solosky/pixl.js/fw/application/src/i18n/de_DE.c

#include "string_id.h"
const char * const lang_de_DE[_L_COUNT] = {
    [_L_ON] = "AN",
    [_L_OFF] = "AUS",
    [_L_ON_F] = "[AN]",
    [_L_OFF_F] = "[AUS]",
    [_L_BACK] = "Zurück",
    [_L_ERR] = "Fehler",
    [_L_ERR_CODE] = "Fehlercode",
    [_L_FAILED] = "",
    [_L_BYTES] = "",
    [_L_APP_AMIIBO] = "Amiibo Emulator",
    [_L_APP_AMIIBOLINK] = "AmiiboLink",
    [_L_APP_BLE] = "BLE Dateitransfer",
    [_L_APP_BLE_TITLE] = "BLE Dateitransfer",
    [_L_APP_PLAYER] = "Videoplayer",
    [_L_APP_SET] = "Einstellungen",
    [_L_APP_SET_VERSION] = "Version",
    [_L_APP_SET_STORAGE_USED] = "Belegt",
    [_L_APP_SET_STORAGE] = "Externer Speicher",
    [_L_APP_SET_OLED_CONTRAST] = "Kontrast",
    [_L_APP_SET_OLED_CONTRAST_TITLE] = "Kontrast",
    [_L_APP_SET_LCD_BACKLIGHT] = "Beleuchtung",
    [_L_APP_SET_LCD_BACKLIGHT_TITLE] = "Helligkeit",
    [_L_APP_SET_ANIM] = "Menü Animation",
    [_L_APP_SET_LIPO_BAT] = "LiPO Batterie",
    [_L_APP_SET_SHOW_MEM_USAGE] = "Speicheranzeige",
    [_L_APP_SET_HIBERNATE] = "Schnelles Aufwachen",
    [_L_APP_SET_SLEEP_TIMEOUT] = "Standby nach",
    [_L_APP_SET_LANGUAGE] = "Sprache",
    [_L_APP_SET_GO_SLEEP] = "",
    [_L_APP_SET_DFU] = "Firmw. Aktualisierung",
    [_L_APP_SET_REBOOT] = "System Neustart",
    [_L_APP_SET_RESET_DEFAULT] = "Standardeinstellungen",
    [_L_APP_SET_RESET_DEFAULT_SUCCESS] = "Einstellungen zurückgesetzt!",
    [_L_APP_SET_RESET_DEFAULT_CONFIRM] = "Auf Standardeinstellungen zurücksetzen?",
    [_L_APP_SET_ABOUT] = "",
    [_L_APP_SET_ABOUT_OPEN_SOURCE_PROJECT] = "",
    [_L_APP_SET_ABOUT_LGPL_LICENSE] = "",
    [_L_APP_SET_APP_MGMT] = "",
    [_L_15S] = "15 Sekunden",
    [_L_30S] = "30 Sekunden",
    [_L_45S] = "45 Sekunden",
    [_L_1MIN] = "1 Minute",
    [_L_2MIN] = "2 Minuten",
    [_L_3MIN] = "3 Minuten",
    [_L_AMIIBO_KEY_UNLOADED] = "Amiibo Schlüssel fehlt",
    [_L_UPLOAD_KEY_RETAIL_BIN] = "Platzieren Sie die Datei key_retail.bin im Hauptverzeichnis des Speichers.",
    [_L_KNOW] = "Verstanden",
    [_L_RANDOM_GENERATION] = "Zufällige UUID",
    [_L_AUTO_RANDOM_GENERATION] = "Zufällige UUID (Automatisch)",
    [_L_SET_CUSTOM_ID] = "",
    [_L_INPUT_ID] = "",
    [_L_INAVLID_ID] = "",
    [_L_SHOW_QRCODE] = "QR Code",
    [_L_READ_ONLY] = "",
    [_L_DELETE_TAG] = "Tag löschen",
    [_L_DELETE_TAG_CONFIRM] = "Löschen von %s bestätigen?",
    [_L_BACK_TO_DETAILS] = "Zurück zu Tag Details",
    [_L_BACK_TO_FILE_LIST] = "Zurück zur Liste",
    [_L_BACK_TO_MAIN_MENU] = "Hauptmenü",
    [_L_FORMAT] = "Formatieren",
    [_L_FORMAT_STORAGE] = "Speicher formatieren",
    [_L_DELETE_ALL_DATA] = "Alle Daten löschen?",
    [_L_DELETING_MESSAGE] = "Formatiere...",
    [_L_MESSAGE] = "Meldung",
    [_L_CONFIRM] = "Bestätigen",
    [_L_CANCEL] = "Abbrechen",
    [_L_BACK_TO_LIST] = "Zurück zur Liste",
    [_L_NOT_MOUNTED] = "Speicher nicht eingebunden",
    [_L_MOUNTED_LFS] = "===Speicher [LFS]===",
    [_L_MOUNTED_FFS] = "===Speicher [FFS]===",
    [_L_TOTAL_SPACE] = "Gesamt",
    [_L_AVAILABLE_SPACE] = "Frei",
    [_L_NOT_AMIIBO_FILE] = "Keine Amiibo Datei",
    [_L_READ_FILE_FAILED] = "Lesen fehlgeschlagen",
    [_L_INPUT_FOLDER_NAME] = "Ordnername eingeben:",
    [_L_INPUT_AMIIBO_NAME] = "Amiibo Namen eingeben:",
    [_L_DELETE_FILE] = "%s löschen ?",
    [_L_DELETE] = "Löschen...",
    [_L_TIPS] = "Bestätigen",
    [_L_INPUT_NEW_NAME] = "Neuen Namen eingeben:",
    [_L_INVALID_INPUT] = "Ungültige Eingabe",
    [_L_CREATE_NEW_FOLDER] = "Neuer Ordner...",
    [_L_CREATE_NEW_TAG] = "Neuer Tag...",
    [_L_CREATE_NEW_TAG_BATCH] = "Mehrere Tags erstellen...",
    [_L_INPUT_TAG_NUM] = "Tag Anzahl eingeben:",
    [_L_CREATE_TOO_MANY_NUM] = "Sie können nur maximal %d Tags auf einmal erstellen.",
    [_L_CREATING_TAG_BATCH] = "Tag erstellen",
    [_L_CREATING_TAG_FAILED] = "Erstellen von Tag %s fehlgeschlagen!",
    [_L_RENAME] = "Umbenennen...",
    [_L_OPEN_FOLDER_FAILED] = "Ordner konnte nicht geöffnet werden",
    [_L_RENAME_FAILED] = "Umbenennen fehlgeschlagen\nFehlercode",
    [_L_MAIN_RETURN] = "[Zurück]",
    [_L_RANDOM_MODE_MANUAL] = "Zufällige UUID (Manuell)",
    [_L_RANDOM_MODE_AUTO] = "Zufällige UUID (Automatisch)",
    [_L_SEQUENCE_MODE] = "Sequentieller Modus",
    [_L_READ_WRITE_MODE] = "Lese-Schreibmodus",
    [_L_AMIIBOLINK_V1] = "V1",
    [_L_AMIIBOLINK_V2] = "V2",
    [_L_AMILOOP] = "AmiLoop",
    [_L_MODE] = "Modus",
    [_L_AUTO_RANDOM] = "Zufällige UUID (Automatisch)",
    [_L_COMPATIBLE_MODE] = "Kompabilitäts Modus",
    [_L_TAG_DETAILS] = "[Zurück zu Details]",
    [_L_MAIN_MENU] = "[Hauptmenü]",
    [_L_MODE_RANDOM] = "Zufällige UUID (Manuell)",
    [_L_MODE_CYCLE] = "Sequentiell",
    [_L_MODE_NTAG] = "Lesen/Schreiben",
    [_L_MODE_RANDOM_AUTO_GEN] = "Zufällig (Auto.)",
    [_L_BLANK_TAG] = "Leerer NFC Tag",
    [_L_APP_AMIIDB] = "Amiibo Datenbank",
    [_L_APP_AMMIDB_BROWSER] = "Navigieren...",
    [_L_APP_AMIIDB_SEARCH] = "Suche...",
    [_L_APP_AMIIDB_MY_FAVORITES] = "Meine Favoriten...",
    [_L_APP_AMIIDB_MY_TAGS] = "Meine Amiibo...",
    [_L_APP_AMIIDB_SETTINGS] = "Einstellungen...",
    [_L_APP_AMIIDB_EXIT] = "[Beenden]",
    [_L_APP_AMIIDB_BACK] = "[Zurück]",
    [_L_APP_AMIIDB_SETTINGS_AMIIBO_KEY] = "Schlüssel",
    [_L_APP_AMIIDB_SETTINGS_AMIIBO_KEY_LOADED] = "geladen",
    [_L_APP_AMIIDB_SETTINGS_AMIIBO_KEY_NOT_LOADED] = "NICHT geladen",
    [_L_APP_AMIIDB_SETTINGS_SLOT_NUM] = "Steckplatzanzahl",
    [_L_APP_AMIIDB_DETAIL_FAVORITE] = "Favorit...",
    [_L_APP_AMIIDB_DETAIL_SAVE_AS] = "Speichern unter...",
    [_L_APP_AMIIDB_DETAIL_BACK_DETAIL] = "[Zurück zu Details]",
    [_L_APP_AMIIDB_DETAIL_BACK_LIST] = "[Zurück zur Liste]",
    [_L_APP_AMIIDB_SEARCH_HEAD] = "Suche:",
    [_L_APP_AMIIDB_MORE] = "[Mehr...]",
    [_L_APP_AMIIDB_MORE_MESSAGE] = "Zu viele Ergebnisse. Bitte Suche eingrenzen.",
    [_L_APP_AMIIDB_EMPTY_TAG] = "<Leerer Amiibo>",
    [_L_APP_AMIIDB_SLOT_DELETE] = "Zurücksetzen...",
    [_L_APP_AMIIDB_CONFIRM] = "Bestätigen",
    [_L_APP_AMIIDB_CANCEL] = "Abbrechen",
    [_L_APP_AMIIDB_TIPS] = "Bestätigen",
    [_L_APP_AMIIDB_NEW] = "Neu...",
    [_L_APP_AMIIDB_EMPTY] = "Leeren...",
    [_L_APP_AMIIDB_DELETE] = "Löschen...",
    [_L_APP_AMIIDB_FAV_NEW_HEAD] = "Neuer Fav.-Ordner:",
    [_L_APP_AMIIDB_FAV_EMPTY_MSG] = "Fav.-Ordner leeren?",
    [_L_APP_AMIIDB_FAV_DELETE_MSG] = "Löschen Bestätigen?",
    [_L_APP_AMIIDB_FAV_SELECT_FOLDER] = "Fav.-Ordner auswählen...",
    [_L_APP_AMIIDB_FAV_SUCCESS] = "Favorit erstellt ",
    [_L_APP_AMIIDB_FAV_FAILED] = "Favorisieren fehlgeschlagen!",
    [_L_APP_AMIIDB_SLOT_SAVE_SUCCESS] = "Speichern erfolgreich",
    [_L_APP_AMIIDB_SLOT_SAVE_FAILED] = "Speichern fehlgeschlagen!",
    [_L_APP_AMIIDB_SORT_FIELD] = "Sortierfeld",
    [_L_APP_AMIIDB_SORT_DEFAULT] = "Standard",
    [_L_APP_AMIIDB_SORT_NAME] = "Name",
    [_L_APP_AMIIDB_NOT_SUPPORT_V3] = "",
    [_L_APP_CHAMELEON] = "Karten Emulator",
    [_L_APP_CHAMELEON_TAG_MF1_WRITE_NORMAL] = "Normal",
    [_L_APP_CHAMELEON_TAG_MF1_WRITE_DENIED] = "Verweigern",
    [_L_APP_CHAMELEON_TAG_MF1_WRITE_DECEIVE] = "Ignorieren",
    [_L_APP_CHAMELEON_TAG_MF1_WRITE_SHADOW] = "Cache",
    [_L_APP_CHAMELEON_INITIALIZING] = "Daten initialisieren...",
    [_L_APP_CHAMELEON_CARD_SLOT] = "Steckplatz",
    [_L_APP_CHAMELEON_CARD_NICK] = "Spitzname",
    [_L_APP_CHAMELEON_CARD_ID] = "ID",
    [_L_APP_CHAMELEON_CARD_TYPE] = "Typ",
    [_L_APP_CHAMELEON_CARD_DATA] = "Daten...",
    [_L_APP_CHAMELEON_CARD_ADVANCED] = "Erweitert...",
    [_L_APP_CHAMELEON_CARD_SLOT_SETTINGS] = "Steckplatz Einstellungen...",
    [_L_APP_CHAMELEON_CARD_SLOT_NUM] = "Steckplatz Nummer",
    [_L_APP_CHAMELEON_CARD_SET_NICK_SUCCESS] = "Spitzname erfolgreich gesetzt",
    [_L_APP_CHAMELEON_CARD_SET_NICK_FAILED] = "Spitzname setzen fehlgeschlagen!",
    [_L_APP_CHAMELEON_CARD_INPUT_NICK] = "Spitznamen eingeben:",
    [_L_APP_CHAMELEON_CARD_DATA_LOAD] = "Laden...",
    [_L_APP_CHAMELEON_CARD_DATA_SAVE] = "Speichern...",
    [_L_APP_CHAMELEON_CARD_DATA_FACTORY] = "Zurücksetzen...",
    [_L_APP_CHAMELEON_CARD_DATA_FACTORY_SUCCESS] = "Daten zurückgesetzt",
    [_L_APP_CHAMELEON_CARD_DATA_LOAD_NOT_FOUND] = "Datei nicht gefunden",
    [_L_APP_CHAMELEON_CARD_DATA_LOAD_SIZE_NOT_MATCH] = "Dateigröße stimmt nicht überein",
    [_L_APP_CHAMELEON_CARD_DATA_LOAD_FAILED] = "Laden der Datei fehlgeschlagen",
    [_L_APP_CHAMELEON_CARD_DATA_LOAD_SUCCESS] = "Datei erfolgreich geladen",
    [_L_APP_CHAMELEON_CARD_DATA_SAVE_INPUT_FILE_NAME] = "Datei Namen eingeben:",
    [_L_APP_CHAMELEON_CARD_DATA_SAVE_FAILED] = "Datei speichern fehlgeschlagen!",
    [_L_APP_CHAMELEON_CARD_DATA_SAVE_SUCCESS] = "Datei erfolgreich gespeichert",
    [_L_APP_CHAMELEON_CARD_ADV_CUSTOM_MODE] = "Benutzerdefinierter Modus",
    [_L_APP_CHAMELEON_CARD_ADV_LOAD_BLOCK0] = "",
    [_L_APP_CHAMELEON_CARD_ADV_LOAD_BLOCK0_SUCCESS] = "",
    [_L_APP_CHAMELEON_CARD_ID_SIZE] = "",
    [_L_APP_CHAMELEON_CARD_GEN1A_MODE] = "Gen1A aktiv",
    [_L_APP_CHAMELEON_CARD_GENERATE_UID] = "Zufällige UID",
    [_L_APP_CHAMELEON_CARD_GENERATE_UID_SUCCESS] = "UID generiert",
    [_L_APP_CHAMELEON_CARD_GEN2_MODE] = "Gen2 aktiv",
    [_L_APP_CHAMELEON_CARD_WRITE_MODE] = "Schreibmodus",
    [_L_APP_CHAMELEON_CARD_ADV_ID_EDIT_INVALID_INPUT] = "Ungültige Eingabe!",
    [_L_APP_CHAMELEON_CARD_TYPE_FACTORY_DATA_CONFRIM] = "Kartentyp geändert. \nKartendaten zurücksetzen?",
    [_L_APP_CHAMELEON_CARD_DEFAULT_CARD] = "",
    [_L_APP_GAME] = "",
    [_L_APP_GAME_TINY_ARKANOID] = "",
    [_L_APP_GAME_TINY_INVADERS] = "",
    [_L_APP_GAME_TINY_LANDER] = "",
    [_L_APP_GAME_TINY_TRIS] = "",
};
