solosky/pixl.js/fw/application/src/i18n/es_ES.c

#include "string_id.h"
const char * const lang_es_ES[_L_COUNT] = {
    [_L_ON] = "SI",
    [_L_OFF] = "NO",
    [_L_ON_F] = "[SI]",
    [_L_OFF_F] = "[NO]",
    [_L_BACK] = "[Atrás]",
    [_L_ERR] = "Error",
    [_L_ERR_CODE] = "Código error",
    [_L_FAILED] = "Fallido",
    [_L_BYTES] = "",
    [_L_APP_AMIIBO] = "Emulador de amiibo",
    [_L_APP_AMIIBOLINK] = "AmiiboLink",
    [_L_APP_BLE] = "Transferencia BLE",
    [_L_APP_BLE_TITLE] = "Transferencia BLE",
    [_L_APP_PLAYER] = "Reproductor vídeo",
    [_L_APP_SET] = "Configuraciones",
    [_L_APP_SET_VERSION] = "Versión",
    [_L_APP_SET_STORAGE_USED] = "Usado",
    [_L_APP_SET_STORAGE] = "M. Flash",
    [_L_APP_SET_OLED_CONTRAST] = "Contraste",
    [_L_APP_SET_OLED_CONTRAST_TITLE] = "Contraste",
    [_L_APP_SET_LCD_BACKLIGHT] = "Brillo",
    [_L_APP_SET_LCD_BACKLIGHT_TITLE] = "Brillo de fondo",
    [_L_APP_SET_ANIM] = "Animar menú",
    [_L_APP_SET_LIPO_BAT] = "Batería LiPO",
    [_L_APP_SET_SHOW_MEM_USAGE] = "Estad. Mem.",
    [_L_APP_SET_HIBERNATE] = "Hibernar",
    [_L_APP_SET_SLEEP_TIMEOUT] = "Dormir en:",
    [_L_APP_SET_LANGUAGE] = "Idioma",
    [_L_APP_SET_GO_SLEEP] = "Dormir",
    [_L_APP_SET_DFU] = "Actualizar firmware",
    [_L_APP_SET_REBOOT] = "Reiniciar",
    [_L_APP_SET_RESET_DEFAULT] = "Restablecer config.",
    [_L_APP_SET_RESET_DEFAULT_SUCCESS] = "¡Configuración Restablecida!",
    [_L_APP_SET_RESET_DEFAULT_CONFIRM] = "¿Confirma Restablecer\nConfig.?",
    [_L_APP_SET_ABOUT] = "Acerca del dispositivo",
    [_L_APP_SET_ABOUT_OPEN_SOURCE_PROJECT] = "Poyecto de código abierto",
    [_L_APP_SET_ABOUT_LGPL_LICENSE] = "Licencia GPL 2.0",
    [_L_APP_SET_APP_MGMT] = "",
    [_L_15S] = "15 segundos",
    [_L_30S] = "30 segundos",
    [_L_45S] = "45 segundos",
    [_L_1MIN] = "1 minuto",
    [_L_2MIN] = "2 minutos",
    [_L_3MIN] = "3 minutos",
    [_L_AMIIBO_KEY_UNLOADED] = "Sin llave amiibo",
    [_L_UPLOAD_KEY_RETAIL_BIN] = "Suba el archivo\nkey_retail.bin\nal directorio raíz.",
    [_L_KNOW] = "Entendido",
    [_L_RANDOM_GENERATION] = "Nuevo serial aleat.",
    [_L_AUTO_RANDOM_GENERATION] = "Serial alea. aut",
    [_L_SET_CUSTOM_ID] = "Asignar ID personalizado",
    [_L_INPUT_ID] = "Ingrese ID",
    [_L_INAVLID_ID] = "ID inválido",
    [_L_SHOW_QRCODE] = "Mostrar QR",
    [_L_READ_ONLY] = "Solo Lectura",
    [_L_DELETE_TAG] = "Borrar amiibo...",
    [_L_DELETE_TAG_CONFIRM] = "¿Borrar %s?",
    [_L_BACK_TO_DETAILS] = "[Detalles amiibo]",
    [_L_BACK_TO_FILE_LIST] = "[Lista Archivos]",
    [_L_BACK_TO_MAIN_MENU] = "[Menú Principal]",
    [_L_FORMAT] = "Formatear...",
    [_L_FORMAT_STORAGE] = "Formatear mem. Flash",
    [_L_DELETE_ALL_DATA] = "Se borrará todos los\ndatos.",
    [_L_DELETING_MESSAGE] = "Formateando...",
    [_L_MESSAGE] = "Inicializar",
    [_L_CONFIRM] = "Confirmar",
    [_L_CANCEL] = "Cancelar",
    [_L_BACK_TO_LIST] = "[Voler a lista]",
    [_L_NOT_MOUNTED] = "No montado",
    [_L_MOUNTED_LFS] = "===[LFS]Montado===",
    [_L_MOUNTED_FFS] = "===[FFS]Montado===",
    [_L_TOTAL_SPACE] = "Capacidad",
    [_L_AVAILABLE_SPACE] = "Libre",
    [_L_NOT_AMIIBO_FILE] = "Este no es un archivo\namiibo válido",
    [_L_READ_FILE_FAILED] = "Error al leer archivo",
    [_L_INPUT_FOLDER_NAME] = "Nombre carpeta:",
    [_L_INPUT_AMIIBO_NAME] = "Nombre amiibo:",
    [_L_DELETE_FILE] = "¿Borrar %s?",
    [_L_DELETE] = "Borrar...",
    [_L_TIPS] = "Confirmar",
    [_L_INPUT_NEW_NAME] = "Nuevo nombre:",
    [_L_INVALID_INPUT] = "Entrada inválida",
    [_L_CREATE_NEW_FOLDER] = "Crear carpeta...",
    [_L_CREATE_NEW_TAG] = "Crear amiibo...",
    [_L_CREATE_NEW_TAG_BATCH] = "Crear amiibo en lote...",
    [_L_INPUT_TAG_NUM] = "¿Cuántos?",
    [_L_CREATE_TOO_MANY_NUM] = "Sólo se puede crear %d en lote",
    [_L_CREATING_TAG_BATCH] = "Creando...",
    [_L_CREATING_TAG_FAILED] = "¡Error al crear %s!",
    [_L_RENAME] = "Renombrar...",
    [_L_OPEN_FOLDER_FAILED] = "Fallo al abrir carpeta",
    [_L_RENAME_FAILED] = "Fallo al renombrar\nCódigo de error",
    [_L_MAIN_RETURN] = "[Volver]",
    [_L_RANDOM_MODE_MANUAL] = "Aleatorio (Manual)",
    [_L_RANDOM_MODE_AUTO] = "Aleatorio (Auto.)",
    [_L_SEQUENCE_MODE] = "Modo Secuencial",
    [_L_READ_WRITE_MODE] = "Modo Lectura/Escrit.",
    [_L_AMIIBOLINK_V1] = "AmiiboLink V1",
    [_L_AMIIBOLINK_V2] = "AmiiboLink V2",
    [_L_AMILOOP] = "AmiLoop",
    [_L_MODE] = "Modo",
    [_L_AUTO_RANDOM] = "Aleat. autom.",
    [_L_COMPATIBLE_MODE] = "Compatibil.",
    [_L_TAG_DETAILS] = "[Volver a Detalles]",
    [_L_MAIN_MENU] = "[Menú Principal]",
    [_L_MODE_RANDOM] = "Aleat. man.",
    [_L_MODE_CYCLE] = "Secuencial",
    [_L_MODE_NTAG] = "Lect./Escr.",
    [_L_MODE_RANDOM_AUTO_GEN] = "Aleat. auto.",
    [_L_BLANK_TAG] = "Amiibo no asignado",
    [_L_APP_AMIIDB] = "Base datos amiibo",
    [_L_APP_AMMIDB_BROWSER] = "Explorar...",
    [_L_APP_AMIIDB_SEARCH] = "Buscar...",
    [_L_APP_AMIIDB_MY_FAVORITES] = "Mis Favoritos...",
    [_L_APP_AMIIDB_MY_TAGS] = "Mis amiibo...",
    [_L_APP_AMIIDB_SETTINGS] = "Configuraciones...",
    [_L_APP_AMIIDB_EXIT] = "[Menú Principal]",
    [_L_APP_AMIIDB_BACK] = "[Volver]",
    [_L_APP_AMIIDB_SETTINGS_AMIIBO_KEY] = "Llaves",
    [_L_APP_AMIIDB_SETTINGS_AMIIBO_KEY_LOADED] = "Cargadas",
    [_L_APP_AMIIDB_SETTINGS_AMIIBO_KEY_NOT_LOADED] = "NO cargadas",
    [_L_APP_AMIIDB_SETTINGS_SLOT_NUM] = "Cant. ranuras",
    [_L_APP_AMIIDB_DETAIL_FAVORITE] = "Favorito...",
    [_L_APP_AMIIDB_DETAIL_SAVE_AS] = "Asignar en...",
    [_L_APP_AMIIDB_DETAIL_BACK_DETAIL] = "[Volver a Detalles]",
    [_L_APP_AMIIDB_DETAIL_BACK_LIST] = "[Volver a Lista]",
    [_L_APP_AMIIDB_SEARCH_HEAD] = "Buscar:",
    [_L_APP_AMIIDB_MORE] = "[Más...]",
    [_L_APP_AMIIDB_MORE_MESSAGE] = "",
    [_L_APP_AMIIDB_EMPTY_TAG] = "<No Asignado>",
    [_L_APP_AMIIDB_SLOT_DELETE] = "Borrar...",
    [_L_APP_AMIIDB_CONFIRM] = "Confirmar",
    [_L_APP_AMIIDB_CANCEL] = "Cancelar",
    [_L_APP_AMIIDB_TIPS] = "Confirmar",
    [_L_APP_AMIIDB_NEW] = "Nueva...",
    [_L_APP_AMIIDB_EMPTY] = "Vaciar...",
    [_L_APP_AMIIDB_DELETE] = "Borrar...",
    [_L_APP_AMIIDB_FAV_NEW_HEAD] = "Nueva Carp. Favoritos:",
    [_L_APP_AMIIDB_FAV_EMPTY_MSG] = "¿Vaciar Carp. Favoritos?",
    [_L_APP_AMIIDB_FAV_DELETE_MSG] = "¿Confirma borrado?",
    [_L_APP_AMIIDB_FAV_SELECT_FOLDER] = "Selec. carp. favoritos...",
    [_L_APP_AMIIDB_FAV_SUCCESS] = "¡Adicionado a Favoritos!",
    [_L_APP_AMIIDB_FAV_FAILED] = "¡Fallo al adicionar\na Favoritos!",
    [_L_APP_AMIIDB_SLOT_SAVE_SUCCESS] = "Asignación correcta",
    [_L_APP_AMIIDB_SLOT_SAVE_FAILED] = "¡Asignación fallida!",
    [_L_APP_AMIIDB_SORT_FIELD] = "Campo de ordenación",
    [_L_APP_AMIIDB_SORT_DEFAULT] = "Por defecto",
    [_L_APP_AMIIDB_SORT_NAME] = "Nombre",
    [_L_APP_AMIIDB_NOT_SUPPORT_V3] = "",
    [_L_APP_CHAMELEON] = "Emular Etiqueta RFID",
    [_L_APP_CHAMELEON_TAG_MF1_WRITE_NORMAL] = "Normal",
    [_L_APP_CHAMELEON_TAG_MF1_WRITE_DENIED] = "Negar",
    [_L_APP_CHAMELEON_TAG_MF1_WRITE_DECEIVE] = "Ignorar",
    [_L_APP_CHAMELEON_TAG_MF1_WRITE_SHADOW] = "Caché",
    [_L_APP_CHAMELEON_INITIALIZING] = "Inicializando ambiente.\nPor favor espere...",
    [_L_APP_CHAMELEON_CARD_SLOT] = "Ranura",
    [_L_APP_CHAMELEON_CARD_NICK] = "Apodo",
    [_L_APP_CHAMELEON_CARD_ID] = "ID",
    [_L_APP_CHAMELEON_CARD_TYPE] = "Tipo",
    [_L_APP_CHAMELEON_CARD_DATA] = "Datos...",
    [_L_APP_CHAMELEON_CARD_ADVANCED] = "Avanzado...",
    [_L_APP_CHAMELEON_CARD_SLOT_SETTINGS] = "Configuración...",
    [_L_APP_CHAMELEON_CARD_SLOT_NUM] = "Cant. ranuras...",
    [_L_APP_CHAMELEON_CARD_SET_NICK_SUCCESS] = "Apodo cambiado.",
    [_L_APP_CHAMELEON_CARD_SET_NICK_FAILED] = "¡Falló cambio apodo!",
    [_L_APP_CHAMELEON_CARD_INPUT_NICK] = "Apodo:",
    [_L_APP_CHAMELEON_CARD_DATA_LOAD] = "Cargar...",
    [_L_APP_CHAMELEON_CARD_DATA_SAVE] = "Guardar...",
    [_L_APP_CHAMELEON_CARD_DATA_FACTORY] = "Inicializar...",
    [_L_APP_CHAMELEON_CARD_DATA_FACTORY_SUCCESS] = "¡Datos inicializados!",
    [_L_APP_CHAMELEON_CARD_DATA_LOAD_NOT_FOUND] = "Archivo no encontrado",
    [_L_APP_CHAMELEON_CARD_DATA_LOAD_SIZE_NOT_MATCH] = "Tamaño archivo incorrecto",
    [_L_APP_CHAMELEON_CARD_DATA_LOAD_FAILED] = "Falla al cargar archivo",
    [_L_APP_CHAMELEON_CARD_DATA_LOAD_SUCCESS] = "Carga archivo correcta",
    [_L_APP_CHAMELEON_CARD_DATA_SAVE_INPUT_FILE_NAME] = "Nombre archivo:",
    [_L_APP_CHAMELEON_CARD_DATA_SAVE_FAILED] = "¡Error al guardar!",
    [_L_APP_CHAMELEON_CARD_DATA_SAVE_SUCCESS] = "Guardado correcto",
    [_L_APP_CHAMELEON_CARD_ADV_CUSTOM_MODE] = "Modo personali.",
    [_L_APP_CHAMELEON_CARD_ADV_LOAD_BLOCK0] = "",
    [_L_APP_CHAMELEON_CARD_ADV_LOAD_BLOCK0_SUCCESS] = "",
    [_L_APP_CHAMELEON_CARD_ID_SIZE] = "",
    [_L_APP_CHAMELEON_CARD_GEN1A_MODE] = "Gen1A habilitada",
    [_L_APP_CHAMELEON_CARD_GENERATE_UID] = "Generar UID aleat.",
    [_L_APP_CHAMELEON_CARD_GENERATE_UID_SUCCESS] = "UID generado",
    [_L_APP_CHAMELEON_CARD_GEN2_MODE] = "Gen2 habilitada",
    [_L_APP_CHAMELEON_CARD_WRITE_MODE] = "Modo escrit.",
    [_L_APP_CHAMELEON_CARD_ADV_ID_EDIT_INVALID_INPUT] = "¡Entrada inválida!",
    [_L_APP_CHAMELEON_CARD_TYPE_FACTORY_DATA_CONFRIM] = "Tipo tarjeta modificado\n¿Inicializar tarjeta?",
    [_L_APP_CHAMELEON_CARD_DEFAULT_CARD] = "Tarjeta Predeterminada",
    [_L_APP_GAME] = "Juegos",
    [_L_APP_GAME_TINY_ARKANOID] = "Arkanoid",
    [_L_APP_GAME_TINY_INVADERS] = "Invasores",
    [_L_APP_GAME_TINY_LANDER] = "Lander",
    [_L_APP_GAME_TINY_TRIS] = "Tris",
};
