solosky/pixl.js/fw/application/src/i18n/fr_FR.c

#include "string_id.h"
const char * const lang_fr_FR[_L_COUNT] = {
    [_L_ON] = "ACTIVÉ",
    [_L_OFF] = "DÉSACTIVÉ",
    [_L_ON_F] = "[ACTIVÉ]",
    [_L_OFF_F] = "[DÉSACTIVÉ]",
    [_L_BACK] = "Retour",
    [_L_ERR] = "Erreur",
    [_L_ERR_CODE] = "Code d'Erreur",
    [_L_FAILED] = "",
    [_L_BYTES] = "",
    [_L_APP_AMIIBO] = "Emulateur Amiibo",
    [_L_APP_AMIIBOLINK] = "AmiiboLink",
    [_L_APP_BLE] = "Transfert de Fichiers BLE",
    [_L_APP_BLE_TITLE] = "Transfert de Fichiers BLE",
    [_L_APP_PLAYER] = "Lecteur Vidéo",
    [_L_APP_SET] = "Paramètres",
    [_L_APP_SET_VERSION] = "Version",
    [_L_APP_SET_STORAGE_USED] = "Utilisé",
    [_L_APP_SET_STORAGE] = "Stockage Externe",
    [_L_APP_SET_OLED_CONTRAST] = "Contraste",
    [_L_APP_SET_OLED_CONTRAST_TITLE] = "Contraste",
    [_L_APP_SET_LCD_BACKLIGHT] = "Rétroéclairage",
    [_L_APP_SET_LCD_BACKLIGHT_TITLE] = "Luminosité du Rétroéclairage",
    [_L_APP_SET_ANIM] = "Animation du Menu",
    [_L_APP_SET_LIPO_BAT] = "Batterie LiPO",
    [_L_APP_SET_SHOW_MEM_USAGE] = "Mémoire Utilisée",
    [_L_APP_SET_HIBERNATE] = "Réveil Rapide",
    [_L_APP_SET_SLEEP_TIMEOUT] = "Délai de mise en veille",
    [_L_APP_SET_LANGUAGE] = "Langue",
    [_L_APP_SET_GO_SLEEP] = "",
    [_L_APP_SET_DFU] = "Mise à Jour du Micrologiciel",
    [_L_APP_SET_REBOOT] = "Redémarrage du Système",
    [_L_APP_SET_RESET_DEFAULT] = "Rétablir les Paramètres par Défaut",
    [_L_APP_SET_RESET_DEFAULT_SUCCESS] = "Réinitialiser les Paramètres Par Défaut",
    [_L_APP_SET_RESET_DEFAULT_CONFIRM] = "",
    [_L_APP_SET_ABOUT] = "",
    [_L_APP_SET_ABOUT_OPEN_SOURCE_PROJECT] = "",
    [_L_APP_SET_ABOUT_LGPL_LICENSE] = "",
    [_L_APP_SET_APP_MGMT] = "",
    [_L_15S] = "15 sec.",
    [_L_30S] = "30 sec.",
    [_L_45S] = "45 sec.",
    [_L_1MIN] = "1 min.",
    [_L_2MIN] = "2 min.",
    [_L_3MIN] = "3 min.",
    [_L_AMIIBO_KEY_UNLOADED] = "Clé Amiibo Non Chargée",
    [_L_UPLOAD_KEY_RETAIL_BIN] = "Téléchargez le fichier key_retail.bin dans le répertoire racine du stockage.",
    [_L_KNOW] = "Compris",
    [_L_RANDOM_GENERATION] = "Randomiser la Balise",
    [_L_AUTO_RANDOM_GENERATION] = "Randomisation Automatique",
    [_L_SET_CUSTOM_ID] = "",
    [_L_INPUT_ID] = "",
    [_L_INAVLID_ID] = "",
    [_L_SHOW_QRCODE] = "Afficher le Code QR",
    [_L_READ_ONLY] = "",
    [_L_DELETE_TAG] = "Supprimer la Balise",
    [_L_DELETE_TAG_CONFIRM] = "Confirmer la Suppression de %s ?",
    [_L_BACK_TO_DETAILS] = "Retour Aux Détails de L'étiquette",
    [_L_BACK_TO_FILE_LIST] = "Retour à La Liste Des Fichiers",
    [_L_BACK_TO_MAIN_MENU] = "Retour au Menu Principal",
    [_L_FORMAT] = "Format",
    [_L_FORMAT_STORAGE] = "Format de Stockage",
    [_L_DELETE_ALL_DATA] = "Cette opération efface toutes les données. Confirmer le formatage?",
    [_L_DELETING_MESSAGE] = "Formatage ...",
    [_L_MESSAGE] = "Message",
    [_L_CONFIRM] = "Confirmer",
    [_L_CANCEL] = "Annuler",
    [_L_BACK_TO_LIST] = "Retour à La Liste",
    [_L_NOT_MOUNTED] = "Stockage non Monté",
    [_L_MOUNTED_LFS] = "===Monté[LFS]===",
    [_L_MOUNTED_FFS] = "===Monté[FFS]===",
    [_L_TOTAL_SPACE] = "Total",
    [_L_AVAILABLE_SPACE] = "Libre",
    [_L_NOT_AMIIBO_FILE] = "Ce n'est pas un fichier Amiibo",
    [_L_READ_FILE_FAILED] = "Échec de la lecture du fichier",
    [_L_INPUT_FOLDER_NAME] = "Nom du Dossier D'entrée:",
    [_L_INPUT_AMIIBO_NAME] = "Nom de l'Amiibo D'entrée:",
    [_L_DELETE_FILE] = "Supprimer le %s ?",
    [_L_DELETE] = "Supprimer...",
    [_L_TIPS] = "Confirmer",
    [_L_INPUT_NEW_NAME] = "Nouveau nom D'entrée:",
    [_L_INVALID_INPUT] = "Entrée Invalide",
    [_L_CREATE_NEW_FOLDER] = "Créer un Nouveau Dossier...",
    [_L_CREATE_NEW_TAG] = "Créer une Nouvelle Étiquette...",
    [_L_CREATE_NEW_TAG_BATCH] = "Créer de Nouvelles Étiquettes Par Lot...",
    [_L_INPUT_TAG_NUM] = "Saisir le Numéro de l'Étiquette:",
    [_L_CREATE_TOO_MANY_NUM] = "Seulement %d balises maximum créées dans un lot.",
    [_L_CREATING_TAG_BATCH] = "Création d'une balise",
    [_L_CREATING_TAG_FAILED] = "La création de la balise %s a échoué!",
    [_L_RENAME] = "Renommer...",
    [_L_OPEN_FOLDER_FAILED] = "Échec de l'ouverture du dossier",
    [_L_RENAME_FAILED] = "Échec du renommage.\nCode d'Erreur",
    [_L_MAIN_RETURN] = "[RETOUR]",
    [_L_RANDOM_MODE_MANUAL] = "Randomiser (Manuel)",
    [_L_RANDOM_MODE_AUTO] = "Randomiser (Automatique)",
    [_L_SEQUENCE_MODE] = "Mode Séquentiel",
    [_L_READ_WRITE_MODE] = "Mode Lecture-Écriture",
    [_L_AMIIBOLINK_V1] = "V1",
    [_L_AMIIBOLINK_V2] = "V2",
    [_L_AMILOOP] = "AmiLoop",
    [_L_MODE] = "Mode",
    [_L_AUTO_RANDOM] = "Randomisation Automatique",
    [_L_COMPATIBLE_MODE] = "Mode Compatible",
    [_L_TAG_DETAILS] = "[Détails de l'Étiquette]",
    [_L_MAIN_MENU] = "[Menu Principal]",
    [_L_MODE_RANDOM] = "Aléatoire (Manuel)",
    [_L_MODE_CYCLE] = "Séquentiel",
    [_L_MODE_NTAG] = "Lecture/Écriture",
    [_L_MODE_RANDOM_AUTO_GEN] = "Aléatoire (Automatique)",
    [_L_BLANK_TAG] = "Étiquette NFC vierge",
    [_L_APP_AMIIDB] = "Base de Données Amiibo",
    [_L_APP_AMMIDB_BROWSER] = "Naviguer...",
    [_L_APP_AMIIDB_SEARCH] = "Recherche...",
    [_L_APP_AMIIDB_MY_FAVORITES] = "Mes Favoris...",
    [_L_APP_AMIIDB_MY_TAGS] = "Mes Amiibo...",
    [_L_APP_AMIIDB_SETTINGS] = "Paramètres...",
    [_L_APP_AMIIDB_EXIT] = "[Quitter]",
    [_L_APP_AMIIDB_BACK] = "[Retour]",
    [_L_APP_AMIIDB_SETTINGS_AMIIBO_KEY] = "Touches",
    [_L_APP_AMIIDB_SETTINGS_AMIIBO_KEY_LOADED] = "Chargée",
    [_L_APP_AMIIDB_SETTINGS_AMIIBO_KEY_NOT_LOADED] = "NON Chargée",
    [_L_APP_AMIIDB_SETTINGS_SLOT_NUM] = "Numéro d'Emplacement",
    [_L_APP_AMIIDB_DETAIL_FAVORITE] = "Favorite...",
    [_L_APP_AMIIDB_DETAIL_SAVE_AS] = "Enregistrer Sous...",
    [_L_APP_AMIIDB_DETAIL_BACK_DETAIL] = "[Retour au Détail]",
    [_L_APP_AMIIDB_DETAIL_BACK_LIST] = "[Retour à la Liste]",
    [_L_APP_AMIIDB_SEARCH_HEAD] = "Recherche:",
    [_L_APP_AMIIDB_MORE] = "[Plus...]",
    [_L_APP_AMIIDB_MORE_MESSAGE] = "",
    [_L_APP_AMIIDB_EMPTY_TAG] = "<Amiibo Vierge>",
    [_L_APP_AMIIDB_SLOT_DELETE] = "Réinitialiser...",
    [_L_APP_AMIIDB_CONFIRM] = "Confirmer",
    [_L_APP_AMIIDB_CANCEL] = "Annuler",
    [_L_APP_AMIIDB_TIPS] = "Confirmer",
    [_L_APP_AMIIDB_NEW] = "Nouveau...",
    [_L_APP_AMIIDB_EMPTY] = "Vider...",
    [_L_APP_AMIIDB_DELETE] = "Supprimer...",
    [_L_APP_AMIIDB_FAV_NEW_HEAD] = "Nouveau Dossier Favori:",
    [_L_APP_AMIIDB_FAV_EMPTY_MSG] = "Vider le Dossier Favori?",
    [_L_APP_AMIIDB_FAV_DELETE_MSG] = "Confirmer la Suppression?",
    [_L_APP_AMIIDB_FAV_SELECT_FOLDER] = "Sélectionner le Dossier Favori...",
    [_L_APP_AMIIDB_FAV_SUCCESS] = "Succès du Favori",
    [_L_APP_AMIIDB_FAV_FAILED] = "Échec du Favori!",
    [_L_APP_AMIIDB_SLOT_SAVE_SUCCESS] = "Sauvegarder Succès",
    [_L_APP_AMIIDB_SLOT_SAVE_FAILED] = "Sauvegarde Échouée!",
    [_L_APP_AMIIDB_SORT_FIELD] = "Champ de tri",
    [_L_APP_AMIIDB_SORT_DEFAULT] = "Par défaut",
    [_L_APP_AMIIDB_SORT_NAME] = "Nom",
    [_L_APP_AMIIDB_NOT_SUPPORT_V3] = "",
    [_L_APP_CHAMELEON] = "Emulateur de Carte",
    [_L_APP_CHAMELEON_TAG_MF1_WRITE_NORMAL] = "Normal",
    [_L_APP_CHAMELEON_TAG_MF1_WRITE_DENIED] = "Refuser",
    [_L_APP_CHAMELEON_TAG_MF1_WRITE_DECEIVE] = "Ignorer",
    [_L_APP_CHAMELEON_TAG_MF1_WRITE_SHADOW] = "Cache",
    [_L_APP_CHAMELEON_INITIALIZING] = "Initialisation des données ...",
    [_L_APP_CHAMELEON_CARD_SLOT] = "Fente",
    [_L_APP_CHAMELEON_CARD_NICK] = "Pseudo",
    [_L_APP_CHAMELEON_CARD_ID] = "ID",
    [_L_APP_CHAMELEON_CARD_TYPE] = "Type de Données",
    [_L_APP_CHAMELEON_CARD_DATA] = "Données...",
    [_L_APP_CHAMELEON_CARD_ADVANCED] = "Avancé...",
    [_L_APP_CHAMELEON_CARD_SLOT_SETTINGS] = "Paramètres des Emplacements...",
    [_L_APP_CHAMELEON_CARD_SLOT_NUM] = "Numéro d'Emplacement...",
    [_L_APP_CHAMELEON_CARD_SET_NICK_SUCCESS] = "Définir le Pseudo Succès",
    [_L_APP_CHAMELEON_CARD_SET_NICK_FAILED] = "Définir le Pseudo a Échoué!",
    [_L_APP_CHAMELEON_CARD_INPUT_NICK] = "Entrer le Pseudo:",
    [_L_APP_CHAMELEON_CARD_DATA_LOAD] = "Charger...",
    [_L_APP_CHAMELEON_CARD_DATA_SAVE] = "Sauvegarder...",
    [_L_APP_CHAMELEON_CARD_DATA_FACTORY] = "Rétablir Les Valeurs Par Défaut...",
    [_L_APP_CHAMELEON_CARD_DATA_FACTORY_SUCCESS] = "Réinitialisation des Données Succès",
    [_L_APP_CHAMELEON_CARD_DATA_LOAD_NOT_FOUND] = "Fichier Non Trouvé",
    [_L_APP_CHAMELEON_CARD_DATA_LOAD_SIZE_NOT_MATCH] = "La Taille du Fichier ne Correspond Pas",
    [_L_APP_CHAMELEON_CARD_DATA_LOAD_FAILED] = "Échec du Chargement du Fichier",
    [_L_APP_CHAMELEON_CARD_DATA_LOAD_SUCCESS] = "Chargement du Fichier Réussi",
    [_L_APP_CHAMELEON_CARD_DATA_SAVE_INPUT_FILE_NAME] = "Saisir le Nom du Fichier:",
    [_L_APP_CHAMELEON_CARD_DATA_SAVE_FAILED] = "Échec de l'Enregistrement du Fichier!",
    [_L_APP_CHAMELEON_CARD_DATA_SAVE_SUCCESS] = "Sauvegarde du Fichier Réussie",
    [_L_APP_CHAMELEON_CARD_ADV_CUSTOM_MODE] = "Mode Personnalisé",
    [_L_APP_CHAMELEON_CARD_ADV_LOAD_BLOCK0] = "",
    [_L_APP_CHAMELEON_CARD_ADV_LOAD_BLOCK0_SUCCESS] = "",
    [_L_APP_CHAMELEON_CARD_ID_SIZE] = "",
    [_L_APP_CHAMELEON_CARD_GEN1A_MODE] = "Gen1A Activé",
    [_L_APP_CHAMELEON_CARD_GENERATE_UID] = "Randomiser l'UID",
    [_L_APP_CHAMELEON_CARD_GENERATE_UID_SUCCESS] = "UID Généré",
    [_L_APP_CHAMELEON_CARD_GEN2_MODE] = "Gen2 Activé",
    [_L_APP_CHAMELEON_CARD_WRITE_MODE] = "Mode d'Écriture",
    [_L_APP_CHAMELEON_CARD_ADV_ID_EDIT_INVALID_INPUT] = "Entrée Invalide!",
    [_L_APP_CHAMELEON_CARD_TYPE_FACTORY_DATA_CONFRIM] = "Le Type de Carte a Été Modifié. \nRéinitialiser les Données de la Carte?",
    [_L_APP_CHAMELEON_CARD_DEFAULT_CARD] = "",
    [_L_APP_GAME] = "",
    [_L_APP_GAME_TINY_ARKANOID] = "",
    [_L_APP_GAME_TINY_INVADERS] = "",
    [_L_APP_GAME_TINY_LANDER] = "",
    [_L_APP_GAME_TINY_TRIS] = "",
};
