solosky/pixl.js/fw/application/src/i18n/hu_HU.c

#include "string_id.h"
const char * const lang_hu_HU[_L_COUNT] = {
    [_L_ON] = "BE",
    [_L_OFF] = "KI",
    [_L_ON_F] = "[BE]",
    [_L_OFF_F] = "[KI]",
    [_L_BACK] = "Vissza",
    [_L_ERR] = "Hiba",
    [_L_ERR_CODE] = "Hibakód",
    [_L_FAILED] = "",
    [_L_BYTES] = "",
    [_L_APP_AMIIBO] = "Amiibo Emulátor",
    [_L_APP_AMIIBOLINK] = "AmiiboLink",
    [_L_APP_BLE] = "BLE Fájltovábbítás",
    [_L_APP_BLE_TITLE] = "BLE Fájltovábbítás",
    [_L_APP_PLAYER] = "Video Lejátszó",
    [_L_APP_SET] = "Beállítások",
    [_L_APP_SET_VERSION] = "Verzió",
    [_L_APP_SET_STORAGE_USED] = "Használt",
    [_L_APP_SET_STORAGE] = "Külső Tároló",
    [_L_APP_SET_OLED_CONTRAST] = "Kontraszt",
    [_L_APP_SET_OLED_CONTRAST_TITLE] = "Kontraszt",
    [_L_APP_SET_LCD_BACKLIGHT] = "Háttérvilágítás",
    [_L_APP_SET_LCD_BACKLIGHT_TITLE] = "Háttérvilágítás Fényerő",
    [_L_APP_SET_ANIM] = "Menü Animáció",
    [_L_APP_SET_LIPO_BAT] = "LiPO Akkumulátor",
    [_L_APP_SET_SHOW_MEM_USAGE] = "Használt Memória",
    [_L_APP_SET_HIBERNATE] = "Gyors Ébresztés",
    [_L_APP_SET_SLEEP_TIMEOUT] = "Alvási Időkorlát",
    [_L_APP_SET_LANGUAGE] = "Nyelv",
    [_L_APP_SET_GO_SLEEP] = "",
    [_L_APP_SET_DFU] = "Firmware Frissítés",
    [_L_APP_SET_REBOOT] = "Rendszer Újraindítása",
    [_L_APP_SET_RESET_DEFAULT] = "Alapért. Beállítás Visszaállítása",
    [_L_APP_SET_RESET_DEFAULT_SUCCESS] = "Alapért. Beállítások Visszaállítása",
    [_L_APP_SET_RESET_DEFAULT_CONFIRM] = "",
    [_L_APP_SET_ABOUT] = "",
    [_L_APP_SET_ABOUT_OPEN_SOURCE_PROJECT] = "",
    [_L_APP_SET_ABOUT_LGPL_LICENSE] = "",
    [_L_APP_SET_APP_MGMT] = "",
    [_L_15S] = "15 sec.",
    [_L_30S] = "30 sec.",
    [_L_45S] = "45 sec.",
    [_L_1MIN] = "1 min.",
    [_L_2MIN] = "2 min.",
    [_L_3MIN] = "3 min.",
    [_L_AMIIBO_KEY_UNLOADED] = "Amiibo kulcs nincs betöltve",
    [_L_UPLOAD_KEY_RETAIL_BIN] = "Töltse fel a key_retail.bin fájlt a gyökérkönyvtárába.",
    [_L_KNOW] = "Megvan",
    [_L_RANDOM_GENERATION] = "Véletlengenerátor",
    [_L_AUTO_RANDOM_GENERATION] = "Automat. Véletlengenerátor",
    [_L_SET_CUSTOM_ID] = "",
    [_L_INPUT_ID] = "",
    [_L_INAVLID_ID] = "",
    [_L_SHOW_QRCODE] = "QR-kód Megjelenítése",
    [_L_READ_ONLY] = "",
    [_L_DELETE_TAG] = "Címke Törlése",
    [_L_DELETE_TAG_CONFIRM] = "Törlés Megerősítése?",
    [_L_BACK_TO_DETAILS] = "Vissza a Címke Részletkhez",
    [_L_BACK_TO_FILE_LIST] = "Vissza a Fájl Listához",
    [_L_BACK_TO_MAIN_MENU] = "Vissza a Főmenübe",
    [_L_FORMAT] = "Formátum ",
    [_L_FORMAT_STORAGE] = "Formátum Tárolás",
    [_L_DELETE_ALL_DATA] = "Minden adatot töröl. Formázás megerősítése?",
    [_L_DELETING_MESSAGE] = "Formázás ...",
    [_L_MESSAGE] = "Üzenet",
    [_L_CONFIRM] = "Megerősítés",
    [_L_CANCEL] = "Megszüntet",
    [_L_BACK_TO_LIST] = "Vissza a Listához",
    [_L_NOT_MOUNTED] = "Nincs Felszerelve",
    [_L_MOUNTED_LFS] = "===Szerelt[LFS]===",
    [_L_MOUNTED_FFS] = "===Szerelt[FFS]===",
    [_L_TOTAL_SPACE] = "Össz.",
    [_L_AVAILABLE_SPACE] = "Ingyenes",
    [_L_NOT_AMIIBO_FILE] = "Ez nem Amiibo Fájl",
    [_L_READ_FILE_FAILED] = "Fájl beolvasása sikerten",
    [_L_INPUT_FOLDER_NAME] = "Bemeneti Mappa Neve:",
    [_L_INPUT_AMIIBO_NAME] = "Amiibo Neve:",
    [_L_DELETE_FILE] = "Törli a %s fájlt?",
    [_L_DELETE] = "Töröl...",
    [_L_TIPS] = "Megerősítés",
    [_L_INPUT_NEW_NAME] = "Új Név Bevitele:",
    [_L_INVALID_INPUT] = "Érvénytelen Bemenet",
    [_L_CREATE_NEW_FOLDER] = "Új Mappa Létrehozása...",
    [_L_CREATE_NEW_TAG] = "Új Címke Létrehozása...",
    [_L_CREATE_NEW_TAG_BATCH] = "Kötegelt Új Címke Létrehozása...",
    [_L_INPUT_TAG_NUM] = "Beviteli Címke Száma:",
    [_L_CREATE_TOO_MANY_NUM] = "Max. létrehozható címke egy kötegben %d",
    [_L_CREATING_TAG_BATCH] = "Címke létrehozása",
    [_L_CREATING_TAG_FAILED] = "Címke létrehozása %s sikertelen!",
    [_L_RENAME] = "Átnevezés...",
    [_L_OPEN_FOLDER_FAILED] = "Mappa megnyitása sikertelen ",
    [_L_RENAME_FAILED] = "Átnevezés Sikertelen\nHibakód",
    [_L_MAIN_RETURN] = "[VISSZA]",
    [_L_RANDOM_MODE_MANUAL] = "Randomizálás (Kézi)",
    [_L_RANDOM_MODE_AUTO] = "Randomizálás (Automat.)",
    [_L_SEQUENCE_MODE] = "Szekvenciális Mód",
    [_L_READ_WRITE_MODE] = "Olvasás-írás Mód",
    [_L_AMIIBOLINK_V1] = "V1",
    [_L_AMIIBOLINK_V2] = "V2",
    [_L_AMILOOP] = "AmiLoop",
    [_L_MODE] = "Mód",
    [_L_AUTO_RANDOM] = "Automat. Randomizálás",
    [_L_COMPATIBLE_MODE] = "Kompatibilis Mód",
    [_L_TAG_DETAILS] = "[Tag Részletek]",
    [_L_MAIN_MENU] = "[Főmenü]",
    [_L_MODE_RANDOM] = "Random (Kézi)",
    [_L_MODE_CYCLE] = "Szekvenciális",
    [_L_MODE_NTAG] = "Olvasás/Írás",
    [_L_MODE_RANDOM_AUTO_GEN] = "Random (Automat.)",
    [_L_BLANK_TAG] = "Üres NFC Címke",
    [_L_APP_AMIIDB] = "Amiibo Adatbázis",
    [_L_APP_AMMIDB_BROWSER] = "Böngésző...",
    [_L_APP_AMIIDB_SEARCH] = "Keresés...",
    [_L_APP_AMIIDB_MY_FAVORITES] = "Kedvencek...",
    [_L_APP_AMIIDB_MY_TAGS] = "Amiiboim...",
    [_L_APP_AMIIDB_SETTINGS] = "Beállítások...",
    [_L_APP_AMIIDB_EXIT] = "[Kilépés]",
    [_L_APP_AMIIDB_BACK] = "[Vissza]",
    [_L_APP_AMIIDB_SETTINGS_AMIIBO_KEY] = "Kulcsok",
    [_L_APP_AMIIDB_SETTINGS_AMIIBO_KEY_LOADED] = "Betöltve",
    [_L_APP_AMIIDB_SETTINGS_AMIIBO_KEY_NOT_LOADED] = "NINCS betöltve",
    [_L_APP_AMIIDB_SETTINGS_SLOT_NUM] = "Slot Száma",
    [_L_APP_AMIIDB_DETAIL_FAVORITE] = "Kedvenc...",
    [_L_APP_AMIIDB_DETAIL_SAVE_AS] = "Mentés Másként...",
    [_L_APP_AMIIDB_DETAIL_BACK_DETAIL] = "[Vissza a Részletekhez]",
    [_L_APP_AMIIDB_DETAIL_BACK_LIST] = "[Vissza a Listához]",
    [_L_APP_AMIIDB_SEARCH_HEAD] = "Keresés:",
    [_L_APP_AMIIDB_MORE] = "[Bővebben...]",
    [_L_APP_AMIIDB_MORE_MESSAGE] = "",
    [_L_APP_AMIIDB_EMPTY_TAG] = "<Üres Amiibo>",
    [_L_APP_AMIIDB_SLOT_DELETE] = "Újraindítás...",
    [_L_APP_AMIIDB_CONFIRM] = "Megerősítés",
    [_L_APP_AMIIDB_CANCEL] = "Törlés",
    [_L_APP_AMIIDB_TIPS] = "Megerősítés",
    [_L_APP_AMIIDB_NEW] = "Új...",
    [_L_APP_AMIIDB_EMPTY] = "Üres...",
    [_L_APP_AMIIDB_DELETE] = "Törlés...",
    [_L_APP_AMIIDB_FAV_NEW_HEAD] = "Új Kedvenc Mappa:",
    [_L_APP_AMIIDB_FAV_EMPTY_MSG] = "Üres Kedvenc Mappa?",
    [_L_APP_AMIIDB_FAV_DELETE_MSG] = "Törlés Megerősítése?",
    [_L_APP_AMIIDB_FAV_SELECT_FOLDER] = "Kedvenc Mappa Kiválasztása...",
    [_L_APP_AMIIDB_FAV_SUCCESS] = "Kedvenc Sikeres",
    [_L_APP_AMIIDB_FAV_FAILED] = "Kedvenc Sikertelen!",
    [_L_APP_AMIIDB_SLOT_SAVE_SUCCESS] = "Sikeresen Mentve",
    [_L_APP_AMIIDB_SLOT_SAVE_FAILED] = "Mentés Sikertelen!",
    [_L_APP_AMIIDB_SORT_FIELD] = "Rendezési mező",
    [_L_APP_AMIIDB_SORT_DEFAULT] = "Alapértelmezett",
    [_L_APP_AMIIDB_SORT_NAME] = "Név",
    [_L_APP_AMIIDB_NOT_SUPPORT_V3] = "",
    [_L_APP_CHAMELEON] = "Kártya Emulátor",
    [_L_APP_CHAMELEON_TAG_MF1_WRITE_NORMAL] = "Normál",
    [_L_APP_CHAMELEON_TAG_MF1_WRITE_DENIED] = "Tagadni",
    [_L_APP_CHAMELEON_TAG_MF1_WRITE_DECEIVE] = "Figyelmen Kívül Hagyni",
    [_L_APP_CHAMELEON_TAG_MF1_WRITE_SHADOW] = "Elrejt",
    [_L_APP_CHAMELEON_INITIALIZING] = "Az adatok inicializálása ...",
    [_L_APP_CHAMELEON_CARD_SLOT] = "Cella",
    [_L_APP_CHAMELEON_CARD_NICK] = "Becenév",
    [_L_APP_CHAMELEON_CARD_ID] = "ID",
    [_L_APP_CHAMELEON_CARD_TYPE] = "Típus",
    [_L_APP_CHAMELEON_CARD_DATA] = "Adatok...",
    [_L_APP_CHAMELEON_CARD_ADVANCED] = "Fejlett...",
    [_L_APP_CHAMELEON_CARD_SLOT_SETTINGS] = "Cella Beállításai...",
    [_L_APP_CHAMELEON_CARD_SLOT_NUM] = "Cella Száma...",
    [_L_APP_CHAMELEON_CARD_SET_NICK_SUCCESS] = "Becenév Beállítása Sikeres",
    [_L_APP_CHAMELEON_CARD_SET_NICK_FAILED] = "Becenév Beállítása Sikertelen!",
    [_L_APP_CHAMELEON_CARD_INPUT_NICK] = "Becenév Bevitele:",
    [_L_APP_CHAMELEON_CARD_DATA_LOAD] = "Betöltés...",
    [_L_APP_CHAMELEON_CARD_DATA_SAVE] = "Mentés...",
    [_L_APP_CHAMELEON_CARD_DATA_FACTORY] = "Visszaállítás...",
    [_L_APP_CHAMELEON_CARD_DATA_FACTORY_SUCCESS] = "Adatok Visszaállítása Sikeres",
    [_L_APP_CHAMELEON_CARD_DATA_LOAD_NOT_FOUND] = "Fájl Nem Található",
    [_L_APP_CHAMELEON_CARD_DATA_LOAD_SIZE_NOT_MATCH] = "Fájl Mérete Nem Egyezik",
    [_L_APP_CHAMELEON_CARD_DATA_LOAD_FAILED] = "Fájl betöltése Sikertelen",
    [_L_APP_CHAMELEON_CARD_DATA_LOAD_SUCCESS] = "Fájl Betöltése Sikeres",
    [_L_APP_CHAMELEON_CARD_DATA_SAVE_INPUT_FILE_NAME] = "Bemeneti Fájl Neve:",
    [_L_APP_CHAMELEON_CARD_DATA_SAVE_FAILED] = "Fájl Mentése Sikertelen!",
    [_L_APP_CHAMELEON_CARD_DATA_SAVE_SUCCESS] = "Fájl Mentése Sikeres",
    [_L_APP_CHAMELEON_CARD_ADV_CUSTOM_MODE] = "Egyéni Mód",
    [_L_APP_CHAMELEON_CARD_ADV_LOAD_BLOCK0] = "",
    [_L_APP_CHAMELEON_CARD_ADV_LOAD_BLOCK0_SUCCESS] = "",
    [_L_APP_CHAMELEON_CARD_ID_SIZE] = "",
    [_L_APP_CHAMELEON_CARD_GEN1A_MODE] = "Gen1A Engedélyezve",
    [_L_APP_CHAMELEON_CARD_GENERATE_UID] = "Véletlen UID",
    [_L_APP_CHAMELEON_CARD_GENERATE_UID_SUCCESS] = "Generált UID",
    [_L_APP_CHAMELEON_CARD_GEN2_MODE] = "Gen2 Engedélyezve",
    [_L_APP_CHAMELEON_CARD_WRITE_MODE] = "Írási Mód",
    [_L_APP_CHAMELEON_CARD_ADV_ID_EDIT_INVALID_INPUT] = "Érvénytelen bemenet!",
    [_L_APP_CHAMELEON_CARD_TYPE_FACTORY_DATA_CONFRIM] = "A kártya típusa megváltozott.\nGyári kártyaadatok?",
    [_L_APP_CHAMELEON_CARD_DEFAULT_CARD] = "",
    [_L_APP_GAME] = "",
    [_L_APP_GAME_TINY_ARKANOID] = "",
    [_L_APP_GAME_TINY_INVADERS] = "",
    [_L_APP_GAME_TINY_LANDER] = "",
    [_L_APP_GAME_TINY_TRIS] = "",
};
