solosky/pixl.js/fw/application/src/i18n/it_IT.c

#include "string_id.h"
const char * const lang_it_IT[_L_COUNT] = {
    [_L_ON] = "SI",
    [_L_OFF] = "NO",
    [_L_ON_F] = "[SI]",
    [_L_OFF_F] = "[NO]",
    [_L_BACK] = "Indietro",
    [_L_ERR] = "Errore",
    [_L_ERR_CODE] = "Codice errore",
    [_L_FAILED] = "",
    [_L_BYTES] = "",
    [_L_APP_AMIIBO] = "Emulatore Amiibo",
    [_L_APP_AMIIBOLINK] = "AmiiboLink",
    [_L_APP_BLE] = "Trasferimento file BLE",
    [_L_APP_BLE_TITLE] = "Trasferimento file BLE",
    [_L_APP_PLAYER] = "Lettore video",
    [_L_APP_SET] = "Impostazioni",
    [_L_APP_SET_VERSION] = "Versione",
    [_L_APP_SET_STORAGE_USED] = "Usato",
    [_L_APP_SET_STORAGE] = "Memoria esterna",
    [_L_APP_SET_OLED_CONTRAST] = "Contrasto",
    [_L_APP_SET_OLED_CONTRAST_TITLE] = "Contrasto",
    [_L_APP_SET_LCD_BACKLIGHT] = "Luminosità",
    [_L_APP_SET_LCD_BACKLIGHT_TITLE] = "Luminosità schermo",
    [_L_APP_SET_ANIM] = "Animazione menu",
    [_L_APP_SET_LIPO_BAT] = "Batteria LiPO",
    [_L_APP_SET_SHOW_MEM_USAGE] = "Memoria usata",
    [_L_APP_SET_HIBERNATE] = "Risveglio rapido",
    [_L_APP_SET_SLEEP_TIMEOUT] = "Timeout di sospensione",
    [_L_APP_SET_LANGUAGE] = "Lingua",
    [_L_APP_SET_GO_SLEEP] = "",
    [_L_APP_SET_DFU] = "Aggiornamento firmware",
    [_L_APP_SET_REBOOT] = "Riavvio del sistema",
    [_L_APP_SET_RESET_DEFAULT] = "Ripristina impostazioni predefinite",
    [_L_APP_SET_RESET_DEFAULT_SUCCESS] = "Ripristino riuscito!",
    [_L_APP_SET_RESET_DEFAULT_CONFIRM] = "Conferma il ripristino delle impostazioni?",
    [_L_APP_SET_ABOUT] = "",
    [_L_APP_SET_ABOUT_OPEN_SOURCE_PROJECT] = "",
    [_L_APP_SET_ABOUT_LGPL_LICENSE] = "",
    [_L_APP_SET_APP_MGMT] = "",
    [_L_15S] = "15 secondi",
    [_L_30S] = "30 secondi",
    [_L_45S] = "45 secondi",
    [_L_1MIN] = "1 minuto",
    [_L_2MIN] = "2 minuti",
    [_L_3MIN] = "3 minuti",
    [_L_AMIIBO_KEY_UNLOADED] = "Chiave Amiibo non caricata",
    [_L_UPLOAD_KEY_RETAIL_BIN] = "Carica il file key_retail.bin nella directory root della memoria.",
    [_L_KNOW] = "Ho Capito",
    [_L_RANDOM_GENERATION] = "Tag casuale",
    [_L_AUTO_RANDOM_GENERATION] = "Casuale automatico",
    [_L_SET_CUSTOM_ID] = "",
    [_L_INPUT_ID] = "",
    [_L_INAVLID_ID] = "",
    [_L_SHOW_QRCODE] = "Mostra codice QR",
    [_L_READ_ONLY] = "",
    [_L_DELETE_TAG] = "Elimina tag",
    [_L_DELETE_TAG_CONFIRM] = "Conferma eliminazione %s\n?",
    [_L_BACK_TO_DETAILS] = "[Torna ai dettagli del tag]",
    [_L_BACK_TO_FILE_LIST] = "[Torna alla lista dei file]",
    [_L_BACK_TO_MAIN_MENU] = "[Torna al menu principale]",
    [_L_FORMAT] = "Formatta...",
    [_L_FORMAT_STORAGE] = "Formatta memoria",
    [_L_DELETE_ALL_DATA] = "Questo cancellerà tutti i dati.\nConferma la formattazione?",
    [_L_DELETING_MESSAGE] = "Formattazione in corso ...",
    [_L_MESSAGE] = "Messaggio",
    [_L_CONFIRM] = "Conferma",
    [_L_CANCEL] = "Annulla",
    [_L_BACK_TO_LIST] = "[Torna alla lista]",
    [_L_NOT_MOUNTED] = "Non montato",
    [_L_MOUNTED_LFS] = "===Montato[LFS]===",
    [_L_MOUNTED_FFS] = "===Montato[FFS]===",
    [_L_TOTAL_SPACE] = "Totale",
    [_L_AVAILABLE_SPACE] = "Libero",
    [_L_NOT_AMIIBO_FILE] = "Questo non è un file\nAmiibo valido",
    [_L_READ_FILE_FAILED] = "Errore nella lettura del file",
    [_L_INPUT_FOLDER_NAME] = "Nome cartella:",
    [_L_INPUT_AMIIBO_NAME] = "Nome Amiibo:",
    [_L_DELETE_FILE] = "Eliminare %s ?",
    [_L_DELETE] = "Elimina...",
    [_L_TIPS] = "Conferma",
    [_L_INPUT_NEW_NAME] = "Nuovo nome:",
    [_L_INVALID_INPUT] = "Input non valido",
    [_L_CREATE_NEW_FOLDER] = "Crea cartella...",
    [_L_CREATE_NEW_TAG] = "Crea Amiibo...",
    [_L_CREATE_NEW_TAG_BATCH] = "Crea Amiibo in serie...",
    [_L_INPUT_TAG_NUM] = "Numero di tag：",
    [_L_CREATE_TOO_MANY_NUM] = "Numero max di %d tag in serie.",
    [_L_CREATING_TAG_BATCH] = "Creazione tag",
    [_L_CREATING_TAG_FAILED] = "Creazione tag %s fallita!",
    [_L_RENAME] = "Rinomina...",
    [_L_OPEN_FOLDER_FAILED] = "Errore nell'apertura della cartella",
    [_L_RENAME_FAILED] = "Errore nella rinomina\nCodice errore",
    [_L_MAIN_RETURN] = "[Torna indietro]",
    [_L_RANDOM_MODE_MANUAL] = "Casuale (Manuale)",
    [_L_RANDOM_MODE_AUTO] = "Casuale (Automatico)",
    [_L_SEQUENCE_MODE] = "Modo sequenziale",
    [_L_READ_WRITE_MODE] = "Modo lettura/scrittura",
    [_L_AMIIBOLINK_V1] = "V1",
    [_L_AMIIBOLINK_V2] = "V2",
    [_L_AMILOOP] = "AmiLoop",
    [_L_MODE] = "Modalità",
    [_L_AUTO_RANDOM] = "Auto. casuale",
    [_L_COMPATIBLE_MODE] = "Mod. Compatibilità",
    [_L_TAG_DETAILS] = "[Torna ai dettagli]",
    [_L_MAIN_MENU] = "[Menu principale]",
    [_L_MODE_RANDOM] = "Casuale man.",
    [_L_MODE_CYCLE] = "Sequenziale",
    [_L_MODE_NTAG] = "Lett./Scritt.",
    [_L_MODE_RANDOM_AUTO_GEN] = "Auto. casuale",
    [_L_BLANK_TAG] = "Amiibo non assegnato",
    [_L_APP_AMIIDB] = "Database Amiibo",
    [_L_APP_AMMIDB_BROWSER] = "Esplora...",
    [_L_APP_AMIIDB_SEARCH] = "Cerca...",
    [_L_APP_AMIIDB_MY_FAVORITES] = "I miei preferiti...",
    [_L_APP_AMIIDB_MY_TAGS] = "I miei Amiibo...",
    [_L_APP_AMIIDB_SETTINGS] = "Impostazioni...",
    [_L_APP_AMIIDB_EXIT] = "[Menu principale]",
    [_L_APP_AMIIDB_BACK] = "[Torna indietro]",
    [_L_APP_AMIIDB_SETTINGS_AMIIBO_KEY] = "Chiavi",
    [_L_APP_AMIIDB_SETTINGS_AMIIBO_KEY_LOADED] = "Caricate",
    [_L_APP_AMIIDB_SETTINGS_AMIIBO_KEY_NOT_LOADED] = "NON caricate",
    [_L_APP_AMIIDB_SETTINGS_SLOT_NUM] = "Num. slot",
    [_L_APP_AMIIDB_DETAIL_FAVORITE] = "Preferito...",
    [_L_APP_AMIIDB_DETAIL_SAVE_AS] = "Assegna a...",
    [_L_APP_AMIIDB_DETAIL_BACK_DETAIL] = "[Torna ai dettagli]",
    [_L_APP_AMIIDB_DETAIL_BACK_LIST] = "[Torna alla lista]",
    [_L_APP_AMIIDB_SEARCH_HEAD] = "Cerca:",
    [_L_APP_AMIIDB_MORE] = "[Più...]",
    [_L_APP_AMIIDB_MORE_MESSAGE] = "",
    [_L_APP_AMIIDB_EMPTY_TAG] = "<Non assegnato>",
    [_L_APP_AMIIDB_SLOT_DELETE] = "Elimina...",
    [_L_APP_AMIIDB_CONFIRM] = "Conferma",
    [_L_APP_AMIIDB_CANCEL] = "Annulla",
    [_L_APP_AMIIDB_TIPS] = "Conferma",
    [_L_APP_AMIIDB_NEW] = "Nuovo...",
    [_L_APP_AMIIDB_EMPTY] = "Svuota...",
    [_L_APP_AMIIDB_DELETE] = "Cancella...",
    [_L_APP_AMIIDB_FAV_NEW_HEAD] = "Nuova cart. preferiti:",
    [_L_APP_AMIIDB_FAV_EMPTY_MSG] = "Svuotare cart. preferiti?",
    [_L_APP_AMIIDB_FAV_DELETE_MSG] = "Conferma cancellazione?",
    [_L_APP_AMIIDB_FAV_SELECT_FOLDER] = "Selez. cart. preferiti...",
    [_L_APP_AMIIDB_FAV_SUCCESS] = "Preferito aggiunto!",
    [_L_APP_AMIIDB_FAV_FAILED] = "Preferito non aggiunto!",
    [_L_APP_AMIIDB_SLOT_SAVE_SUCCESS] = "Assegnazione corretta",
    [_L_APP_AMIIDB_SLOT_SAVE_FAILED] = "Assegnazione fallita!",
    [_L_APP_AMIIDB_SORT_FIELD] = "Campo di ordinamento",
    [_L_APP_AMIIDB_SORT_DEFAULT] = "Predefinito",
    [_L_APP_AMIIDB_SORT_NAME] = "Nome",
    [_L_APP_AMIIDB_NOT_SUPPORT_V3] = "",
    [_L_APP_CHAMELEON] = "Emula tag RFID",
    [_L_APP_CHAMELEON_TAG_MF1_WRITE_NORMAL] = "Normale",
    [_L_APP_CHAMELEON_TAG_MF1_WRITE_DENIED] = "Nega",
    [_L_APP_CHAMELEON_TAG_MF1_WRITE_DECEIVE] = "Ignora",
    [_L_APP_CHAMELEON_TAG_MF1_WRITE_SHADOW] = "Cache",
    [_L_APP_CHAMELEON_INITIALIZING] = "Inizializzazione ambiente.\nPer favore attendi...",
    [_L_APP_CHAMELEON_CARD_SLOT] = "Slot",
    [_L_APP_CHAMELEON_CARD_NICK] = "Nickname",
    [_L_APP_CHAMELEON_CARD_ID] = "ID",
    [_L_APP_CHAMELEON_CARD_TYPE] = "Tipo",
    [_L_APP_CHAMELEON_CARD_DATA] = "Dati...",
    [_L_APP_CHAMELEON_CARD_ADVANCED] = "Avanzato...",
    [_L_APP_CHAMELEON_CARD_SLOT_SETTINGS] = "Impostazioni...",
    [_L_APP_CHAMELEON_CARD_SLOT_NUM] = "Num. slot...",
    [_L_APP_CHAMELEON_CARD_SET_NICK_SUCCESS] = "Cambio nickname riuscito.",
    [_L_APP_CHAMELEON_CARD_SET_NICK_FAILED] = "Cambio nickname fallito!",
    [_L_APP_CHAMELEON_CARD_INPUT_NICK] = "Nickname:",
    [_L_APP_CHAMELEON_CARD_DATA_LOAD] = "Carica...",
    [_L_APP_CHAMELEON_CARD_DATA_SAVE] = "Salva...",
    [_L_APP_CHAMELEON_CARD_DATA_FACTORY] = "Inizializza...",
    [_L_APP_CHAMELEON_CARD_DATA_FACTORY_SUCCESS] = "Dati inizializzati!",
    [_L_APP_CHAMELEON_CARD_DATA_LOAD_NOT_FOUND] = "File non trovato",
    [_L_APP_CHAMELEON_CARD_DATA_LOAD_SIZE_NOT_MATCH] = "Dimensione file non corretta",
    [_L_APP_CHAMELEON_CARD_DATA_LOAD_FAILED] = "Caricamento file fallito",
    [_L_APP_CHAMELEON_CARD_DATA_LOAD_SUCCESS] = "Caricamento file riuscito",
    [_L_APP_CHAMELEON_CARD_DATA_SAVE_INPUT_FILE_NAME] = "Nome file:",
    [_L_APP_CHAMELEON_CARD_DATA_SAVE_FAILED] = "Errore nel salvataggio!",
    [_L_APP_CHAMELEON_CARD_DATA_SAVE_SUCCESS] = "Salvataggio riuscito",
    [_L_APP_CHAMELEON_CARD_ADV_CUSTOM_MODE] = "Modalità personalizzata",
    [_L_APP_CHAMELEON_CARD_ADV_LOAD_BLOCK0] = "",
    [_L_APP_CHAMELEON_CARD_ADV_LOAD_BLOCK0_SUCCESS] = "",
    [_L_APP_CHAMELEON_CARD_ID_SIZE] = "",
    [_L_APP_CHAMELEON_CARD_GEN1A_MODE] = "Gen1A abilitata",
    [_L_APP_CHAMELEON_CARD_GENERATE_UID] = "Genera nuovo UID",
    [_L_APP_CHAMELEON_CARD_GENERATE_UID_SUCCESS] = "UID generato",
    [_L_APP_CHAMELEON_CARD_GEN2_MODE] = "Gen2 abilitata",
    [_L_APP_CHAMELEON_CARD_WRITE_MODE] = "Modalità scrittura",
    [_L_APP_CHAMELEON_CARD_ADV_ID_EDIT_INVALID_INPUT] = "Input non valido!",
    [_L_APP_CHAMELEON_CARD_TYPE_FACTORY_DATA_CONFRIM] = "Tipo di carta modificato\nInizializzare carta?",
    [_L_APP_CHAMELEON_CARD_DEFAULT_CARD] = "",
    [_L_APP_GAME] = "",
    [_L_APP_GAME_TINY_ARKANOID] = "",
    [_L_APP_GAME_TINY_INVADERS] = "",
    [_L_APP_GAME_TINY_LANDER] = "",
    [_L_APP_GAME_TINY_TRIS] = "",
};
