solosky/pixl.js/fw/application/src/i18n/nl_NL.c

#include "string_id.h"
const char * const lang_nl_NL[_L_COUNT] = {
    [_L_ON] = "AAN",
    [_L_OFF] = "UIT",
    [_L_ON_F] = "[AAN]",
    [_L_OFF_F] = "[UIT]",
    [_L_BACK] = "Terug",
    [_L_ERR] = "Fout",
    [_L_ERR_CODE] = "Foutcode",
    [_L_FAILED] = "",
    [_L_BYTES] = "",
    [_L_APP_AMIIBO] = "Amiibo-Emulator",
    [_L_APP_AMIIBOLINK] = "AmiiboLink",
    [_L_APP_BLE] = "BLE Bestandsoverdracht",
    [_L_APP_BLE_TITLE] = "BLE Bestandsoverdracht",
    [_L_APP_PLAYER] = "Videospeler",
    [_L_APP_SET] = "Instellingen",
    [_L_APP_SET_VERSION] = "Versie",
    [_L_APP_SET_STORAGE_USED] = "Gebruikt",
    [_L_APP_SET_STORAGE] = "Externe Opslag",
    [_L_APP_SET_OLED_CONTRAST] = "Contrast",
    [_L_APP_SET_OLED_CONTRAST_TITLE] = "Contrast",
    [_L_APP_SET_LCD_BACKLIGHT] = "Achtergrondverlichting",
    [_L_APP_SET_LCD_BACKLIGHT_TITLE] = "Helderheid Achtergrondverlichting",
    [_L_APP_SET_ANIM] = "Menu-Animatie",
    [_L_APP_SET_LIPO_BAT] = "LiPO-Batterij",
    [_L_APP_SET_SHOW_MEM_USAGE] = "Gebruikt Geheugen",
    [_L_APP_SET_HIBERNATE] = "Snel Ontwaken",
    [_L_APP_SET_SLEEP_TIMEOUT] = "Time-out Slaapstand",
    [_L_APP_SET_LANGUAGE] = "Taal",
    [_L_APP_SET_GO_SLEEP] = "",
    [_L_APP_SET_DFU] = "Firmware Bijwerken",
    [_L_APP_SET_REBOOT] = "Systeem Herstarten",
    [_L_APP_SET_RESET_DEFAULT] = "Terugzetten Naar Standaardwaarden",
    [_L_APP_SET_RESET_DEFAULT_SUCCESS] = "Standaardinstellingen Herstellen",
    [_L_APP_SET_RESET_DEFAULT_CONFIRM] = "",
    [_L_APP_SET_ABOUT] = "",
    [_L_APP_SET_ABOUT_OPEN_SOURCE_PROJECT] = "",
    [_L_APP_SET_ABOUT_LGPL_LICENSE] = "",
    [_L_APP_SET_APP_MGMT] = "",
    [_L_15S] = "15 sec.",
    [_L_30S] = "30 sec.",
    [_L_45S] = "45 sec.",
    [_L_1MIN] = "1 min.",
    [_L_2MIN] = "2 min.",
    [_L_3MIN] = "3 min.",
    [_L_AMIIBO_KEY_UNLOADED] = "Amiibo-Sleutel Niet Geladen",
    [_L_UPLOAD_KEY_RETAIL_BIN] = "Upload het bestand key_retail.bin naar de hoofdmap van de opslag.",
    [_L_KNOW] = "Begrepen",
    [_L_RANDOM_GENERATION] = "Willekeurige Tag",
    [_L_AUTO_RANDOM_GENERATION] = "Automatische Randomisatie",
    [_L_SET_CUSTOM_ID] = "",
    [_L_INPUT_ID] = "",
    [_L_INAVLID_ID] = "",
    [_L_SHOW_QRCODE] = "QR-Code Weergeven",
    [_L_READ_ONLY] = "",
    [_L_DELETE_TAG] = "Tag Verwijderen",
    [_L_DELETE_TAG_CONFIRM] = "Bevestig Verwijderen %s ?",
    [_L_BACK_TO_DETAILS] = "Terug naar Tag Details",
    [_L_BACK_TO_FILE_LIST] = "Terug naar Bestandslijst",
    [_L_BACK_TO_MAIN_MENU] = "Terug naar Hoofdmenu",
    [_L_FORMAT] = "Formatteren",
    [_L_FORMAT_STORAGE] = "Opslag Formatteren",
    [_L_DELETE_ALL_DATA] = "Hierdoor worden alle gegevens gewist. Formatteren bevestigen?",
    [_L_DELETING_MESSAGE] = "Formatteren ...",
    [_L_MESSAGE] = "Bericht",
    [_L_CONFIRM] = "Bevestigen",
    [_L_CANCEL] = "Annuleren",
    [_L_BACK_TO_LIST] = "Terug naar Lijst",
    [_L_NOT_MOUNTED] = "Niet Gekoppeld",
    [_L_MOUNTED_LFS] = "===Gekoppeld[LFS]===",
    [_L_MOUNTED_FFS] = "===Gekoppeld[FFS]===",
    [_L_TOTAL_SPACE] = "Totaal",
    [_L_AVAILABLE_SPACE] = "Vrij",
    [_L_NOT_AMIIBO_FILE] = "Dit is geen Amiibo-bestand",
    [_L_READ_FILE_FAILED] = "Lezen van het bestand is mislukt",
    [_L_INPUT_FOLDER_NAME] = "Naam Invoermap:",
    [_L_INPUT_AMIIBO_NAME] = "Naam Amiibo Invoeren:",
    [_L_DELETE_FILE] = "%s verwijderen ?",
    [_L_DELETE] = "Verwijder...",
    [_L_TIPS] = "Bevestigen",
    [_L_INPUT_NEW_NAME] = "Nieuwe Naam Invoeren:",
    [_L_INVALID_INPUT] = "Ongeldige Invoer",
    [_L_CREATE_NEW_FOLDER] = "Nieuwe Map Maken...",
    [_L_CREATE_NEW_TAG] = "Nieuwe Tag Aanmaken...",
    [_L_CREATE_NEW_TAG_BATCH] = "Nieuwe Tags in een Batch Aanmaken...",
    [_L_INPUT_TAG_NUM] = "Labelnummer Invoeren:",
    [_L_CREATE_TOO_MANY_NUM] = "Maximum %d tags aangemaakt in een batch.",
    [_L_CREATING_TAG_BATCH] = "Tag aanmaken",
    [_L_CREATING_TAG_FAILED] = "Aanmaken tag %s mislukt!",
    [_L_RENAME] = "Hernoem...",
    [_L_OPEN_FOLDER_FAILED] = "Kan map niet openen",
    [_L_RENAME_FAILED] = "Hernoemen mislukt.\nFoutcode",
    [_L_MAIN_RETURN] = "[TERUG]",
    [_L_RANDOM_MODE_MANUAL] = "Willekeurig (Handmatig)",
    [_L_RANDOM_MODE_AUTO] = "Willekeurig (Automatisch)",
    [_L_SEQUENCE_MODE] = "Sequentiële Modus",
    [_L_READ_WRITE_MODE] = "Lees-Schrijfmodus",
    [_L_AMIIBOLINK_V1] = "V1",
    [_L_AMIIBOLINK_V2] = "V2",
    [_L_AMILOOP] = "AmiLoop",
    [_L_MODE] = "Modus",
    [_L_AUTO_RANDOM] = "Automatische Randomisatie",
    [_L_COMPATIBLE_MODE] = "Compatibiliteitsmodus",
    [_L_TAG_DETAILS] = "[Tag Details]",
    [_L_MAIN_MENU] = "[Hoofdmenu]",
    [_L_MODE_RANDOM] = "Willekeurig (Handmatig)",
    [_L_MODE_CYCLE] = "Sequentieel",
    [_L_MODE_NTAG] = "Lezen/Schrijven",
    [_L_MODE_RANDOM_AUTO_GEN] = "Willekeurig (Automatisch)",
    [_L_BLANK_TAG] = "Lege NFC-tag",
    [_L_APP_AMIIDB] = "Amiibo-Database",
    [_L_APP_AMMIDB_BROWSER] = "Browser...",
    [_L_APP_AMIIDB_SEARCH] = "Zoeken...",
    [_L_APP_AMIIDB_MY_FAVORITES] = "Mijn Favorieten...",
    [_L_APP_AMIIDB_MY_TAGS] = "Mijn Amiibo...",
    [_L_APP_AMIIDB_SETTINGS] = "Instellingen...",
    [_L_APP_AMIIDB_EXIT] = "[Afsluiten]",
    [_L_APP_AMIIDB_BACK] = "[Terug]",
    [_L_APP_AMIIDB_SETTINGS_AMIIBO_KEY] = "Toetsen",
    [_L_APP_AMIIDB_SETTINGS_AMIIBO_KEY_LOADED] = "Geladen",
    [_L_APP_AMIIDB_SETTINGS_AMIIBO_KEY_NOT_LOADED] = "NIET Geladen",
    [_L_APP_AMIIDB_SETTINGS_SLOT_NUM] = "Slotnummer",
    [_L_APP_AMIIDB_DETAIL_FAVORITE] = "Favoriet...",
    [_L_APP_AMIIDB_DETAIL_SAVE_AS] = "Opslaan Als...",
    [_L_APP_AMIIDB_DETAIL_BACK_DETAIL] = "[Terug naar Detail]",
    [_L_APP_AMIIDB_DETAIL_BACK_LIST] = "[Terug naar Lijst].",
    [_L_APP_AMIIDB_SEARCH_HEAD] = "Zoeken:",
    [_L_APP_AMIIDB_MORE] = "[Meer...]",
    [_L_APP_AMIIDB_MORE_MESSAGE] = "",
    [_L_APP_AMIIDB_EMPTY_TAG] = "<Blanke Amiibo>",
    [_L_APP_AMIIDB_SLOT_DELETE] = "Reset...",
    [_L_APP_AMIIDB_CONFIRM] = "Bevestigen",
    [_L_APP_AMIIDB_CANCEL] = "Annuleren",
    [_L_APP_AMIIDB_TIPS] = "Bevestigen",
    [_L_APP_AMIIDB_NEW] = "Nieuw...",
    [_L_APP_AMIIDB_EMPTY] = "Leeg...",
    [_L_APP_AMIIDB_DELETE] = "Verwijderen...",
    [_L_APP_AMIIDB_FAV_NEW_HEAD] = "Nieuwe Favoriete Map:",
    [_L_APP_AMIIDB_FAV_EMPTY_MSG] = "Favoriete Map Leegmaken?",
    [_L_APP_AMIIDB_FAV_DELETE_MSG] = "Verwijderen Bevestigen?",
    [_L_APP_AMIIDB_FAV_SELECT_FOLDER] = "Selecteer Favoriete Map...",
    [_L_APP_AMIIDB_FAV_SUCCESS] = "Favoriet Geslaagd",
    [_L_APP_AMIIDB_FAV_FAILED] = "Favoriet Mislukt!",
    [_L_APP_AMIIDB_SLOT_SAVE_SUCCESS] = "Opslaan Succes",
    [_L_APP_AMIIDB_SLOT_SAVE_FAILED] = "Opslaan Mislukt!",
    [_L_APP_AMIIDB_SORT_FIELD] = "Sorteerveld",
    [_L_APP_AMIIDB_SORT_DEFAULT] = "Standaard",
    [_L_APP_AMIIDB_SORT_NAME] = "Naam",
    [_L_APP_AMIIDB_NOT_SUPPORT_V3] = "",
    [_L_APP_CHAMELEON] = "Kaart Emulator",
    [_L_APP_CHAMELEON_TAG_MF1_WRITE_NORMAL] = "Normaal",
    [_L_APP_CHAMELEON_TAG_MF1_WRITE_DENIED] = "Weigeren",
    [_L_APP_CHAMELEON_TAG_MF1_WRITE_DECEIVE] = "Negeren",
    [_L_APP_CHAMELEON_TAG_MF1_WRITE_SHADOW] = "Cache",
    [_L_APP_CHAMELEON_INITIALIZING] = "Gegevens Initialiseren ...",
    [_L_APP_CHAMELEON_CARD_SLOT] = "Slot",
    [_L_APP_CHAMELEON_CARD_NICK] = "Bijnaam",
    [_L_APP_CHAMELEON_CARD_ID] = "ID",
    [_L_APP_CHAMELEON_CARD_TYPE] = "Type",
    [_L_APP_CHAMELEON_CARD_DATA] = "Gegevens...",
    [_L_APP_CHAMELEON_CARD_ADVANCED] = "Geavanceerd...",
    [_L_APP_CHAMELEON_CARD_SLOT_SETTINGS] = "Slot Instellingen...",
    [_L_APP_CHAMELEON_CARD_SLOT_NUM] = "Slotnummer...",
    [_L_APP_CHAMELEON_CARD_SET_NICK_SUCCESS] = "Bijnaam Instellen Succes",
    [_L_APP_CHAMELEON_CARD_SET_NICK_FAILED] = "Bijnaam Instellen Mislukt!",
    [_L_APP_CHAMELEON_CARD_INPUT_NICK] = "Voer Bijnaam In:",
    [_L_APP_CHAMELEON_CARD_DATA_LOAD] = "Laden...",
    [_L_APP_CHAMELEON_CARD_DATA_SAVE] = "Opslaan...",
    [_L_APP_CHAMELEON_CARD_DATA_FACTORY] = "Terugzetten Naar Standaard...",
    [_L_APP_CHAMELEON_CARD_DATA_FACTORY_SUCCESS] = "Fabriekgegeven terugzetten Succesvol",
    [_L_APP_CHAMELEON_CARD_DATA_LOAD_NOT_FOUND] = "Bestand Niet Gevonden",
    [_L_APP_CHAMELEON_CARD_DATA_LOAD_SIZE_NOT_MATCH] = "Bestandsgrootte Komt Niet Overeen",
    [_L_APP_CHAMELEON_CARD_DATA_LOAD_FAILED] = "Bestand Laden Mislukt",
    [_L_APP_CHAMELEON_CARD_DATA_LOAD_SUCCESS] = "Laad Bestand Succesvol",
    [_L_APP_CHAMELEON_CARD_DATA_SAVE_INPUT_FILE_NAME] = "Bestandsnaam Invoeren:",
    [_L_APP_CHAMELEON_CARD_DATA_SAVE_FAILED] = "Bestand Opslaan Mislukt!",
    [_L_APP_CHAMELEON_CARD_DATA_SAVE_SUCCESS] = "Bestand Opslaan Gelukt",
    [_L_APP_CHAMELEON_CARD_ADV_CUSTOM_MODE] = "Aangepaste Modus",
    [_L_APP_CHAMELEON_CARD_ADV_LOAD_BLOCK0] = "",
    [_L_APP_CHAMELEON_CARD_ADV_LOAD_BLOCK0_SUCCESS] = "",
    [_L_APP_CHAMELEON_CARD_ID_SIZE] = "",
    [_L_APP_CHAMELEON_CARD_GEN1A_MODE] = "Gen1A Ingeschakeld",
    [_L_APP_CHAMELEON_CARD_GENERATE_UID] = "Willekeurige UID",
    [_L_APP_CHAMELEON_CARD_GENERATE_UID_SUCCESS] = "UID Gegenereerd",
    [_L_APP_CHAMELEON_CARD_GEN2_MODE] = "Gen2 Ingeschakeld",
    [_L_APP_CHAMELEON_CARD_WRITE_MODE] = "Schrijfmodus",
    [_L_APP_CHAMELEON_CARD_ADV_ID_EDIT_INVALID_INPUT] = "Ongeldige Invoer!",
    [_L_APP_CHAMELEON_CARD_TYPE_FACTORY_DATA_CONFRIM] = "Kaarttype gewijzigd. \nGegevens terugzetten naar standaard?",
    [_L_APP_CHAMELEON_CARD_DEFAULT_CARD] = "",
    [_L_APP_GAME] = "",
    [_L_APP_GAME_TINY_ARKANOID] = "",
    [_L_APP_GAME_TINY_INVADERS] = "",
    [_L_APP_GAME_TINY_LANDER] = "",
    [_L_APP_GAME_TINY_TRIS] = "",
};
