solosky/pixl.js/fw/application/src/i18n/pl_PL.c

#include "string_id.h"
const char * const lang_pl_PL[_L_COUNT] = {
    [_L_ON] = "WŁ",
    [_L_OFF] = "WYŁ",
    [_L_ON_F] = "[WŁ]",
    [_L_OFF_F] = "[WYŁ]",
    [_L_BACK] = "Wróć",
    [_L_ERR] = "Błąd",
    [_L_ERR_CODE] = "Kod Błędu",
    [_L_FAILED] = "Niepowodzenie",
    [_L_BYTES] = "",
    [_L_APP_AMIIBO] = "Emulator Amiibo",
    [_L_APP_AMIIBOLINK] = "AmiiboLink",
    [_L_APP_BLE] = "Transfer Plików BLE",
    [_L_APP_BLE_TITLE] = "Transfer Plików",
    [_L_APP_PLAYER] = "Odtwarzacz Video",
    [_L_APP_SET] = "Ustawienia",
    [_L_APP_SET_VERSION] = "Wersja",
    [_L_APP_SET_STORAGE_USED] = "Używane",
    [_L_APP_SET_STORAGE] = "Pamięć Zewnętrzna",
    [_L_APP_SET_OLED_CONTRAST] = "Kontrast OLED",
    [_L_APP_SET_OLED_CONTRAST_TITLE] = "Kontrast",
    [_L_APP_SET_LCD_BACKLIGHT] = "Podświetlenie",
    [_L_APP_SET_LCD_BACKLIGHT_TITLE] = "Jasność Podświetlenia",
    [_L_APP_SET_ANIM] = "Animowane Menu",
    [_L_APP_SET_LIPO_BAT] = "Bateria LiPO",
    [_L_APP_SET_SHOW_MEM_USAGE] = "Wskaźnik Pamięci",
    [_L_APP_SET_HIBERNATE] = "Szybkie Wybudzanie",
    [_L_APP_SET_SLEEP_TIMEOUT] = "Opóźnienie Uśpienia",
    [_L_APP_SET_LANGUAGE] = "Język",
    [_L_APP_SET_GO_SLEEP] = "Uśpij Teraz",
    [_L_APP_SET_DFU] = "Aktualizacja Oprogramowania",
    [_L_APP_SET_REBOOT] = "Restart Systemu",
    [_L_APP_SET_RESET_DEFAULT] = "Przywróć Domyślne Ustawienia",
    [_L_APP_SET_RESET_DEFAULT_SUCCESS] = "Resetowanie Zakończone!",
    [_L_APP_SET_RESET_DEFAULT_CONFIRM] = "Zresetować Ustawienia?",
    [_L_APP_SET_ABOUT] = "O Urządzeniu",
    [_L_APP_SET_ABOUT_OPEN_SOURCE_PROJECT] = "Projekt Open Source",
    [_L_APP_SET_ABOUT_LGPL_LICENSE] = "Licencja GPL 2.0",
    [_L_APP_SET_APP_MGMT] = "",
    [_L_15S] = "15 Sekund",
    [_L_30S] = "30 Sekund",
    [_L_45S] = "45 Sekund",
    [_L_1MIN] = "1 Minuta",
    [_L_2MIN] = "2 Minuty",
    [_L_3MIN] = "3 Minuty",
    [_L_AMIIBO_KEY_UNLOADED] = "Klucz Amiibo nie został załadowany",
    [_L_UPLOAD_KEY_RETAIL_BIN] = "Prześlij plik key_retail.bin\ndo głównego katalogu pamięci.",
    [_L_KNOW] = "Rozumiem",
    [_L_RANDOM_GENERATION] = "Losuj Tag",
    [_L_AUTO_RANDOM_GENERATION] = "Autom. Losowanie",
    [_L_SET_CUSTOM_ID] = "Niestandardowy ID",
    [_L_INPUT_ID] = "Wprowadź ID",
    [_L_INAVLID_ID] = "Niewłaściwy ID",
    [_L_SHOW_QRCODE] = "Wyświetl Kod QR",
    [_L_READ_ONLY] = "Tylko do odczytu",
    [_L_DELETE_TAG] = "Usuń Tag",
    [_L_DELETE_TAG_CONFIRM] = "Usunąć %s ?",
    [_L_BACK_TO_DETAILS] = "[Wróć do Szczegółów]",
    [_L_BACK_TO_FILE_LIST] = "[Wróć do Listy Plików]",
    [_L_BACK_TO_MAIN_MENU] = "[Wróć do Głównego Menu]",
    [_L_FORMAT] = "Formatuj...",
    [_L_FORMAT_STORAGE] = "Formatuj Pamięć",
    [_L_DELETE_ALL_DATA] = "Usunąć wszystkie dane?",
    [_L_DELETING_MESSAGE] = "Formatowanie ...",
    [_L_MESSAGE] = "Wiadomość",
    [_L_CONFIRM] = "Potwierdź",
    [_L_CANCEL] = "Anuluj",
    [_L_BACK_TO_LIST] = "[Wróć do Listy]",
    [_L_NOT_MOUNTED] = "Niezamontowany",
    [_L_MOUNTED_LFS] = "===Zamontowany[LFS]===",
    [_L_MOUNTED_FFS] = "===Zamontowany[FFS]===",
    [_L_TOTAL_SPACE] = "Pojemność",
    [_L_AVAILABLE_SPACE] = "Wolne",
    [_L_NOT_AMIIBO_FILE] = "To nie jest plik Amiibo",
    [_L_READ_FILE_FAILED] = "Błąd odczytu pliku",
    [_L_INPUT_FOLDER_NAME] = "Wprowadź nazwę folderu:",
    [_L_INPUT_AMIIBO_NAME] = "Wprowadź nazwę Amiibo:",
    [_L_DELETE_FILE] = "Usunąć %s ?",
    [_L_DELETE] = "Usuń...",
    [_L_TIPS] = "Potwierdź",
    [_L_INPUT_NEW_NAME] = "Wprowadź nową nazwę:",
    [_L_INVALID_INPUT] = "Wprowadzone dane są błędne",
    [_L_CREATE_NEW_FOLDER] = "Utwórz Nowy Folder...",
    [_L_CREATE_NEW_TAG] = "Utwórz Nowy Tag...",
    [_L_CREATE_NEW_TAG_BATCH] = "Utwórz Grupę Nowych Tagów...",
    [_L_INPUT_TAG_NUM] = "Wprowadź numer tagu:",
    [_L_CREATE_TOO_MANY_NUM] = "Limit tagów wynosi %d.",
    [_L_CREATING_TAG_BATCH] = "Tworzenie Tagu",
    [_L_CREATING_TAG_FAILED] = "Tworzenie tagu %s nie udało się!",
    [_L_RENAME] = "Zmień Nazwę...",
    [_L_OPEN_FOLDER_FAILED] = "Nie udało się otworzyć folderu",
    [_L_RENAME_FAILED] = "Nie udało się zmienić nazwy\nKod błędu",
    [_L_MAIN_RETURN] = "[POWRÓT]",
    [_L_RANDOM_MODE_MANUAL] = "Losuj (Ręcznie)",
    [_L_RANDOM_MODE_AUTO] = "Losuj (Autom.)",
    [_L_SEQUENCE_MODE] = "Tryb Sekwencyjny",
    [_L_READ_WRITE_MODE] = "Tryb odczyt-zapis",
    [_L_AMIIBOLINK_V1] = "V1",
    [_L_AMIIBOLINK_V2] = "V2",
    [_L_AMILOOP] = "AmiLoop",
    [_L_MODE] = "Tryb",
    [_L_AUTO_RANDOM] = "Autom. Randomizacja",
    [_L_COMPATIBLE_MODE] = "Tryb Zgodności",
    [_L_TAG_DETAILS] = "[Szczegóły Tagu]",
    [_L_MAIN_MENU] = "[Główne Menu]",
    [_L_MODE_RANDOM] = "Losowanie (Ręcznie)",
    [_L_MODE_CYCLE] = "Ciągły",
    [_L_MODE_NTAG] = "Odczyt/Zapis",
    [_L_MODE_RANDOM_AUTO_GEN] = "Losowanie (Autom.)",
    [_L_BLANK_TAG] = "Pusty Tag NFC",
    [_L_APP_AMIIDB] = "Baza Danych Amiibo",
    [_L_APP_AMMIDB_BROWSER] = "Przeglądaj...",
    [_L_APP_AMIIDB_SEARCH] = "Szukaj...",
    [_L_APP_AMIIDB_MY_FAVORITES] = "Ulubione...",
    [_L_APP_AMIIDB_MY_TAGS] = "Moje Amiibo...",
    [_L_APP_AMIIDB_SETTINGS] = "Ustawienia...",
    [_L_APP_AMIIDB_EXIT] = "[Wyjście]",
    [_L_APP_AMIIDB_BACK] = "[Wróć]",
    [_L_APP_AMIIDB_SETTINGS_AMIIBO_KEY] = "Klucze",
    [_L_APP_AMIIDB_SETTINGS_AMIIBO_KEY_LOADED] = "Załadowane",
    [_L_APP_AMIIDB_SETTINGS_AMIIBO_KEY_NOT_LOADED] = "NIE Załadowane",
    [_L_APP_AMIIDB_SETTINGS_SLOT_NUM] = "Ilość Slotów",
    [_L_APP_AMIIDB_DETAIL_FAVORITE] = "Ulubione...",
    [_L_APP_AMIIDB_DETAIL_SAVE_AS] = "Zapisz Jako...",
    [_L_APP_AMIIDB_DETAIL_BACK_DETAIL] = "[Wróć do Szczegółów]",
    [_L_APP_AMIIDB_DETAIL_BACK_LIST] = "[Wróć do Listy]",
    [_L_APP_AMIIDB_SEARCH_HEAD] = "Szukaj:",
    [_L_APP_AMIIDB_MORE] = "[Więcej...]",
    [_L_APP_AMIIDB_MORE_MESSAGE] = "Zbyt dużo wyników.\nSprecyzuj Wyszukiwanie.",
    [_L_APP_AMIIDB_EMPTY_TAG] = "<Puste Amiibo>",
    [_L_APP_AMIIDB_SLOT_DELETE] = "Zresetuj...",
    [_L_APP_AMIIDB_CONFIRM] = "Potwierdź",
    [_L_APP_AMIIDB_CANCEL] = "Anuluj",
    [_L_APP_AMIIDB_TIPS] = "Potwierdź",
    [_L_APP_AMIIDB_NEW] = "Nowe...",
    [_L_APP_AMIIDB_EMPTY] = "Opróżnij...",
    [_L_APP_AMIIDB_DELETE] = "Usuń...",
    [_L_APP_AMIIDB_FAV_NEW_HEAD] = "Wprowadź nazwę folderu:",
    [_L_APP_AMIIDB_FAV_EMPTY_MSG] = "Usunąć całą zawartość\ntego katalogu?",
    [_L_APP_AMIIDB_FAV_DELETE_MSG] = "Na pewno chcesz\nusunąć?",
    [_L_APP_AMIIDB_FAV_SELECT_FOLDER] = "Wybierz Folder Ulubionych...",
    [_L_APP_AMIIDB_FAV_SUCCESS] = "Dodano do Ulubionych",
    [_L_APP_AMIIDB_FAV_FAILED] = "Błąd Dodawania do Ulubionych!",
    [_L_APP_AMIIDB_SLOT_SAVE_SUCCESS] = "Zapisano",
    [_L_APP_AMIIDB_SLOT_SAVE_FAILED] = "Błąd Zapisywania!",
    [_L_APP_AMIIDB_SORT_FIELD] = "Pole sortowania",
    [_L_APP_AMIIDB_SORT_DEFAULT] = "Domyślne",
    [_L_APP_AMIIDB_SORT_NAME] = "Nazwa",
    [_L_APP_AMIIDB_NOT_SUPPORT_V3] = "",
    [_L_APP_CHAMELEON] = "Emulator Kart",
    [_L_APP_CHAMELEON_TAG_MF1_WRITE_NORMAL] = "Normalny",
    [_L_APP_CHAMELEON_TAG_MF1_WRITE_DENIED] = "Odmów",
    [_L_APP_CHAMELEON_TAG_MF1_WRITE_DECEIVE] = "Ignoruj",
    [_L_APP_CHAMELEON_TAG_MF1_WRITE_SHADOW] = "Cache",
    [_L_APP_CHAMELEON_INITIALIZING] = "Inicjalizacja danych ...",
    [_L_APP_CHAMELEON_CARD_SLOT] = "Slot",
    [_L_APP_CHAMELEON_CARD_NICK] = "Nick",
    [_L_APP_CHAMELEON_CARD_ID] = "ID",
    [_L_APP_CHAMELEON_CARD_TYPE] = "Typ",
    [_L_APP_CHAMELEON_CARD_DATA] = "Dane...",
    [_L_APP_CHAMELEON_CARD_ADVANCED] = "Zaawansowane...",
    [_L_APP_CHAMELEON_CARD_SLOT_SETTINGS] = "Ustawienia Slotów...",
    [_L_APP_CHAMELEON_CARD_SLOT_NUM] = "Ilość Slotów...",
    [_L_APP_CHAMELEON_CARD_SET_NICK_SUCCESS] = "Zmieniono Nick",
    [_L_APP_CHAMELEON_CARD_SET_NICK_FAILED] = "Błąd!",
    [_L_APP_CHAMELEON_CARD_INPUT_NICK] = "Wprowadź nick:",
    [_L_APP_CHAMELEON_CARD_DATA_LOAD] = "Wczytaj...",
    [_L_APP_CHAMELEON_CARD_DATA_SAVE] = "Zapisz...",
    [_L_APP_CHAMELEON_CARD_DATA_FACTORY] = "Przywróć do Domyślnych...",
    [_L_APP_CHAMELEON_CARD_DATA_FACTORY_SUCCESS] = "Przywrócono domyślne",
    [_L_APP_CHAMELEON_CARD_DATA_LOAD_NOT_FOUND] = "Nie znaleziono pliku",
    [_L_APP_CHAMELEON_CARD_DATA_LOAD_SIZE_NOT_MATCH] = "Nieprawidłowy rozmiar pliku",
    [_L_APP_CHAMELEON_CARD_DATA_LOAD_FAILED] = "Błąd ładowania pliku",
    [_L_APP_CHAMELEON_CARD_DATA_LOAD_SUCCESS] = "Plik został załadowany",
    [_L_APP_CHAMELEON_CARD_DATA_SAVE_INPUT_FILE_NAME] = "Wprowadź nazwę pliku:",
    [_L_APP_CHAMELEON_CARD_DATA_SAVE_FAILED] = "Błąd zapisywania pliku!",
    [_L_APP_CHAMELEON_CARD_DATA_SAVE_SUCCESS] = "Plik został zapisany",
    [_L_APP_CHAMELEON_CARD_ADV_CUSTOM_MODE] = "Tryb Niestandardowy",
    [_L_APP_CHAMELEON_CARD_ADV_LOAD_BLOCK0] = "",
    [_L_APP_CHAMELEON_CARD_ADV_LOAD_BLOCK0_SUCCESS] = "",
    [_L_APP_CHAMELEON_CARD_ID_SIZE] = "",
    [_L_APP_CHAMELEON_CARD_GEN1A_MODE] = "Gen1A Aktywny",
    [_L_APP_CHAMELEON_CARD_GENERATE_UID] = "Generuj UID",
    [_L_APP_CHAMELEON_CARD_GENERATE_UID_SUCCESS] = "UID Został Wygenerowany",
    [_L_APP_CHAMELEON_CARD_GEN2_MODE] = "Gen2 Aktywny",
    [_L_APP_CHAMELEON_CARD_WRITE_MODE] = "Tryb Zapisu",
    [_L_APP_CHAMELEON_CARD_ADV_ID_EDIT_INVALID_INPUT] = "Nieprawidłowe dane wejściowe!",
    [_L_APP_CHAMELEON_CARD_TYPE_FACTORY_DATA_CONFRIM] = "Zmieniono typ karty.\nUstawić domyślne dane?",
    [_L_APP_CHAMELEON_CARD_DEFAULT_CARD] = "Domyślna Karta",
    [_L_APP_GAME] = "Gry",
    [_L_APP_GAME_TINY_ARKANOID] = "",
    [_L_APP_GAME_TINY_INVADERS] = "",
    [_L_APP_GAME_TINY_LANDER] = "",
    [_L_APP_GAME_TINY_TRIS] = "",
};
