solosky/pixl.js/fw/application/src/i18n/pt_BR.c

#include "string_id.h"
const char * const lang_pt_BR[_L_COUNT] = {
    [_L_ON] = "LIGADO",
    [_L_OFF] = "DESLIGADO",
    [_L_ON_F] = "[LIGADO]",
    [_L_OFF_F] = "[DESLIGADO]",
    [_L_BACK] = "Voltar",
    [_L_ERR] = "Erro",
    [_L_ERR_CODE] = "Código de Erro",
    [_L_FAILED] = "",
    [_L_BYTES] = "",
    [_L_APP_AMIIBO] = "Emulador de Amiibo",
    [_L_APP_AMIIBOLINK] = "AmiiboLink",
    [_L_APP_BLE] = "Transferência de Arquivos BLE",
    [_L_APP_BLE_TITLE] = "Transferência de Arquivos BLE",
    [_L_APP_PLAYER] = "Reprodutor de Vídeo",
    [_L_APP_SET] = "Configurações",
    [_L_APP_SET_VERSION] = "Versão",
    [_L_APP_SET_STORAGE_USED] = "Usado",
    [_L_APP_SET_STORAGE] = "Armazenamento Externo",
    [_L_APP_SET_OLED_CONTRAST] = "Contraste do",
    [_L_APP_SET_OLED_CONTRAST_TITLE] = "Contraste do",
    [_L_APP_SET_LCD_BACKLIGHT] = "Luz de Fundo",
    [_L_APP_SET_LCD_BACKLIGHT_TITLE] = "Brilho da Luz de Fundo",
    [_L_APP_SET_ANIM] = "Animação do Menu",
    [_L_APP_SET_LIPO_BAT] = "Bateria LiPO",
    [_L_APP_SET_SHOW_MEM_USAGE] = "Memória Usada",
    [_L_APP_SET_HIBERNATE] = "Despertar Rápido",
    [_L_APP_SET_SLEEP_TIMEOUT] = "Tempo Limite de Suspensão",
    [_L_APP_SET_LANGUAGE] = "Idioma",
    [_L_APP_SET_GO_SLEEP] = "",
    [_L_APP_SET_DFU] = "Atualização de Firmware",
    [_L_APP_SET_REBOOT] = "Reinicialização do Sistema",
    [_L_APP_SET_RESET_DEFAULT] = "Restaurar Configurações Padrão",
    [_L_APP_SET_RESET_DEFAULT_SUCCESS] = "Redefinir a Configuração Padrão",
    [_L_APP_SET_RESET_DEFAULT_CONFIRM] = "",
    [_L_APP_SET_ABOUT] = "",
    [_L_APP_SET_ABOUT_OPEN_SOURCE_PROJECT] = "",
    [_L_APP_SET_ABOUT_LGPL_LICENSE] = "",
    [_L_APP_SET_APP_MGMT] = "",
    [_L_15S] = "15 seg.",
    [_L_30S] = "30 seg.",
    [_L_45S] = "45 seg.",
    [_L_1MIN] = "1 min.",
    [_L_2MIN] = "2 min.",
    [_L_3MIN] = "3 min.",
    [_L_AMIIBO_KEY_UNLOADED] = "A chave Amiibo não foi carregada",
    [_L_UPLOAD_KEY_RETAIL_BIN] = "Carregue o arquivo key_retail.bin no diretório raiz do armazenamento.",
    [_L_KNOW] = "Entendi",
    [_L_RANDOM_GENERATION] = "Randomizar Etiqueta",
    [_L_AUTO_RANDOM_GENERATION] = "Randomização Automática",
    [_L_SET_CUSTOM_ID] = "",
    [_L_INPUT_ID] = "",
    [_L_INAVLID_ID] = "",
    [_L_SHOW_QRCODE] = "Exibir QR Code",
    [_L_READ_ONLY] = "",
    [_L_DELETE_TAG] = "Excluir Etiqueta",
    [_L_DELETE_TAG_CONFIRM] = "Confirmar Exclusão de %s ?",
    [_L_BACK_TO_DETAILS] = "Voltar Aos Detalhes da Tag",
    [_L_BACK_TO_FILE_LIST] = "Voltar Para a Lista de Arquivos",
    [_L_BACK_TO_MAIN_MENU] = "Voltar ao Menu Principal",
    [_L_FORMAT] = "Formatar",
    [_L_FORMAT_STORAGE] = "Formatar Armazenamento",
    [_L_DELETE_ALL_DATA] = "Isso excluirá todos os dados. Confirmar a formatação?",
    [_L_DELETING_MESSAGE] = "Formatando ...",
    [_L_MESSAGE] = "Mensagem",
    [_L_CONFIRM] = "Confirmar",
    [_L_CANCEL] = "Cancelar",
    [_L_BACK_TO_LIST] = "Voltar à Lista",
    [_L_NOT_MOUNTED] = "Não Montado",
    [_L_MOUNTED_LFS] = "===Montado[LFS]===",
    [_L_MOUNTED_FFS] = "===Montado[FFS]===",
    [_L_TOTAL_SPACE] = "Total",
    [_L_AVAILABLE_SPACE] = "Livre",
    [_L_NOT_AMIIBO_FILE] = "Este Não é um Arquivo Amiibo",
    [_L_READ_FILE_FAILED] = "Falha na Leitura do Arquivo",
    [_L_INPUT_FOLDER_NAME] = "Nome da Pasta de Entrada:",
    [_L_INPUT_AMIIBO_NAME] = "Nome do Amiibo de Entrada:",
    [_L_DELETE_FILE] = "Excluir %s ?",
    [_L_DELETE] = "Excluir...",
    [_L_TIPS] = "Confirmar",
    [_L_INPUT_NEW_NAME] = "Novo Nome de Entrada:",
    [_L_INVALID_INPUT] = "Entrada Inválida",
    [_L_CREATE_NEW_FOLDER] = "Criar Nova Pasta...",
    [_L_CREATE_NEW_TAG] = "Criar Nova Tag...",
    [_L_CREATE_NEW_TAG_BATCH] = "Criar Novas Tags em Lote...",
    [_L_INPUT_TAG_NUM] = "Número da Tag de Entrada:",
    [_L_CREATE_TOO_MANY_NUM] = "Somente no máximo %d tags criadas em um lote.",
    [_L_CREATING_TAG_BATCH] = "Criando tag",
    [_L_CREATING_TAG_FAILED] = "Falha ao criar a tag %s!",
    [_L_RENAME] = "Renomear...",
    [_L_OPEN_FOLDER_FAILED] = "Falha ao abrir a pasta",
    [_L_RENAME_FAILED] = "Falha ao renomear\nCódigo de erro",
    [_L_MAIN_RETURN] = "[RETORNO]",
    [_L_RANDOM_MODE_MANUAL] = "Randomizar (Manual)",
    [_L_RANDOM_MODE_AUTO] = "Randomizar (Automático)",
    [_L_SEQUENCE_MODE] = "Modo Sequencial",
    [_L_READ_WRITE_MODE] = "Modo de Leitura e Gravação",
    [_L_AMIIBOLINK_V1] = "V1",
    [_L_AMIIBOLINK_V2] = "V2",
    [_L_AMILOOP] = "AmiLoop",
    [_L_MODE] = "Modo",
    [_L_AUTO_RANDOM] = "Randomização Automática",
    [_L_COMPATIBLE_MODE] = "Modo Compatível",
    [_L_TAG_DETAILS] = "[Detalhes da Tag]",
    [_L_MAIN_MENU] = "[Menu Principal]",
    [_L_MODE_RANDOM] = "Randomização (Manual)",
    [_L_MODE_CYCLE] = "Sequencial",
    [_L_MODE_NTAG] = "Leitura/gravação",
    [_L_MODE_RANDOM_AUTO_GEN] = "Randomização (Automática)",
    [_L_BLANK_TAG] = "Tag NFC em Branco",
    [_L_APP_AMIIDB] = "Banco de Dados Amiibo",
    [_L_APP_AMMIDB_BROWSER] = "Navegador...",
    [_L_APP_AMIIDB_SEARCH] = "Pesquisar...",
    [_L_APP_AMIIDB_MY_FAVORITES] = "Meus Favoritos...",
    [_L_APP_AMIIDB_MY_TAGS] = "Meu Amiibo...",
    [_L_APP_AMIIDB_SETTINGS] = "Configurações...",
    [_L_APP_AMIIDB_EXIT] = "[Sair]",
    [_L_APP_AMIIDB_BACK] = "[Retornar]",
    [_L_APP_AMIIDB_SETTINGS_AMIIBO_KEY] = "Teclas",
    [_L_APP_AMIIDB_SETTINGS_AMIIBO_KEY_LOADED] = "Carregado",
    [_L_APP_AMIIDB_SETTINGS_AMIIBO_KEY_NOT_LOADED] = "NÃO Carregadas",
    [_L_APP_AMIIDB_SETTINGS_SLOT_NUM] = "Número do Slot",
    [_L_APP_AMIIDB_DETAIL_FAVORITE] = "Favorito...",
    [_L_APP_AMIIDB_DETAIL_SAVE_AS] = "Salvar como...",
    [_L_APP_AMIIDB_DETAIL_BACK_DETAIL] = "[Voltar Para Detalhes]",
    [_L_APP_AMIIDB_DETAIL_BACK_LIST] = "[Voltar Para a Lista]",
    [_L_APP_AMIIDB_SEARCH_HEAD] = "Pesquisar:",
    [_L_APP_AMIIDB_MORE] = "[Mais...]",
    [_L_APP_AMIIDB_MORE_MESSAGE] = "",
    [_L_APP_AMIIDB_EMPTY_TAG] = "<Amiibo em Branco>",
    [_L_APP_AMIIDB_SLOT_DELETE] = "Reiniciar...",
    [_L_APP_AMIIDB_CONFIRM] = "Confirmar",
    [_L_APP_AMIIDB_CANCEL] = "Cancelar",
    [_L_APP_AMIIDB_TIPS] = "Confirmar",
    [_L_APP_AMIIDB_NEW] = "Novo...",
    [_L_APP_AMIIDB_EMPTY] = "Vazio...",
    [_L_APP_AMIIDB_DELETE] = "Excluir...",
    [_L_APP_AMIIDB_FAV_NEW_HEAD] = "Nova Pasta de Favoritos:",
    [_L_APP_AMIIDB_FAV_EMPTY_MSG] = "Esvaziar Pasta de Favoritos?",
    [_L_APP_AMIIDB_FAV_DELETE_MSG] = "Confirmar Exclusão?",
    [_L_APP_AMIIDB_FAV_SELECT_FOLDER] = "Selecionar Pasta Favorita...",
    [_L_APP_AMIIDB_FAV_SUCCESS] = "Favorito Bem-Sucedido",
    [_L_APP_AMIIDB_FAV_FAILED] = "Favorito Falhou!",
    [_L_APP_AMIIDB_SLOT_SAVE_SUCCESS] = "Salvar Com Êxito",
    [_L_APP_AMIIDB_SLOT_SAVE_FAILED] = "Falha ao Salvar!",
    [_L_APP_AMIIDB_SORT_FIELD] = "Campo de Ordenação",
    [_L_APP_AMIIDB_SORT_DEFAULT] = "Padrão",
    [_L_APP_AMIIDB_SORT_NAME] = "Nome",
    [_L_APP_AMIIDB_NOT_SUPPORT_V3] = "",
    [_L_APP_CHAMELEON] = "Emulador de Cartão",
    [_L_APP_CHAMELEON_TAG_MF1_WRITE_NORMAL] = "Normal",
    [_L_APP_CHAMELEON_TAG_MF1_WRITE_DENIED] = "Negar",
    [_L_APP_CHAMELEON_TAG_MF1_WRITE_DECEIVE] = "Ignorar",
    [_L_APP_CHAMELEON_TAG_MF1_WRITE_SHADOW] = "Cache",
    [_L_APP_CHAMELEON_INITIALIZING] = "Inicialização de Dados ...",
    [_L_APP_CHAMELEON_CARD_SLOT] = "Slot",
    [_L_APP_CHAMELEON_CARD_NICK] = "Apelido",
    [_L_APP_CHAMELEON_CARD_ID] = "ID",
    [_L_APP_CHAMELEON_CARD_TYPE] = "Tipo de Dados",
    [_L_APP_CHAMELEON_CARD_DATA] = "Dados...",
    [_L_APP_CHAMELEON_CARD_ADVANCED] = "Avançado...",
    [_L_APP_CHAMELEON_CARD_SLOT_SETTINGS] = "Configurações de Slots...",
    [_L_APP_CHAMELEON_CARD_SLOT_NUM] = "Número do Slot...",
    [_L_APP_CHAMELEON_CARD_SET_NICK_SUCCESS] = "Apelido Definido com Sucesso",
    [_L_APP_CHAMELEON_CARD_SET_NICK_FAILED] = "Falha ao Definir Apelido!",
    [_L_APP_CHAMELEON_CARD_INPUT_NICK] = "Insira o Apelido:",
    [_L_APP_CHAMELEON_CARD_DATA_LOAD] = "Carregar...",
    [_L_APP_CHAMELEON_CARD_DATA_SAVE] = "Salvar...",
    [_L_APP_CHAMELEON_CARD_DATA_FACTORY] = "Restaurar Padrões...",
    [_L_APP_CHAMELEON_CARD_DATA_FACTORY_SUCCESS] = "Restauração de Dados Bem-Sucedida",
    [_L_APP_CHAMELEON_CARD_DATA_LOAD_NOT_FOUND] = "Arquivo Não Encontrado",
    [_L_APP_CHAMELEON_CARD_DATA_LOAD_SIZE_NOT_MATCH] = "Tamanho do Arquivo Não Corresponde",
    [_L_APP_CHAMELEON_CARD_DATA_LOAD_FAILED] = "Falha no Carregamento do Arquivo",
    [_L_APP_CHAMELEON_CARD_DATA_LOAD_SUCCESS] = "Sucesso no Carregamento do Arquivo",
    [_L_APP_CHAMELEON_CARD_DATA_SAVE_INPUT_FILE_NAME] = "Nome do Arquivo de Entrada:",
    [_L_APP_CHAMELEON_CARD_DATA_SAVE_FAILED] = "Falha ao Salvar o Arquivo!",
    [_L_APP_CHAMELEON_CARD_DATA_SAVE_SUCCESS] = "Arquivo Salvo com êxito",
    [_L_APP_CHAMELEON_CARD_ADV_CUSTOM_MODE] = "Modo Personalizado",
    [_L_APP_CHAMELEON_CARD_ADV_LOAD_BLOCK0] = "",
    [_L_APP_CHAMELEON_CARD_ADV_LOAD_BLOCK0_SUCCESS] = "",
    [_L_APP_CHAMELEON_CARD_ID_SIZE] = "",
    [_L_APP_CHAMELEON_CARD_GEN1A_MODE] = "Gen1A Ativada",
    [_L_APP_CHAMELEON_CARD_GENERATE_UID] = "UID Aleatório",
    [_L_APP_CHAMELEON_CARD_GENERATE_UID_SUCCESS] = "UID Gerado",
    [_L_APP_CHAMELEON_CARD_GEN2_MODE] = "Gen2 Ativado",
    [_L_APP_CHAMELEON_CARD_WRITE_MODE] = "Modo de Gravação",
    [_L_APP_CHAMELEON_CARD_ADV_ID_EDIT_INVALID_INPUT] = "Entrada Inválida!",
    [_L_APP_CHAMELEON_CARD_TYPE_FACTORY_DATA_CONFRIM] = "O tipo de cartão foi alterado. \nRedefinir dados do cartão?",
    [_L_APP_CHAMELEON_CARD_DEFAULT_CARD] = "",
    [_L_APP_GAME] = "",
    [_L_APP_GAME_TINY_ARKANOID] = "",
    [_L_APP_GAME_TINY_INVADERS] = "",
    [_L_APP_GAME_TINY_LANDER] = "",
    [_L_APP_GAME_TINY_TRIS] = "",
};
