solosky/pixl.js/fw/application/src/i18n/pt_PT.c

#include "string_id.h"
const char * const lang_pt_PT[_L_COUNT] = {
    [_L_ON] = "SIM",
    [_L_OFF] = "NÃO",
    [_L_ON_F] = "[SIM]",
    [_L_OFF_F] = "[NÃO]",
    [_L_BACK] = "Voltar",
    [_L_ERR] = "Erro",
    [_L_ERR_CODE] = "Código de Erro",
    [_L_FAILED] = "",
    [_L_BYTES] = "",
    [_L_APP_AMIIBO] = "Emulador de Amiibo",
    [_L_APP_AMIIBOLINK] = "AmiiboLink",
    [_L_APP_BLE] = "Transferência BLE",
    [_L_APP_BLE_TITLE] = "Transferência BLE",
    [_L_APP_PLAYER] = "Reprodutor de vídeo",
    [_L_APP_SET] = "Definições",
    [_L_APP_SET_VERSION] = "Versão",
    [_L_APP_SET_STORAGE_USED] = "Usada",
    [_L_APP_SET_STORAGE] = "Memoria Externa",
    [_L_APP_SET_OLED_CONTRAST] = "Contraste",
    [_L_APP_SET_OLED_CONTRAST_TITLE] = "Contraste",
    [_L_APP_SET_LCD_BACKLIGHT] = "Brilho",
    [_L_APP_SET_LCD_BACKLIGHT_TITLE] = "Brilho do Ecrã",
    [_L_APP_SET_ANIM] = "Animação do Menu",
    [_L_APP_SET_LIPO_BAT] = "Bateria LiPO",
    [_L_APP_SET_SHOW_MEM_USAGE] = "Memoria Usada",
    [_L_APP_SET_HIBERNATE] = "Suspender",
    [_L_APP_SET_SLEEP_TIMEOUT] = "Suspender em:",
    [_L_APP_SET_LANGUAGE] = "Idioma",
    [_L_APP_SET_GO_SLEEP] = "",
    [_L_APP_SET_DFU] = "Atualizações",
    [_L_APP_SET_REBOOT] = "Reiniciar",
    [_L_APP_SET_RESET_DEFAULT] = "Repor Definições",
    [_L_APP_SET_RESET_DEFAULT_SUCCESS] = "Reposição Completa!",
    [_L_APP_SET_RESET_DEFAULT_CONFIRM] = "",
    [_L_APP_SET_ABOUT] = "",
    [_L_APP_SET_ABOUT_OPEN_SOURCE_PROJECT] = "",
    [_L_APP_SET_ABOUT_LGPL_LICENSE] = "",
    [_L_APP_SET_APP_MGMT] = "",
    [_L_15S] = "15 segundos",
    [_L_30S] = "30 segundos",
    [_L_45S] = "45 segundos",
    [_L_1MIN] = "1 minuto",
    [_L_2MIN] = "2 minutos",
    [_L_3MIN] = "3 minutos",
    [_L_AMIIBO_KEY_UNLOADED] = "Amiibo Key não encontrada",
    [_L_UPLOAD_KEY_RETAIL_BIN] = "Carregue o ficheiro key_retail.bin para a raiz do dispositivo.",
    [_L_KNOW] = "Confirmado",
    [_L_RANDOM_GENERATION] = "Tag Aleatória",
    [_L_AUTO_RANDOM_GENERATION] = "Tag Aleatória Auto.",
    [_L_SET_CUSTOM_ID] = "",
    [_L_INPUT_ID] = "",
    [_L_INAVLID_ID] = "",
    [_L_SHOW_QRCODE] = "Mostrar código QR",
    [_L_READ_ONLY] = "",
    [_L_DELETE_TAG] = "Apagar Tag",
    [_L_DELETE_TAG_CONFIRM] = "Apagar %s definitivamente?",
    [_L_BACK_TO_DETAILS] = "Voltar para detalhes",
    [_L_BACK_TO_FILE_LIST] = "Voltar para lista",
    [_L_BACK_TO_MAIN_MENU] = "Voltar para menu principal",
    [_L_FORMAT] = "Formatar",
    [_L_FORMAT_STORAGE] = "Formatar memória",
    [_L_DELETE_ALL_DATA] = "Isto vai eliminar todos os dados. Confirmar formtação?",
    [_L_DELETING_MESSAGE] = "A Formatar...",
    [_L_MESSAGE] = "A Iniciar",
    [_L_CONFIRM] = "Confirmar",
    [_L_CANCEL] = "Cancelar",
    [_L_BACK_TO_LIST] = "Voltar para lista",
    [_L_NOT_MOUNTED] = "Não montado",
    [_L_MOUNTED_LFS] = "===[LFS]Montado===",
    [_L_MOUNTED_FFS] = "===[FFS]Montado===",
    [_L_TOTAL_SPACE] = "Total",
    [_L_AVAILABLE_SPACE] = "Livre",
    [_L_NOT_AMIIBO_FILE] = "Ficheiro amiibo incorreto",
    [_L_READ_FILE_FAILED] = "Falha ao ler ficheiro",
    [_L_INPUT_FOLDER_NAME] = "Introduzir nome da pasta:",
    [_L_INPUT_AMIIBO_NAME] = "Introduzir nome do Amiibo:",
    [_L_DELETE_FILE] = "",
    [_L_DELETE] = "Apagar",
    [_L_TIPS] = "",
    [_L_INPUT_NEW_NAME] = "Introduzir novo nome:",
    [_L_INVALID_INPUT] = "Entrada inválida",
    [_L_CREATE_NEW_FOLDER] = "Criar nova pasta...",
    [_L_CREATE_NEW_TAG] = "Criar nova Tag...",
    [_L_CREATE_NEW_TAG_BATCH] = "Criar multiplos tags...",
    [_L_INPUT_TAG_NUM] = "Quantas tags?",
    [_L_CREATE_TOO_MANY_NUM] = "O limite de tags é %d.",
    [_L_CREATING_TAG_BATCH] = "A Criar Tag",
    [_L_CREATING_TAG_FAILED] = "Criação de Tag %s falhou!",
    [_L_RENAME] = "Renomear ",
    [_L_OPEN_FOLDER_FAILED] = "Falha ao abrir pasta",
    [_L_RENAME_FAILED] = "Falha ao renomear\nCódigo de Erro",
    [_L_MAIN_RETURN] = "[VOLTAR]",
    [_L_RANDOM_MODE_MANUAL] = "Aleatório (Manual)",
    [_L_RANDOM_MODE_AUTO] = "Aleatório (Auto)",
    [_L_SEQUENCE_MODE] = "Modo Sequencial",
    [_L_READ_WRITE_MODE] = "Modo Leitura-Escrita",
    [_L_AMIIBOLINK_V1] = "V1",
    [_L_AMIIBOLINK_V2] = "V2",
    [_L_AMILOOP] = "AmiLoop",
    [_L_MODE] = "Modo",
    [_L_AUTO_RANDOM] = "Modo Aleatório Automático",
    [_L_COMPATIBLE_MODE] = "Modo Compatibilidade",
    [_L_TAG_DETAILS] = "[Voltar a detalhes]",
    [_L_MAIN_MENU] = "[Menu Principal]",
    [_L_MODE_RANDOM] = "Aleatório (Manual)",
    [_L_MODE_CYCLE] = "Sequencia",
    [_L_MODE_NTAG] = "Leitura/Escrita",
    [_L_MODE_RANDOM_AUTO_GEN] = "Randomização Automática ",
    [_L_BLANK_TAG] = "Tag NFC vazia",
    [_L_APP_AMIIDB] = "Base de dados Amiibo",
    [_L_APP_AMMIDB_BROWSER] = "Navegar...",
    [_L_APP_AMIIDB_SEARCH] = "Pesquisar...",
    [_L_APP_AMIIDB_MY_FAVORITES] = "Favoritos...",
    [_L_APP_AMIIDB_MY_TAGS] = "Os meus amiibos...",
    [_L_APP_AMIIDB_SETTINGS] = "Definições",
    [_L_APP_AMIIDB_EXIT] = "[Exit]",
    [_L_APP_AMIIDB_BACK] = "[Back]",
    [_L_APP_AMIIDB_SETTINGS_AMIIBO_KEY] = "Keys (Chaves)",
    [_L_APP_AMIIDB_SETTINGS_AMIIBO_KEY_LOADED] = "Carregado",
    [_L_APP_AMIIDB_SETTINGS_AMIIBO_KEY_NOT_LOADED] = "NÃO carregado",
    [_L_APP_AMIIDB_SETTINGS_SLOT_NUM] = "Slot numero",
    [_L_APP_AMIIDB_DETAIL_FAVORITE] = "Favorito",
    [_L_APP_AMIIDB_DETAIL_SAVE_AS] = "Guardar como..",
    [_L_APP_AMIIDB_DETAIL_BACK_DETAIL] = "[Voltar para Detalhes]",
    [_L_APP_AMIIDB_DETAIL_BACK_LIST] = "[Voltar para lista]",
    [_L_APP_AMIIDB_SEARCH_HEAD] = "Pesquisar",
    [_L_APP_AMIIDB_MORE] = "[Mais...]",
    [_L_APP_AMIIDB_MORE_MESSAGE] = "",
    [_L_APP_AMIIDB_EMPTY_TAG] = "<Amiibo vazio>",
    [_L_APP_AMIIDB_SLOT_DELETE] = "Reiniciar",
    [_L_APP_AMIIDB_CONFIRM] = "Confirmar",
    [_L_APP_AMIIDB_CANCEL] = "Cancelar",
    [_L_APP_AMIIDB_TIPS] = "Confirmar",
    [_L_APP_AMIIDB_NEW] = "Novo...",
    [_L_APP_AMIIDB_EMPTY] = "Vazio...",
    [_L_APP_AMIIDB_DELETE] = "Apagar...",
    [_L_APP_AMIIDB_FAV_NEW_HEAD] = "Nova pasta favorita:",
    [_L_APP_AMIIDB_FAV_EMPTY_MSG] = "Limpar pasta de favoritos?",
    [_L_APP_AMIIDB_FAV_DELETE_MSG] = "Confirmar eliminação?",
    [_L_APP_AMIIDB_FAV_SELECT_FOLDER] = "Selecionar pasta de favoritos",
    [_L_APP_AMIIDB_FAV_SUCCESS] = "Adicionado aos Favoritos",
    [_L_APP_AMIIDB_FAV_FAILED] = "Favorito falhou!",
    [_L_APP_AMIIDB_SLOT_SAVE_SUCCESS] = "Guardado com sucesso",
    [_L_APP_AMIIDB_SLOT_SAVE_FAILED] = "Falha ao Guardar!",
    [_L_APP_AMIIDB_SORT_FIELD] = "Campo de Ordenação",
    [_L_APP_AMIIDB_SORT_DEFAULT] = "Padrão",
    [_L_APP_AMIIDB_SORT_NAME] = "Nome",
    [_L_APP_AMIIDB_NOT_SUPPORT_V3] = "",
    [_L_APP_CHAMELEON] = "Emular Tag RFID",
    [_L_APP_CHAMELEON_TAG_MF1_WRITE_NORMAL] = "Normal",
    [_L_APP_CHAMELEON_TAG_MF1_WRITE_DENIED] = "Cancelar",
    [_L_APP_CHAMELEON_TAG_MF1_WRITE_DECEIVE] = "Ignorar",
    [_L_APP_CHAMELEON_TAG_MF1_WRITE_SHADOW] = "Cache",
    [_L_APP_CHAMELEON_INITIALIZING] = "Inicializando ambiente.\nPor favor espere..",
    [_L_APP_CHAMELEON_CARD_SLOT] = "Ranhura",
    [_L_APP_CHAMELEON_CARD_NICK] = "Nick",
    [_L_APP_CHAMELEON_CARD_ID] = "ID",
    [_L_APP_CHAMELEON_CARD_TYPE] = "Tipo",
    [_L_APP_CHAMELEON_CARD_DATA] = "Dados..",
    [_L_APP_CHAMELEON_CARD_ADVANCED] = "Avançado..",
    [_L_APP_CHAMELEON_CARD_SLOT_SETTINGS] = "Definições de Ranhura..",
    [_L_APP_CHAMELEON_CARD_SLOT_NUM] = "Ranhura numero...",
    [_L_APP_CHAMELEON_CARD_SET_NICK_SUCCESS] = "Nick definido com sucesso",
    [_L_APP_CHAMELEON_CARD_SET_NICK_FAILED] = "Definição do Nick falhou!",
    [_L_APP_CHAMELEON_CARD_INPUT_NICK] = "Introduzir Nick",
    [_L_APP_CHAMELEON_CARD_DATA_LOAD] = "Carregar..",
    [_L_APP_CHAMELEON_CARD_DATA_SAVE] = "Guardar..",
    [_L_APP_CHAMELEON_CARD_DATA_FACTORY] = "Iniciar..",
    [_L_APP_CHAMELEON_CARD_DATA_FACTORY_SUCCESS] = "Dados carregados com sucesso",
    [_L_APP_CHAMELEON_CARD_DATA_LOAD_NOT_FOUND] = "Ficheiro não encontrado",
    [_L_APP_CHAMELEON_CARD_DATA_LOAD_SIZE_NOT_MATCH] = "Tamanho do ficheiro incorreto",
    [_L_APP_CHAMELEON_CARD_DATA_LOAD_FAILED] = "Falha ao carregar ficheiro",
    [_L_APP_CHAMELEON_CARD_DATA_LOAD_SUCCESS] = "Ficheiro carregado com sucesso",
    [_L_APP_CHAMELEON_CARD_DATA_SAVE_INPUT_FILE_NAME] = "Nome do Ficheiro:",
    [_L_APP_CHAMELEON_CARD_DATA_SAVE_FAILED] = "Erro ao guardar!",
    [_L_APP_CHAMELEON_CARD_DATA_SAVE_SUCCESS] = "Guardado com sucesso",
    [_L_APP_CHAMELEON_CARD_ADV_CUSTOM_MODE] = "Modo personalizado",
    [_L_APP_CHAMELEON_CARD_ADV_LOAD_BLOCK0] = "",
    [_L_APP_CHAMELEON_CARD_ADV_LOAD_BLOCK0_SUCCESS] = "",
    [_L_APP_CHAMELEON_CARD_ID_SIZE] = "",
    [_L_APP_CHAMELEON_CARD_GEN1A_MODE] = "Gen1A ativado",
    [_L_APP_CHAMELEON_CARD_GENERATE_UID] = "Gerar novo UID",
    [_L_APP_CHAMELEON_CARD_GENERATE_UID_SUCCESS] = "UID gerado",
    [_L_APP_CHAMELEON_CARD_GEN2_MODE] = "Gen2 ativado",
    [_L_APP_CHAMELEON_CARD_WRITE_MODE] = "Modo escrita",
    [_L_APP_CHAMELEON_CARD_ADV_ID_EDIT_INVALID_INPUT] = "Texto invalida",
    [_L_APP_CHAMELEON_CARD_TYPE_FACTORY_DATA_CONFRIM] = "Tipo de cartão alterado. \nFormatar cartão?",
    [_L_APP_CHAMELEON_CARD_DEFAULT_CARD] = "",
    [_L_APP_GAME] = "",
    [_L_APP_GAME_TINY_ARKANOID] = "",
    [_L_APP_GAME_TINY_INVADERS] = "",
    [_L_APP_GAME_TINY_LANDER] = "",
    [_L_APP_GAME_TINY_TRIS] = "",
};
