solosky/pixl.js/fw/application/src/i18n/ru_RU.c

#include "string_id.h"
const char * const lang_ru_RU[_L_COUNT] = {
    [_L_ON] = "Включено",
    [_L_OFF] = "Выключено",
    [_L_ON_F] = "[Вкл]",
    [_L_OFF_F] = "[Выкл]",
    [_L_BACK] = "[Назад]",
    [_L_ERR] = "Ошибка",
    [_L_ERR_CODE] = "Код ошибки",
    [_L_FAILED] = "Ошибка",
    [_L_BYTES] = "байт",
    [_L_APP_AMIIBO] = "Эмулятор Amiibo",
    [_L_APP_AMIIBOLINK] = "AmiiboLink",
    [_L_APP_BLE] = "Передача файлов",
    [_L_APP_BLE_TITLE] = "по Bluetooth",
    [_L_APP_PLAYER] = "Видеоплеер",
    [_L_APP_SET] = "Настройки",
    [_L_APP_SET_VERSION] = "Версия",
    [_L_APP_SET_STORAGE_USED] = "Занято",
    [_L_APP_SET_STORAGE] = "Накопитель",
    [_L_APP_SET_OLED_CONTRAST] = "Контрастность",
    [_L_APP_SET_OLED_CONTRAST_TITLE] = "Контраст",
    [_L_APP_SET_LCD_BACKLIGHT] = "Подсветка",
    [_L_APP_SET_LCD_BACKLIGHT_TITLE] = "Яркость подсветки",
    [_L_APP_SET_ANIM] = "Анимация меню",
    [_L_APP_SET_LIPO_BAT] = "Батарея LiPO",
    [_L_APP_SET_SHOW_MEM_USAGE] = "Статус памяти",
    [_L_APP_SET_HIBERNATE] = "Гибернация",
    [_L_APP_SET_SLEEP_TIMEOUT] = "Таймаут сна",
    [_L_APP_SET_LANGUAGE] = "Язык",
    [_L_APP_SET_GO_SLEEP] = "В режим сна",
    [_L_APP_SET_DFU] = "Обновление ПО",
    [_L_APP_SET_REBOOT] = "Перезагрузка",
    [_L_APP_SET_RESET_DEFAULT] = "Сброс настроек",
    [_L_APP_SET_RESET_DEFAULT_SUCCESS] = "Сброс выполнен",
    [_L_APP_SET_RESET_DEFAULT_CONFIRM] = "Выполнить?",
    [_L_APP_SET_ABOUT] = "Об устройстве",
    [_L_APP_SET_ABOUT_OPEN_SOURCE_PROJECT] = "Проект с открытым кодом",
    [_L_APP_SET_ABOUT_LGPL_LICENSE] = "Лицензия GPL 2.0",
    [_L_APP_SET_APP_MGMT] = "Ярлыки главного меню",
    [_L_15S] = "15 секунд",
    [_L_30S] = "30 секунд",
    [_L_45S] = "45 секунд",
    [_L_1MIN] = "1 минута",
    [_L_2MIN] = "2 минуты",
    [_L_3MIN] = "3 минуты",
    [_L_AMIIBO_KEY_UNLOADED] = "Отсутствует файл ключа",
    [_L_UPLOAD_KEY_RETAIL_BIN] = "Поместите key_retail.bin\n в корень накопителя",
    [_L_KNOW] = "[Понятно]",
    [_L_RANDOM_GENERATION] = "Сгенерировать UUID",
    [_L_AUTO_RANDOM_GENERATION] = "Автогенерация",
    [_L_SET_CUSTOM_ID] = "Заказной ID",
    [_L_INPUT_ID] = "Задайте ID",
    [_L_INAVLID_ID] = "Недопустимый ID",
    [_L_SHOW_QRCODE] = "QR-код",
    [_L_READ_ONLY] = "Только чтение",
    [_L_DELETE_TAG] = "Удалить тег",
    [_L_DELETE_TAG_CONFIRM] = "Удалить %s?",
    [_L_BACK_TO_DETAILS] = "[Назад к деталям]",
    [_L_BACK_TO_FILE_LIST] = "[Назад к списку]",
    [_L_BACK_TO_MAIN_MENU] = "[В главное меню]",
    [_L_FORMAT] = "Отформатировать",
    [_L_FORMAT_STORAGE] = "Форматирование",
    [_L_DELETE_ALL_DATA] = "Это удалит все данные.\nВыполнить?",
    [_L_DELETING_MESSAGE] = "Форматирование...",
    [_L_MESSAGE] = "Сообщение",
    [_L_CONFIRM] = "Да",
    [_L_CANCEL] = "Отмена",
    [_L_BACK_TO_LIST] = "[Назад к списку]",
    [_L_NOT_MOUNTED] = "==[Не подключён]==",
    [_L_MOUNTED_LFS] = "==Подключён[LFS]==",
    [_L_MOUNTED_FFS] = "==Подключён[FFS]==",
    [_L_TOTAL_SPACE] = "Ёмкость",
    [_L_AVAILABLE_SPACE] = "Свободно",
    [_L_NOT_AMIIBO_FILE] = "Этот файл не Amiibo",
    [_L_READ_FILE_FAILED] = "Ошибка чтения файла",
    [_L_INPUT_FOLDER_NAME] = "Задайте имя папки:",
    [_L_INPUT_AMIIBO_NAME] = "Задайте имя Amiibo:",
    [_L_DELETE_FILE] = "Удалить %s?",
    [_L_DELETE] = "Удалить...",
    [_L_TIPS] = "Внимание",
    [_L_INPUT_NEW_NAME] = "Задайте новое имя:",
    [_L_INVALID_INPUT] = "Недопустимый ввод",
    [_L_CREATE_NEW_FOLDER] = "Создать новую папку...",
    [_L_CREATE_NEW_TAG] = "Создать новый тег...",
    [_L_CREATE_NEW_TAG_BATCH] = "Создать группу тегов...",
    [_L_INPUT_TAG_NUM] = "Задайте число тегов:",
    [_L_CREATE_TOO_MANY_NUM] = "За раз можно создать\n не более %d тегов",
    [_L_CREATING_TAG_BATCH] = "Создание тега",
    [_L_CREATING_TAG_FAILED] = "Ошибка создания тега %s",
    [_L_RENAME] = "Переименовать...",
    [_L_OPEN_FOLDER_FAILED] = "Ошибка открытия папки",
    [_L_RENAME_FAILED] = "Ошибка переименования",
    [_L_MAIN_RETURN] = "[Назад]",
    [_L_RANDOM_MODE_MANUAL] = "Ручная генерация UUID",
    [_L_RANDOM_MODE_AUTO] = "Автогенерация UUID",
    [_L_SEQUENCE_MODE] = "Поочерёдно",
    [_L_READ_WRITE_MODE] = "Чтение-запись",
    [_L_AMIIBOLINK_V1] = "V1",
    [_L_AMIIBOLINK_V2] = "V2",
    [_L_AMILOOP] = "AmiLoop",
    [_L_MODE] = "Режим",
    [_L_AUTO_RANDOM] = "Автогенерация",
    [_L_COMPATIBLE_MODE] = "Совместимость",
    [_L_TAG_DETAILS] = "[Назад к деталям]",
    [_L_MAIN_MENU] = "[В главное меню]",
    [_L_MODE_RANDOM] = "Ручная генерация",
    [_L_MODE_CYCLE] = "Поочерёдно",
    [_L_MODE_NTAG] = "Чтение-запись",
    [_L_MODE_RANDOM_AUTO_GEN] = "Автогенерация",
    [_L_BLANK_TAG] = "Пустой тег",
    [_L_APP_AMIIDB] = "База Amiibo",
    [_L_APP_AMMIDB_BROWSER] = "Обозреватель...",
    [_L_APP_AMIIDB_SEARCH] = "Поиск...",
    [_L_APP_AMIIDB_MY_FAVORITES] = "Моё избранное...",
    [_L_APP_AMIIDB_MY_TAGS] = "Мои Amiibo...",
    [_L_APP_AMIIDB_SETTINGS] = "Настройки...",
    [_L_APP_AMIIDB_EXIT] = "[Выход]",
    [_L_APP_AMIIDB_BACK] = "[Назад]",
    [_L_APP_AMIIDB_SETTINGS_AMIIBO_KEY] = "Ключ",
    [_L_APP_AMIIDB_SETTINGS_AMIIBO_KEY_LOADED] = "Загружен",
    [_L_APP_AMIIDB_SETTINGS_AMIIBO_KEY_NOT_LOADED] = "Отсутствует",
    [_L_APP_AMIIDB_SETTINGS_SLOT_NUM] = "Число ячеек",
    [_L_APP_AMIIDB_DETAIL_FAVORITE] = "В избранное...",
    [_L_APP_AMIIDB_DETAIL_SAVE_AS] = "Сохранить как...",
    [_L_APP_AMIIDB_DETAIL_BACK_DETAIL] = "[Назад к деталям]",
    [_L_APP_AMIIDB_DETAIL_BACK_LIST] = "[Назад к списку]",
    [_L_APP_AMIIDB_SEARCH_HEAD] = "Поиск:",
    [_L_APP_AMIIDB_MORE] = "[Дальше...]",
    [_L_APP_AMIIDB_MORE_MESSAGE] = "Очень много совпадений.\nУточните запрос.",
    [_L_APP_AMIIDB_EMPTY_TAG] = "<пустой тег>",
    [_L_APP_AMIIDB_SLOT_DELETE] = "Сброс...",
    [_L_APP_AMIIDB_CONFIRM] = "Да",
    [_L_APP_AMIIDB_CANCEL] = "Отмена",
    [_L_APP_AMIIDB_TIPS] = "Внимание",
    [_L_APP_AMIIDB_NEW] = "Новая папка...",
    [_L_APP_AMIIDB_EMPTY] = "Очистить...",
    [_L_APP_AMIIDB_DELETE] = "Удалить...",
    [_L_APP_AMIIDB_FAV_NEW_HEAD] = "Новая папка избранного:",
    [_L_APP_AMIIDB_FAV_EMPTY_MSG] = "Выполнить удаление\n избранного?",
    [_L_APP_AMIIDB_FAV_DELETE_MSG] = "Выполнить удаление?",
    [_L_APP_AMIIDB_FAV_SELECT_FOLDER] = "Выбрать папку избранного...",
    [_L_APP_AMIIDB_FAV_SUCCESS] = "Добавлено",
    [_L_APP_AMIIDB_FAV_FAILED] = "Ошибка добавления",
    [_L_APP_AMIIDB_SLOT_SAVE_SUCCESS] = "Сохранено",
    [_L_APP_AMIIDB_SLOT_SAVE_FAILED] = "Ошибка сохранения",
    [_L_APP_AMIIDB_SORT_FIELD] = "Сортировка",
    [_L_APP_AMIIDB_SORT_DEFAULT] = "По умолчанию",
    [_L_APP_AMIIDB_SORT_NAME] = "По алфавиту",
    [_L_APP_AMIIDB_NOT_SUPPORT_V3] = "Amiibo версии 3\n не поддерживаются!",
    [_L_APP_CHAMELEON] = "Эмулятор карт",
    [_L_APP_CHAMELEON_TAG_MF1_WRITE_NORMAL] = "Разрешена",
    [_L_APP_CHAMELEON_TAG_MF1_WRITE_DENIED] = "Запрещена",
    [_L_APP_CHAMELEON_TAG_MF1_WRITE_DECEIVE] = "Игнорируется",
    [_L_APP_CHAMELEON_TAG_MF1_WRITE_SHADOW] = "В кэш",
    [_L_APP_CHAMELEON_INITIALIZING] = "Инициализация...",
    [_L_APP_CHAMELEON_CARD_SLOT] = "Ячейка",
    [_L_APP_CHAMELEON_CARD_NICK] = "Название",
    [_L_APP_CHAMELEON_CARD_ID] = "ID",
    [_L_APP_CHAMELEON_CARD_TYPE] = "Тип",
    [_L_APP_CHAMELEON_CARD_DATA] = "Данные...",
    [_L_APP_CHAMELEON_CARD_ADVANCED] = "Дополнительно...",
    [_L_APP_CHAMELEON_CARD_SLOT_SETTINGS] = "Управление ячейками...",
    [_L_APP_CHAMELEON_CARD_SLOT_NUM] = "Число ячеек...",
    [_L_APP_CHAMELEON_CARD_SET_NICK_SUCCESS] = "Название задано",
    [_L_APP_CHAMELEON_CARD_SET_NICK_FAILED] = "Недопустимое название",
    [_L_APP_CHAMELEON_CARD_INPUT_NICK] = "Задайте название карты:",
    [_L_APP_CHAMELEON_CARD_DATA_LOAD] = "Загрузка...",
    [_L_APP_CHAMELEON_CARD_DATA_SAVE] = "Сохранение...",
    [_L_APP_CHAMELEON_CARD_DATA_FACTORY] = "Сброс...",
    [_L_APP_CHAMELEON_CARD_DATA_FACTORY_SUCCESS] = "Данные сброшены",
    [_L_APP_CHAMELEON_CARD_DATA_LOAD_NOT_FOUND] = "Файл не обнаружен",
    [_L_APP_CHAMELEON_CARD_DATA_LOAD_SIZE_NOT_MATCH] = "Файл несоразмерен",
    [_L_APP_CHAMELEON_CARD_DATA_LOAD_FAILED] = "Ошибка загрузки файла",
    [_L_APP_CHAMELEON_CARD_DATA_LOAD_SUCCESS] = "Данные загружены",
    [_L_APP_CHAMELEON_CARD_DATA_SAVE_INPUT_FILE_NAME] = "Задайте имя файла:",
    [_L_APP_CHAMELEON_CARD_DATA_SAVE_FAILED] = "Ошибка сохранения файла",
    [_L_APP_CHAMELEON_CARD_DATA_SAVE_SUCCESS] = "Данные сохранены",
    [_L_APP_CHAMELEON_CARD_ADV_CUSTOM_MODE] = "Заказной режим",
    [_L_APP_CHAMELEON_CARD_ADV_LOAD_BLOCK0] = "Загрузить из блока 0...",
    [_L_APP_CHAMELEON_CARD_ADV_LOAD_BLOCK0_SUCCESS] = "Данные из блока 0\n загружены",
    [_L_APP_CHAMELEON_CARD_ID_SIZE] = "Размер ID",
    [_L_APP_CHAMELEON_CARD_GEN1A_MODE] = "Gen1A",
    [_L_APP_CHAMELEON_CARD_GENERATE_UID] = "Сгенерировать UID",
    [_L_APP_CHAMELEON_CARD_GENERATE_UID_SUCCESS] = "UID сгенерирован",
    [_L_APP_CHAMELEON_CARD_GEN2_MODE] = "Gen2",
    [_L_APP_CHAMELEON_CARD_WRITE_MODE] = "Запись",
    [_L_APP_CHAMELEON_CARD_ADV_ID_EDIT_INVALID_INPUT] = "Недопустимый ввод",
    [_L_APP_CHAMELEON_CARD_TYPE_FACTORY_DATA_CONFRIM] = "Тип карты изменён.\nСбросить данные карты?",
    [_L_APP_CHAMELEON_CARD_DEFAULT_CARD] = "По умолчанию",
    [_L_APP_GAME] = "Игры",
    [_L_APP_GAME_TINY_ARKANOID] = "Арканоид",
    [_L_APP_GAME_TINY_INVADERS] = "Космические захватчики",
    [_L_APP_GAME_TINY_LANDER] = "Посадка на Луну",
    [_L_APP_GAME_TINY_TRIS] = "Тетрис",
};
