solosky/pixl.js/fw/application/src/i18n/sv_SE.c

#include "string_id.h"
const char * const lang_sv_SE[_L_COUNT] = {
    [_L_ON] = "PÅ",
    [_L_OFF] = "AV",
    [_L_ON_F] = "[PÅ]",
    [_L_OFF_F] = "[AV]",
    [_L_BACK] = "Tillbaka",
    [_L_ERR] = "Fel",
    [_L_ERR_CODE] = "Felkod",
    [_L_FAILED] = "Misslyckades",
    [_L_BYTES] = "",
    [_L_APP_AMIIBO] = "Amiibo-emulator",
    [_L_APP_AMIIBOLINK] = "AmiiboLink",
    [_L_APP_BLE] = "BLE Filöverföring",
    [_L_APP_BLE_TITLE] = "BLE Filöverföring",
    [_L_APP_PLAYER] = "Videospelare",
    [_L_APP_SET] = "Inställningar",
    [_L_APP_SET_VERSION] = "Version",
    [_L_APP_SET_STORAGE_USED] = "Använt",
    [_L_APP_SET_STORAGE] = "Extern lagring",
    [_L_APP_SET_OLED_CONTRAST] = "Kontrast",
    [_L_APP_SET_OLED_CONTRAST_TITLE] = "Kontrast",
    [_L_APP_SET_LCD_BACKLIGHT] = "Bakgrundsljus",
    [_L_APP_SET_LCD_BACKLIGHT_TITLE] = "Ljusstyrka",
    [_L_APP_SET_ANIM] = "Menyanimation",
    [_L_APP_SET_LIPO_BAT] = "LiPO-batteri",
    [_L_APP_SET_SHOW_MEM_USAGE] = "Använt minne",
    [_L_APP_SET_HIBERNATE] = "Snabb väckning",
    [_L_APP_SET_SLEEP_TIMEOUT] = "Timeout för viloläge",
    [_L_APP_SET_LANGUAGE] = "Språk",
    [_L_APP_SET_GO_SLEEP] = "Viloläge",
    [_L_APP_SET_DFU] = "Firmware-uppdatering",
    [_L_APP_SET_REBOOT] = "Starta om",
    [_L_APP_SET_RESET_DEFAULT] = "Fabriksinställningar",
    [_L_APP_SET_RESET_DEFAULT_SUCCESS] = "Återställning lyckad!",
    [_L_APP_SET_RESET_DEFAULT_CONFIRM] = "Bekräfta återställning av inställningar?",
    [_L_APP_SET_ABOUT] = "Om enheten",
    [_L_APP_SET_ABOUT_OPEN_SOURCE_PROJECT] = "Projekt med öppen källkod",
    [_L_APP_SET_ABOUT_LGPL_LICENSE] = "GPL 2.0-licens",
    [_L_APP_SET_APP_MGMT] = "",
    [_L_15S] = "15 sekunder",
    [_L_30S] = "30 sekunder",
    [_L_45S] = "45 sekunder",
    [_L_1MIN] = "1 minut",
    [_L_2MIN] = "2 minuter",
    [_L_3MIN] = "3 minuter",
    [_L_AMIIBO_KEY_UNLOADED] = "Amiibo-nyckel inte laddad",
    [_L_UPLOAD_KEY_RETAIL_BIN] = "Ladda upp filen key_retail.bin\ntill lagringens rotkatalog.",
    [_L_KNOW] = "Uppfattat",
    [_L_RANDOM_GENERATION] = "Slumpa tagg",
    [_L_AUTO_RANDOM_GENERATION] = "Auto-slump",
    [_L_SET_CUSTOM_ID] = "Ange anpassat ID",
    [_L_INPUT_ID] = "Input ID",
    [_L_INAVLID_ID] = "Ogiltigt ID",
    [_L_SHOW_QRCODE] = "Visa QR-kod",
    [_L_READ_ONLY] = "Skrivskyddad",
    [_L_DELETE_TAG] = "Radera tagg",
    [_L_DELETE_TAG_CONFIRM] = "Bekräfta ta bort %s?",
    [_L_BACK_TO_DETAILS] = "Tillbaka till taggdetaljer",
    [_L_BACK_TO_FILE_LIST] = "Tillbaka till listan",
    [_L_BACK_TO_MAIN_MENU] = "Tillbaka till huvudmenyn",
    [_L_FORMAT] = "Formatera",
    [_L_FORMAT_STORAGE] = "Formatera lagring",
    [_L_DELETE_ALL_DATA] = "Detta tar bort alla data. Bekräfta formatering?",
    [_L_DELETING_MESSAGE] = "Formaterar ...",
    [_L_MESSAGE] = "Meddelande",
    [_L_CONFIRM] = "Bekräfta",
    [_L_CANCEL] = "Avbryt",
    [_L_BACK_TO_LIST] = "Tillbaka till listan",
    [_L_NOT_MOUNTED] = "Inte laddad",
    [_L_MOUNTED_LFS] = "===Laddad[LFS]===",
    [_L_MOUNTED_FFS] = "===Laddad[FFS]===",
    [_L_TOTAL_SPACE] = "Totalt",
    [_L_AVAILABLE_SPACE] = "Ledigt",
    [_L_NOT_AMIIBO_FILE] = "Detta är inte en Amiibo-fil",
    [_L_READ_FILE_FAILED] = "Kunde inte läsa filen",
    [_L_INPUT_FOLDER_NAME] = "Mappens namn:",
    [_L_INPUT_AMIIBO_NAME] = "Ange namn på Amiibo:",
    [_L_DELETE_FILE] = "Ta bort %s ?",
    [_L_DELETE] = "Radera...",
    [_L_TIPS] = "Bekräfta",
    [_L_INPUT_NEW_NAME] = "Ange nytt namn:",
    [_L_INVALID_INPUT] = "Ogiltig inmatning",
    [_L_CREATE_NEW_FOLDER] = "Skapa ny mapp...",
    [_L_CREATE_NEW_TAG] = "Skapa ny tagg...",
    [_L_CREATE_NEW_TAG_BATCH] = "Batchskapa ny tagg...",
    [_L_INPUT_TAG_NUM] = "Ange taggnummer:",
    [_L_CREATE_TOO_MANY_NUM] = "Endast max %d taggar skapas i en batch.",
    [_L_CREATING_TAG_BATCH] = "Skapar tagg",
    [_L_CREATING_TAG_FAILED] = "Skapa taggen %s misslyckades!",
    [_L_RENAME] = "Byt namn...",
    [_L_OPEN_FOLDER_FAILED] = "Kunde inte öppna mapp",
    [_L_RENAME_FAILED] = "Kunde inte byta namn\nFelkod",
    [_L_MAIN_RETURN] = "[TILLBAKA]",
    [_L_RANDOM_MODE_MANUAL] = "Slump (Manuell)",
    [_L_RANDOM_MODE_AUTO] = "Slump (Auto)",
    [_L_SEQUENCE_MODE] = "Sekventiellt läge",
    [_L_READ_WRITE_MODE] = "Läs-skriv-läge",
    [_L_AMIIBOLINK_V1] = "V1",
    [_L_AMIIBOLINK_V2] = "V2",
    [_L_AMILOOP] = "AmiLoop",
    [_L_MODE] = "Läge",
    [_L_AUTO_RANDOM] = "Auto-slump",
    [_L_COMPATIBLE_MODE] = "Kompatibelläge",
    [_L_TAG_DETAILS] = "[Taggdetaljer]",
    [_L_MAIN_MENU] = "[Huvudmeny]",
    [_L_MODE_RANDOM] = "Slump (Manuell)",
    [_L_MODE_CYCLE] = "Sekventiell",
    [_L_MODE_NTAG] = "Läs/Skriv",
    [_L_MODE_RANDOM_AUTO_GEN] = "Slump (auto)",
    [_L_BLANK_TAG] = "Blank NFC-tagg",
    [_L_APP_AMIIDB] = "Amiibo-databas",
    [_L_APP_AMMIDB_BROWSER] = "Browser...",
    [_L_APP_AMIIDB_SEARCH] = "Sök...",
    [_L_APP_AMIIDB_MY_FAVORITES] = "Mina favoriter...",
    [_L_APP_AMIIDB_MY_TAGS] = "Mina Amiibos...",
    [_L_APP_AMIIDB_SETTINGS] = "Inställningar...",
    [_L_APP_AMIIDB_EXIT] = "[Avsluta]",
    [_L_APP_AMIIDB_BACK] = "[Tillbaka]",
    [_L_APP_AMIIDB_SETTINGS_AMIIBO_KEY] = "Nycklar",
    [_L_APP_AMIIDB_SETTINGS_AMIIBO_KEY_LOADED] = "Laddat",
    [_L_APP_AMIIDB_SETTINGS_AMIIBO_KEY_NOT_LOADED] = "INTE laddat",
    [_L_APP_AMIIDB_SETTINGS_SLOT_NUM] = "Plats nr",
    [_L_APP_AMIIDB_DETAIL_FAVORITE] = "Favorit...",
    [_L_APP_AMIIDB_DETAIL_SAVE_AS] = "Spara som...",
    [_L_APP_AMIIDB_DETAIL_BACK_DETAIL] = "[Tillbaka till detaljer]",
    [_L_APP_AMIIDB_DETAIL_BACK_LIST] = "[Tillbaka till listan]",
    [_L_APP_AMIIDB_SEARCH_HEAD] = "Sök:",
    [_L_APP_AMIIDB_MORE] = "[Mer...]",
    [_L_APP_AMIIDB_MORE_MESSAGE] = "För många resultat. Försök med en mer specifik sökning.",
    [_L_APP_AMIIDB_EMPTY_TAG] = "<Blank Amiibo>",
    [_L_APP_AMIIDB_SLOT_DELETE] = "Återställ...",
    [_L_APP_AMIIDB_CONFIRM] = "Bekräfta",
    [_L_APP_AMIIDB_CANCEL] = "Avbryt",
    [_L_APP_AMIIDB_TIPS] = "Bekräfta",
    [_L_APP_AMIIDB_NEW] = "Ny...",
    [_L_APP_AMIIDB_EMPTY] = "Tom...",
    [_L_APP_AMIIDB_DELETE] = "Radera...",
    [_L_APP_AMIIDB_FAV_NEW_HEAD] = "Ny favoritmapp:",
    [_L_APP_AMIIDB_FAV_EMPTY_MSG] = "Töm favoritmapp?",
    [_L_APP_AMIIDB_FAV_DELETE_MSG] = "Bekräfta Ta bort?",
    [_L_APP_AMIIDB_FAV_SELECT_FOLDER] = "Välj favoritmapp...",
    [_L_APP_AMIIDB_FAV_SUCCESS] = "Favoriten lyckades",
    [_L_APP_AMIIDB_FAV_FAILED] = "Favorit misslyckades!",
    [_L_APP_AMIIDB_SLOT_SAVE_SUCCESS] = "Sparades",
    [_L_APP_AMIIDB_SLOT_SAVE_FAILED] = "Spara misslyckades!",
    [_L_APP_AMIIDB_SORT_FIELD] = "Sorteringsfält",
    [_L_APP_AMIIDB_SORT_DEFAULT] = "Standard",
    [_L_APP_AMIIDB_SORT_NAME] = "Namn",
    [_L_APP_AMIIDB_NOT_SUPPORT_V3] = "",
    [_L_APP_CHAMELEON] = "Kort-emulator",
    [_L_APP_CHAMELEON_TAG_MF1_WRITE_NORMAL] = "Normal",
    [_L_APP_CHAMELEON_TAG_MF1_WRITE_DENIED] = "Neka",
    [_L_APP_CHAMELEON_TAG_MF1_WRITE_DECEIVE] = "Ignorera",
    [_L_APP_CHAMELEON_TAG_MF1_WRITE_SHADOW] = "Cache",
    [_L_APP_CHAMELEON_INITIALIZING] = "Initierar data ...",
    [_L_APP_CHAMELEON_CARD_SLOT] = "Plats",
    [_L_APP_CHAMELEON_CARD_NICK] = "Smeknamn",
    [_L_APP_CHAMELEON_CARD_ID] = "ID",
    [_L_APP_CHAMELEON_CARD_TYPE] = "Typ",
    [_L_APP_CHAMELEON_CARD_DATA] = "Data...",
    [_L_APP_CHAMELEON_CARD_ADVANCED] = "Avancerat...",
    [_L_APP_CHAMELEON_CARD_SLOT_SETTINGS] = "Platsinställning...",
    [_L_APP_CHAMELEON_CARD_SLOT_NUM] = "Plats nr...",
    [_L_APP_CHAMELEON_CARD_SET_NICK_SUCCESS] = "Smeknamn sattes",
    [_L_APP_CHAMELEON_CARD_SET_NICK_FAILED] = "Smeknamn misslyckades!",
    [_L_APP_CHAMELEON_CARD_INPUT_NICK] = "Ange smeknamn:",
    [_L_APP_CHAMELEON_CARD_DATA_LOAD] = "Ladda...",
    [_L_APP_CHAMELEON_CARD_DATA_SAVE] = "Spara...",
    [_L_APP_CHAMELEON_CARD_DATA_FACTORY] = "Återställ...",
    [_L_APP_CHAMELEON_CARD_DATA_FACTORY_SUCCESS] = "Återställning lyckades",
    [_L_APP_CHAMELEON_CARD_DATA_LOAD_NOT_FOUND] = "Filen hittades inte",
    [_L_APP_CHAMELEON_CARD_DATA_LOAD_SIZE_NOT_MATCH] = "Filstorlek matchar inte",
    [_L_APP_CHAMELEON_CARD_DATA_LOAD_FAILED] = "Laddning misslyckades",
    [_L_APP_CHAMELEON_CARD_DATA_LOAD_SUCCESS] = "Laddning lyckades",
    [_L_APP_CHAMELEON_CARD_DATA_SAVE_INPUT_FILE_NAME] = "Ange filnamn:",
    [_L_APP_CHAMELEON_CARD_DATA_SAVE_FAILED] = "Spara misslyckades!",
    [_L_APP_CHAMELEON_CARD_DATA_SAVE_SUCCESS] = "Sparades",
    [_L_APP_CHAMELEON_CARD_ADV_CUSTOM_MODE] = "Anpassat läge",
    [_L_APP_CHAMELEON_CARD_ADV_LOAD_BLOCK0] = "Ladda från Block0...",
    [_L_APP_CHAMELEON_CARD_ADV_LOAD_BLOCK0_SUCCESS] = "Ladda block0 lyckades",
    [_L_APP_CHAMELEON_CARD_ID_SIZE] = "ID-storlek",
    [_L_APP_CHAMELEON_CARD_GEN1A_MODE] = "Gen1A aktiverad",
    [_L_APP_CHAMELEON_CARD_GENERATE_UID] = "Slump UID",
    [_L_APP_CHAMELEON_CARD_GENERATE_UID_SUCCESS] = "UID skapat",
    [_L_APP_CHAMELEON_CARD_GEN2_MODE] = "Gen2 aktiverad",
    [_L_APP_CHAMELEON_CARD_WRITE_MODE] = "Skrivläge",
    [_L_APP_CHAMELEON_CARD_ADV_ID_EDIT_INVALID_INPUT] = "Ogiltig inmatning!",
    [_L_APP_CHAMELEON_CARD_TYPE_FACTORY_DATA_CONFRIM] = "Korttypen har ändrats. \nfabriksåterställ kortdata?",
    [_L_APP_CHAMELEON_CARD_DEFAULT_CARD] = "Standardkort",
    [_L_APP_GAME] = "Spel",
    [_L_APP_GAME_TINY_ARKANOID] = "",
    [_L_APP_GAME_TINY_INVADERS] = "",
    [_L_APP_GAME_TINY_LANDER] = "",
    [_L_APP_GAME_TINY_TRIS] = "",
};
