solosky/pixl.js/fw/application/src/mod/ble/ble_amiibolink.c

#include "ble_amiibolink.h"
#include "ble_main.h"
#include "df_buffer.h"
#include "nrf_log.h"
#include "ntag_def.h"
#include "ntag_emu.h"

#include "nrf_crypto.h"
#include "nrf_crypto_aes.h"
#include "utils2.h"

static ntag_t m_ntag = {0};
uint32_t m_data_pos = 0;
uint32_t index = 0;
ble_amiibolink_event_handler_t m_event_handler = {0};
void *m_event_ctx = {0};
uint8_t m_key1 = 0;
uint8_t m_key2 = 0;
ble_amiibolink_ver_t m_ver = BLE_AMIIBOLINK_VER_V2;
ble_amiibolink_mode_t  m_mode = BLE_AMIIBOLINK_MODE_RANDOM;


void ble_amiibolink_set_event_handler(ble_amiibolink_event_handler_t handler, void *ctx) {
    m_event_handler = handler;
    m_event_ctx = ctx;
}


void ble_amiibolink_set_version(ble_amiibolink_ver_t ver){
    m_ver = ver;
}

void ble_amiibolink_set_mode(ble_amiibolink_mode_t mode){
    m_mode = mode;
}


void pad16(uint16_t data, uint8_t buf[16]) {
    memset(buf, 0, 16);
    memcpy(buf, &data, sizeof(uint16_t));
}



void ble_amiibolink_send_cmd_v1(uint16_t cmd){
    ble_nus_tx_data(&cmd, 2);
}

void ble_amiibolink_send_cmd_v2(uint16_t cmd) {
    link_data_t link_data = {0};
    link_data.key1 = m_key1;
    link_data.key2 = m_key2;
    link_data.data_len = 16;
    link_data.de_data_len = 2;

    uint8_t pad[16] = {0};
    pad16(cmd, pad);

    uint8_t key[] = {
        0x4B, 0x47, 0x46, 0x5F, 0x41, 0x4D, 0x49,
        0x4C, 0x07, 0xE7, 0x04, 0x06, 0x0A, 0x2A,
        link_data.key1, link_data.key2 // 随机密钥
    };

    nrf_crypto_aes_context_t aes_ecb_ctx;
    size_t out_len = 16;
    ret_code_t err = nrf_crypto_aes_crypt(
        &aes_ecb_ctx,
        &g_nrf_crypto_aes_ecb_128_info,
        NRF_CRYPTO_ENCRYPT,
        &key,
        NULL,
        pad,
        16,
        link_data.data,
        &out_len
    );
    NRF_LOG_INFO("nrf_crypto_aes_encrypt:out_len=%d err=%d msg=%s", out_len, err, nrf_crypto_error_string_get(err));

    ble_nus_tx_data(&link_data, sizeof(link_data_t));
}


void ble_amiibolink_send_data_v2(uint8_t* data, size_t data_len) {
    link_data_t link_data = {0};
    link_data.key1 = m_key1;
    link_data.key2 = m_key2;

    //NRF_LOG_INFO("send data v2: data_len=%d", data_len);
    //NRF_LOG_HEXDUMP_INFO(data, data_len);

    uint8_t in_buffer[32];
    memset(in_buffer, 0, sizeof(in_buffer));
    memcpy(in_buffer, data, data_len);
    size_t in_buffer_size = sizeof(in_buffer);


    uint8_t key[] = {
        0x4B, 0x47, 0x46, 0x5F, 0x41, 0x4D, 0x49,
        0x4C, 0x07, 0xE7, 0x04, 0x06, 0x0A, 0x2A,
        link_data.key1, link_data.key2 // 随机密钥
    };

    nrf_crypto_aes_context_t aes_ecb_ctx;
    size_t out_len = sizeof(link_data.data);
    ret_code_t err = nrf_crypto_aes_crypt(
        &aes_ecb_ctx,
        &g_nrf_crypto_aes_ecb_128_info,
        NRF_CRYPTO_ENCRYPT,
        &key,
        NULL,
        in_buffer,
        in_buffer_size,
        link_data.data,
        &out_len
    );
    NRF_LOG_INFO("nrf_crypto_aes_encrypt:out_len=%d err=%d msg=%s", out_len, err, nrf_crypto_error_string_get(err));
    link_data.data_len = out_len;
    link_data.de_data_len = data_len;

    //NRF_LOG_HEXDUMP_INFO(&link_data, sizeof(link_data_t));

    ble_nus_tx_data(&link_data, sizeof(link_data_t));
}

void ble_amiibolink_send_cmd(uint16_t cmd) {
    if (m_ver == BLE_AMIIBOLINK_VER_V1) {
        ble_amiibolink_send_cmd_v1(cmd);
    } else {
        ble_amiibolink_send_cmd_v2(cmd);
    }
}

void ble_amiibolink_send_data(uint8_t *data, uint16_t data_len) {
    if (m_ver == BLE_AMIIBOLINK_VER_V1) {
        ble_nus_tx_data(data, data_len);
    } else {
        ble_amiibolink_send_data_v2(data, data_len);
    }
}

void ble_amiibolink_write_ntag(buffer_t *buffer) {
    buff_get_u8(buffer); // 00
    uint8_t size = buff_get_u8(buffer);
    void *data_ptr = buff_get_data_ptr_pos(buffer);
    memcpy(m_ntag.data + m_data_pos, data_ptr, size);
    m_data_pos += size;
}

void ble_amiibolink_init(void) {}

void ble_amiibolink_process_cmd(buffer_t* buffer){

    ble_amiibolink_mode_t mode;
    uint16_t cmd = buff_get_u16(buffer);

    NEW_BUFFER_LOCAL(out_buffer, MAX_MTU_DAT_SIZE);
    uint8_t device_id[8];

    switch (cmd) {

    case 0xB2A2: // get version
        buff_put_u16(&out_buffer, 0xA2B2);
        buff_put_string_u8(&out_buffer, m_ver == BLE_AMIIBOLINK_VER_V1 ? "0.0.4" : "1.2.1.33");
        buff_put_u8(&out_buffer, 1);
        buff_put_u8(&out_buffer, m_mode); //device mode
        buff_put_u8(&out_buffer, 4);
        utils_get_device_id(device_id);
        buff_put_byte_array(&out_buffer, device_id, 4);
        buff_put_u8(&out_buffer, 0);

        ble_amiibolink_send_data(buff_get_data(&out_buffer), buff_get_size(&out_buffer));
        break;


    case 0xB1A1: // send model code ??
        // a1 b1 01
        // 01: 随机模式 02: 按序模式 03:读写模式
        mode = (ble_amiibolink_mode_t)buff_get_u8(buffer);
        if (m_event_handler) {
            m_event_handler(m_event_ctx, BLE_AMIIBOLINK_EVENT_SET_MODE, &mode, sizeof(ble_amiibolink_mode_t));
        }
        ble_amiibolink_send_cmd(0xA1B1);
        break;

    case 0xB0A0: // seq 1
        ble_amiibolink_send_cmd(0xA0B0);
        break;

    case 0xACAC: // seq 2
        // ac ac 00 04 00 00 02 1c //540
        m_data_pos = 0;
        ble_amiibolink_send_cmd(0xCACA);
        break;

    case 0xABAB: // seq 3
        // ab ab 02 1c
        ble_amiibolink_send_cmd(0xBABA);
        break;

    case 0xAADD: // seq 4
        ble_amiibolink_write_ntag(buffer);
        ble_amiibolink_send_cmd(0xDDAA);
        break;

    case 0xBCBC: // seq 5
        ble_amiibolink_send_cmd(0xCBCB);
        break;

    case 0xDDCC: // seq 6
        NRF_LOG_INFO("ntag_emu_set_tag");
        ntag_emu_set_tag(&m_ntag);
        if (m_event_handler) {
            m_event_handler(m_event_ctx, BLE_AMIIBOLINK_EVENT_TAG_UPDATED, &m_ntag, sizeof(m_ntag));
        }
        ble_amiibolink_send_cmd(0xCCDD);
        break;
    }
}


void ble_amiibolink_received_data_v1(const uint8_t *data, size_t length){
    NEW_BUFFER_READ(buffer, (void *)data, length);
    ble_amiibolink_process_cmd(&buffer);
}


void ble_amiibolink_received_data_v2(const uint8_t *data, size_t length) {
    NRF_LOG_INFO("ble data received %d bytes", length);
    //NRF_LOG_HEXDUMP_INFO(data, length);

    if (length < 16) {
        NEW_BUFFER_READ(buffer, data, length);
        NRF_LOG_WARNING("data length is too short, v1 protocol ?");
        ble_amiibolink_process_cmd(&buffer);
        return;
    }

    //  13   45     10       02     76 98 8D 3D.....
    // key1 key2 datalen dedatalen data
    link_data_t *link_data = (link_data_t *) data;

    nrf_crypto_aes_context_t aes_ecb_ctx;

    uint8_t buf[MAX_MTU_DAT_SIZE];
    size_t out_len = sizeof(buf);
    size_t data_len = link_data->de_data_len;

    uint8_t key[] = {
        0x4B, 0x47, 0x46, 0x5F, 0x41, 0x4D, 0x49,
        0x4C, 0x07, 0xE7, 0x04, 0x06, 0x0A, 0x2A,
        link_data->key1, link_data->key2 // 随机密钥
    };

    m_key1 = link_data->key1;
    m_key2 = link_data->key2;

    ret_code_t err = nrf_crypto_aes_crypt(
        &aes_ecb_ctx,
        &g_nrf_crypto_aes_ecb_128_info,
        NRF_CRYPTO_DECRYPT,
        &key,
        NULL,
        link_data->data,
        link_data->data_len,
        buf,
        &out_len
    );

    NRF_LOG_INFO("decrypted data len: de_data_len=%d, decrypted_len=%d", link_data->de_data_len, out_len);
    NRF_LOG_INFO("nrf_crypto_aes_decrypt: %d %s", err, nrf_crypto_error_string_get(err));

    NRF_LOG_HEXDUMP_DEBUG(&buf, data_len);
    NEW_BUFFER_READ(buffer, (void *)&buf, data_len);
    ble_amiibolink_process_cmd(&buffer);
}

uint8_t get_xor(const uint8_t *data, size_t length) {
    uint8_t xor = 0;
    for (int i = 0; i < length; i++) {
        xor ^= data[i];
    }
    return xor & 255;
}

void amiloop_send_data(buffer_t *buf) {
    NEW_BUFFER_LOCAL(buffer, MAX_MTU_DAT_SIZE);
    buff_put_u8(&buffer, 0x02); // magic
    buff_put_u8(&buffer, buff_get_size(buf)); // len
    buff_put_byte_array(&buffer, buff_get_data(buf), buff_get_size(buf)); // data
    buff_put_u8(&buffer, get_xor(buff_get_data(&buffer) + 1, buff_get_size(&buffer) - 1)); // xor
    buff_put_u8(&buffer, 0x03); // magic end
    NRF_LOG_HEXDUMP_DEBUG(buff_get_data(&buffer), buff_get_size(&buffer));
    ble_nus_tx_data(buff_get_data(&buffer), buff_get_size(&buffer));
}

void ble_amiloop_received_data(const uint8_t *m_data, size_t length) {
    NRF_LOG_INFO("ble data received %d bytes", length);
    NEW_BUFFER_READ(buffer, (void *)m_data, length);
    NEW_BUFFER_LOCAL(output, MAX_MTU_DAT_SIZE);
    uint8_t magic = buff_get_u8(&buffer);
    if (magic != 0x02) {
        NRF_LOG_WARNING("amiloop magic error: %02x", magic);
        return;
    }
    uint8_t len = buff_get_u8(&buffer);
    NRF_LOG_INFO("amiloop len: %02x", len);
    uint8_t flag = buff_get_u8(&buffer);
    NRF_LOG_INFO("amiloop flag: %02x", flag);
    switch (flag)
    {
    case 0x87: { // WRITE_ALL
        uint8_t is_end = buff_get_u8(&buffer);
        NRF_LOG_INFO("amiloop is_end: %02x", is_end);
        uint8_t idx = buff_get_u8(&buffer);
        NRF_LOG_INFO("amiloop idx: %02x", idx);
        uint8_t data[len - 3];
        buff_get_byte_array(&buffer, data, len - 3);
        uint8_t xor = buff_get_u8(&buffer);

        if (xor != get_xor(m_data + 1, length - 3)) {
            NRF_LOG_WARNING("amiloop xor error: %02x", xor);
            buff_put_u8(&output, 0x01);
            amiloop_send_data(&output);
            return;
        }

        if (index < idx) {
            index = idx;
        } else {
            index = 0;
            m_data_pos = 0;
        }
        memcpy(m_ntag.data + m_data_pos, data, len - 3);
        m_data_pos += len - 3;

        if (is_end == 1) {
            ntag_emu_set_tag(&m_ntag);
            if (m_event_handler) {
                m_event_handler(m_event_ctx, BLE_AMIIBOLINK_EVENT_TAG_UPDATED, &m_ntag, sizeof(m_ntag));
            }
        }
        buff_put_u8(&output, 0x00);
        amiloop_send_data(&output);
        break;
    }

    case 0x89: // GET_VERSION
        // AmiLoop_FW_V 检测是否为 AmiLoop 固件
        // V1.0.0 不显示模式设置
        buff_put_string(&output, "AmiLoop_FW_V1.0.7");
        amiloop_send_data(&output);
        break;
    
    case 0x8A: {// SET_MODE
        // 0x00 随机模式
        // 0x01 顺序模式
        // 0x02 读写模式
        uint8_t mode = buff_get_u8(&buffer);
        NRF_LOG_INFO("amiloop mode: %d", mode);
        ble_amiibolink_mode_t link_mode;
        switch (mode)
        {
        case 0x00:
            link_mode = BLE_AMIIBOLINK_MODE_RANDOM;
            NRF_LOG_INFO("amiloop mode: random");
            break;
        
        case 0x01:
            link_mode = BLE_AMIIBOLINK_MODE_CYCLE;
            NRF_LOG_INFO("amiloop mode: cycle");
            break;

        case 0x02:
            link_mode = BLE_AMIIBOLINK_MODE_RANDOM_AUTO_GEN;
            NRF_LOG_INFO("amiloop mode: random auto gen");
            break;

        default:
            NRF_LOG_INFO("amiloop mode error: %02x", mode);
            buff_put_u8(&output, 0x01);
            amiloop_send_data(&output);
            break;
        }
        if (m_event_handler) {
            m_event_handler(m_event_ctx, BLE_AMIIBOLINK_EVENT_SET_MODE, &link_mode, sizeof(ble_amiibolink_mode_t));
        }
        buff_put_u8(&output, 0x00);
        amiloop_send_data(&output);
        break;
    }

    case 0x8F: // RESET_SETTING
        buff_put_u8(&output, 0x00);
        amiloop_send_data(&output);
        break;

    default:
        NRF_LOG_INFO("amiloop flag error: %02x", flag);
        break;
    }
}

void ble_amiibolink_received_data(const uint8_t *data, size_t length) {
    if (m_ver == BLE_AMIIBOLINK_VER_V1) {
        ble_amiibolink_received_data_v1(data, length);
    } else if (m_ver == BLE_AMILOOP) {
        ble_amiloop_received_data(data, length);
    } else {
        ble_amiibolink_received_data_v2(data, length);
    }
}
