solosky/pixl.js/fw/application/src/i18n/ja_JP.c

#include "string_id.h"
const char * const lang_ja_JP[_L_COUNT] = {
    [_L_ON] = "オン",
    [_L_OFF] = "オフ",
    [_L_ON_F] = "[オン]",
    [_L_OFF_F] = "[オフ]",
    [_L_BACK] = "戻る",
    [_L_ERR] = "エラー",
    [_L_ERR_CODE] = "エラーコード",
    [_L_FAILED] = "",
    [_L_BYTES] = "",
    [_L_APP_AMIIBO] = "Amiiboエミュレータ",
    [_L_APP_AMIIBOLINK] = "AmiiboLink",
    [_L_APP_BLE] = "BLEファイル転送",
    [_L_APP_BLE_TITLE] = "BLEファイル転送",
    [_L_APP_PLAYER] = "ビデオプレーヤー",
    [_L_APP_SET] = "設定",
    [_L_APP_SET_VERSION] = "バージョン",
    [_L_APP_SET_STORAGE_USED] = "使用ストレージ",
    [_L_APP_SET_STORAGE] = "外部ストレージ",
    [_L_APP_SET_OLED_CONTRAST] = "コントラスト",
    [_L_APP_SET_OLED_CONTRAST_TITLE] = "コントラスト",
    [_L_APP_SET_LCD_BACKLIGHT] = "バックライト",
    [_L_APP_SET_LCD_BACKLIGHT_TITLE] = "バックライトの明るさ",
    [_L_APP_SET_ANIM] = "メニュー アニメーション",
    [_L_APP_SET_LIPO_BAT] = "LiPOバッテリー",
    [_L_APP_SET_SHOW_MEM_USAGE] = "使用メモリ",
    [_L_APP_SET_HIBERNATE] = "高速起動",
    [_L_APP_SET_SLEEP_TIMEOUT] = "スリープタイムアウト",
    [_L_APP_SET_LANGUAGE] = "言語",
    [_L_APP_SET_GO_SLEEP] = "",
    [_L_APP_SET_DFU] = "ファームウェア更新",
    [_L_APP_SET_REBOOT] = "システム再起動",
    [_L_APP_SET_RESET_DEFAULT] = "デフォルト設定に戻す",
    [_L_APP_SET_RESET_DEFAULT_SUCCESS] = "設定を初期化",
    [_L_APP_SET_RESET_DEFAULT_CONFIRM] = "",
    [_L_APP_SET_ABOUT] = "",
    [_L_APP_SET_ABOUT_OPEN_SOURCE_PROJECT] = "",
    [_L_APP_SET_ABOUT_LGPL_LICENSE] = "",
    [_L_APP_SET_APP_MGMT] = "",
    [_L_15S] = "15秒",
    [_L_30S] = "30秒",
    [_L_45S] = "45秒",
    [_L_1MIN] = "1分",
    [_L_2MIN] = "2分",
    [_L_3MIN] = "3分",
    [_L_AMIIBO_KEY_UNLOADED] = "Amiiboキーが読み込まれない",
    [_L_UPLOAD_KEY_RETAIL_BIN] = "key_retail.binファイルをストレージのルートディレクトリにアップロードする。",
    [_L_KNOW] = "了解",
    [_L_RANDOM_GENERATION] = "タグのランダム化",
    [_L_AUTO_RANDOM_GENERATION] = "自動ランダム化",
    [_L_SET_CUSTOM_ID] = "",
    [_L_INPUT_ID] = "",
    [_L_INAVLID_ID] = "",
    [_L_SHOW_QRCODE] = "QRコード表示",
    [_L_READ_ONLY] = "",
    [_L_DELETE_TAG] = "タグの削除",
    [_L_DELETE_TAG_CONFIRM] = "%s を削除しますか？",
    [_L_BACK_TO_DETAILS] = "タグの詳細に戻る",
    [_L_BACK_TO_FILE_LIST] = "ファイル一覧に戻る",
    [_L_BACK_TO_MAIN_MENU] = "メインメニューに戻る",
    [_L_FORMAT] = "フォーマット",
    [_L_FORMAT_STORAGE] = "保存領域フォーマット",
    [_L_DELETE_ALL_DATA] = "これですべてのデータが削除されます。よろしいですか？",
    [_L_DELETING_MESSAGE] = "書式設定 ...",
    [_L_MESSAGE] = "メッセージ",
    [_L_CONFIRM] = "確認",
    [_L_CANCEL] = "キャンセル",
    [_L_BACK_TO_LIST] = "バックリスト",
    [_L_NOT_MOUNTED] = "ストレージがマウントされていません",
    [_L_MOUNTED_LFS] = "===ストレージマウント[LFS]===",
    [_L_MOUNTED_FFS] = "===ストレージマウント[FFS]===",
    [_L_TOTAL_SPACE] = "トータル容量",
    [_L_AVAILABLE_SPACE] = "空き容量",
    [_L_NOT_AMIIBO_FILE] = "これはAmiiboファイルではありません",
    [_L_READ_FILE_FAILED] = "ファイルの読み込みに失敗しました",
    [_L_INPUT_FOLDER_NAME] = "入力フォルダ名:",
    [_L_INPUT_AMIIBO_NAME] = "入力Amiibo名:",
    [_L_DELETE_FILE] = "%s を削除しますか ？",
    [_L_DELETE] = "削除...",
    [_L_TIPS] = "確認する",
    [_L_INPUT_NEW_NAME] = "新しい名前を入力してください：",
    [_L_INVALID_INPUT] = "無効な入力",
    [_L_CREATE_NEW_FOLDER] = "新しいフォルダを作成...",
    [_L_CREATE_NEW_TAG] = "新規タグ作成...",
    [_L_CREATE_NEW_TAG_BATCH] = "新規タグの一括作成...",
    [_L_INPUT_TAG_NUM] = "タグ番号を入力:",
    [_L_CREATE_TOO_MANY_NUM] = "１つのバッチで作成されるタグの数はは最大 %d までです。",
    [_L_CREATING_TAG_BATCH] = "タグの作成",
    [_L_CREATING_TAG_FAILED] = "タグ %s の作成に失敗しました！",
    [_L_RENAME] = "名前の変更...",
    [_L_OPEN_FOLDER_FAILED] = "フォルダを開けませんでした",
    [_L_RENAME_FAILED] = "名前の変更に失敗しました。\nエラーコード",
    [_L_MAIN_RETURN] = "[リターン］",
    [_L_RANDOM_MODE_MANUAL] = "ランダム化 (手動)",
    [_L_RANDOM_MODE_AUTO] = "ランダム化(自動)",
    [_L_SEQUENCE_MODE] = "シーケンシャルモード",
    [_L_READ_WRITE_MODE] = "読み書きモード",
    [_L_AMIIBOLINK_V1] = "V1",
    [_L_AMIIBOLINK_V2] = "V2",
    [_L_AMILOOP] = "AmiLoop",
    [_L_MODE] = "モード",
    [_L_AUTO_RANDOM] = "自動ランダム化",
    [_L_COMPATIBLE_MODE] = "互換モード",
    [_L_TAG_DETAILS] = "[タグ詳細］",
    [_L_MAIN_MENU] = "[メインメニュー］",
    [_L_MODE_RANDOM] = "ランダム化（手動）",
    [_L_MODE_CYCLE] = "シーケンシャル",
    [_L_MODE_NTAG] = "リード/ライト",
    [_L_MODE_RANDOM_AUTO_GEN] = "ランダム化（自動）",
    [_L_BLANK_TAG] = "ブランクNFCタグ",
    [_L_APP_AMIIDB] = "Amiiboデータベース",
    [_L_APP_AMMIDB_BROWSER] = "ブラウザ...",
    [_L_APP_AMIIDB_SEARCH] = "検索...",
    [_L_APP_AMIIDB_MY_FAVORITES] = "お気に入り...",
    [_L_APP_AMIIDB_MY_TAGS] = "マイAmiibo...",
    [_L_APP_AMIIDB_SETTINGS] = "設定...",
    [_L_APP_AMIIDB_EXIT] = "[終了]",
    [_L_APP_AMIIDB_BACK] = "[戻る]",
    [_L_APP_AMIIDB_SETTINGS_AMIIBO_KEY] = "キー",
    [_L_APP_AMIIDB_SETTINGS_AMIIBO_KEY_LOADED] = "ロードされました",
    [_L_APP_AMIIDB_SETTINGS_AMIIBO_KEY_NOT_LOADED] = "ロードされていません",
    [_L_APP_AMIIDB_SETTINGS_SLOT_NUM] = "スロット番号",
    [_L_APP_AMIIDB_DETAIL_FAVORITE] = "お気に入り...",
    [_L_APP_AMIIDB_DETAIL_SAVE_AS] = "名前を付けて保存...",
    [_L_APP_AMIIDB_DETAIL_BACK_DETAIL] = "[詳細に戻る］",
    [_L_APP_AMIIDB_DETAIL_BACK_LIST] = "[リストに戻る］",
    [_L_APP_AMIIDB_SEARCH_HEAD] = "検索する:",
    [_L_APP_AMIIDB_MORE] = "[もっと見る...］",
    [_L_APP_AMIIDB_MORE_MESSAGE] = "",
    [_L_APP_AMIIDB_EMPTY_TAG] = "<Amiiboが見つかりません>",
    [_L_APP_AMIIDB_SLOT_DELETE] = "リセット...",
    [_L_APP_AMIIDB_CONFIRM] = "確認する",
    [_L_APP_AMIIDB_CANCEL] = "キャンセルする",
    [_L_APP_AMIIDB_TIPS] = "確認する",
    [_L_APP_AMIIDB_NEW] = "新規...",
    [_L_APP_AMIIDB_EMPTY] = "空...",
    [_L_APP_AMIIDB_DELETE] = "削除...",
    [_L_APP_AMIIDB_FAV_NEW_HEAD] = "新しいお気に入りフォルダ:",
    [_L_APP_AMIIDB_FAV_EMPTY_MSG] = "お気に入りフォルダを空にしますか？",
    [_L_APP_AMIIDB_FAV_DELETE_MSG] = "削除してよろしいですか？",
    [_L_APP_AMIIDB_FAV_SELECT_FOLDER] = "お気に入りフォルダを選択...",
    [_L_APP_AMIIDB_FAV_SUCCESS] = "お気に入りに追加されました",
    [_L_APP_AMIIDB_FAV_FAILED] = "お気に入りに追加できませんでした!",
    [_L_APP_AMIIDB_SLOT_SAVE_SUCCESS] = "保存されました",
    [_L_APP_AMIIDB_SLOT_SAVE_FAILED] = "保存に失敗しました!",
    [_L_APP_AMIIDB_SORT_FIELD] = "並べ替えフィールド",
    [_L_APP_AMIIDB_SORT_DEFAULT] = "デフォルト",
    [_L_APP_AMIIDB_SORT_NAME] = "名前",
    [_L_APP_AMIIDB_NOT_SUPPORT_V3] = "",
    [_L_APP_CHAMELEON] = "カードエミュレータ",
    [_L_APP_CHAMELEON_TAG_MF1_WRITE_NORMAL] = "通常",
    [_L_APP_CHAMELEON_TAG_MF1_WRITE_DENIED] = "拒否",
    [_L_APP_CHAMELEON_TAG_MF1_WRITE_DECEIVE] = "無視",
    [_L_APP_CHAMELEON_TAG_MF1_WRITE_SHADOW] = "キャッシュ",
    [_L_APP_CHAMELEON_INITIALIZING] = "データの初期化 ...",
    [_L_APP_CHAMELEON_CARD_SLOT] = "スロット",
    [_L_APP_CHAMELEON_CARD_NICK] = "ニックネーム",
    [_L_APP_CHAMELEON_CARD_ID] = "ID",
    [_L_APP_CHAMELEON_CARD_TYPE] = "タイプ",
    [_L_APP_CHAMELEON_CARD_DATA] = "データ...",
    [_L_APP_CHAMELEON_CARD_ADVANCED] = "詳細設定...",
    [_L_APP_CHAMELEON_CARD_SLOT_SETTINGS] = "スロット設定...",
    [_L_APP_CHAMELEON_CARD_SLOT_NUM] = "スロット番号...",
    [_L_APP_CHAMELEON_CARD_SET_NICK_SUCCESS] = "ニックネームが設定されました",
    [_L_APP_CHAMELEON_CARD_SET_NICK_FAILED] = "ニックネームが設定できませんでした!",
    [_L_APP_CHAMELEON_CARD_INPUT_NICK] = "ニックネームを入力してください：",
    [_L_APP_CHAMELEON_CARD_DATA_LOAD] = "ロード...",
    [_L_APP_CHAMELEON_CARD_DATA_SAVE] = "保存...",
    [_L_APP_CHAMELEON_CARD_DATA_FACTORY] = "初期化...",
    [_L_APP_CHAMELEON_CARD_DATA_FACTORY_SUCCESS] = "初期化成功",
    [_L_APP_CHAMELEON_CARD_DATA_LOAD_NOT_FOUND] = "ファイルが見つかりません",
    [_L_APP_CHAMELEON_CARD_DATA_LOAD_SIZE_NOT_MATCH] = "ファイルサイズが一致しません",
    [_L_APP_CHAMELEON_CARD_DATA_LOAD_FAILED] = "ファイルの読み込み失敗",
    [_L_APP_CHAMELEON_CARD_DATA_LOAD_SUCCESS] = "ファイルの読み込みに成功",
    [_L_APP_CHAMELEON_CARD_DATA_SAVE_INPUT_FILE_NAME] = "入力ファイル名:",
    [_L_APP_CHAMELEON_CARD_DATA_SAVE_FAILED] = "ファイルの保存に失敗しました！",
    [_L_APP_CHAMELEON_CARD_DATA_SAVE_SUCCESS] = "ファイルが保存されました",
    [_L_APP_CHAMELEON_CARD_ADV_CUSTOM_MODE] = "カスタムモード",
    [_L_APP_CHAMELEON_CARD_ADV_LOAD_BLOCK0] = "",
    [_L_APP_CHAMELEON_CARD_ADV_LOAD_BLOCK0_SUCCESS] = "",
    [_L_APP_CHAMELEON_CARD_ID_SIZE] = "",
    [_L_APP_CHAMELEON_CARD_GEN1A_MODE] = "Gen1A 有効",
    [_L_APP_CHAMELEON_CARD_GENERATE_UID] = "UIDのランダム化",
    [_L_APP_CHAMELEON_CARD_GENERATE_UID_SUCCESS] = "UID 生成",
    [_L_APP_CHAMELEON_CARD_GEN2_MODE] = "Gen2 有効",
    [_L_APP_CHAMELEON_CARD_WRITE_MODE] = "書き込みモード",
    [_L_APP_CHAMELEON_CARD_ADV_ID_EDIT_INVALID_INPUT] = "無効な入力",
    [_L_APP_CHAMELEON_CARD_TYPE_FACTORY_DATA_CONFRIM] = "カードの種類が変更されました。\nカードデータを初期化しますか？",
    [_L_APP_CHAMELEON_CARD_DEFAULT_CARD] = "",
    [_L_APP_GAME] = "",
    [_L_APP_GAME_TINY_ARKANOID] = "",
    [_L_APP_GAME_TINY_INVADERS] = "",
    [_L_APP_GAME_TINY_LANDER] = "",
    [_L_APP_GAME_TINY_TRIS] = "",
};
