solosky/pixl.js/fw/application/src/i18n/zh_Hans.c

#include "string_id.h"
const char * const lang_zh_Hans[_L_COUNT] = {
    [_L_ON] = "开",
    [_L_OFF] = "关",
    [_L_ON_F] = "[开]",
    [_L_OFF_F] = "[关]",
    [_L_BACK] = "返回",
    [_L_ERR] = "错误",
    [_L_ERR_CODE] = "错误码",
    [_L_FAILED] = "失败",
    [_L_BYTES] = "字节",
    [_L_APP_AMIIBO] = "Amiibo模拟器",
    [_L_APP_AMIIBOLINK] = "AmiiboLink",
    [_L_APP_BLE] = "蓝牙传输",
    [_L_APP_BLE_TITLE] = "蓝牙传输",
    [_L_APP_PLAYER] = "动画播放器",
    [_L_APP_SET] = "系统设置",
    [_L_APP_SET_VERSION] = "版本",
    [_L_APP_SET_STORAGE_USED] = "已用",
    [_L_APP_SET_STORAGE] = "外置存储",
    [_L_APP_SET_OLED_CONTRAST] = "对比度",
    [_L_APP_SET_OLED_CONTRAST_TITLE] = "对比度",
    [_L_APP_SET_LCD_BACKLIGHT] = "背光亮度",
    [_L_APP_SET_LCD_BACKLIGHT_TITLE] = "背光亮度",
    [_L_APP_SET_ANIM] = "动画效果",
    [_L_APP_SET_LIPO_BAT] = "LiPO电池",
    [_L_APP_SET_SHOW_MEM_USAGE] = "内存使用率",
    [_L_APP_SET_HIBERNATE] = "快速唤醒",
    [_L_APP_SET_SLEEP_TIMEOUT] = "休眠时间",
    [_L_APP_SET_LANGUAGE] = "系统语言",
    [_L_APP_SET_GO_SLEEP] = "进入休眠",
    [_L_APP_SET_DFU] = "固件更新",
    [_L_APP_SET_REBOOT] = "重启设备",
    [_L_APP_SET_RESET_DEFAULT] = "重置默认配置",
    [_L_APP_SET_RESET_DEFAULT_SUCCESS] = "重置成功",
    [_L_APP_SET_RESET_DEFAULT_CONFIRM] = "确认重置默认设置？",
    [_L_APP_SET_ABOUT] = "关于设备",
    [_L_APP_SET_ABOUT_OPEN_SOURCE_PROJECT] = "开源项目",
    [_L_APP_SET_ABOUT_LGPL_LICENSE] = "GPL 2.0 授权",
    [_L_APP_SET_APP_MGMT] = "应用管理",
    [_L_15S] = "15秒",
    [_L_30S] = "30秒",
    [_L_45S] = "45秒",
    [_L_1MIN] = "1分钟",
    [_L_2MIN] = "2分钟",
    [_L_3MIN] = "3分钟",
    [_L_AMIIBO_KEY_UNLOADED] = "Amiibo Key未加载",
    [_L_UPLOAD_KEY_RETAIL_BIN] = "上传文件 key_retail.bin\n到存储根目录下。",
    [_L_KNOW] = "知道了",
    [_L_RANDOM_GENERATION] = "随机生成",
    [_L_AUTO_RANDOM_GENERATION] = "自动随机生成",
    [_L_SET_CUSTOM_ID] = "自定义 ID",
    [_L_INPUT_ID] = "输入 ID",
    [_L_INAVLID_ID] = "无效的 ID",
    [_L_SHOW_QRCODE] = "显示二维码",
    [_L_READ_ONLY] = "禁止写入",
    [_L_DELETE_TAG] = "删除标签",
    [_L_DELETE_TAG_CONFIRM] = "确认删除 %s ?",
    [_L_BACK_TO_DETAILS] = "返回详情",
    [_L_BACK_TO_FILE_LIST] = "返回文件列表",
    [_L_BACK_TO_MAIN_MENU] = "返回主菜单",
    [_L_FORMAT] = "格式化",
    [_L_FORMAT_STORAGE] = "格式化存储",
    [_L_DELETE_ALL_DATA] = "将删除所有数据。\n确认格式化?",
    [_L_DELETING_MESSAGE] = "格式化中...",
    [_L_MESSAGE] = "提示",
    [_L_CONFIRM] = "确定",
    [_L_CANCEL] = "取消",
    [_L_BACK_TO_LIST] = "返回列表",
    [_L_NOT_MOUNTED] = "未挂载",
    [_L_MOUNTED_LFS] = "===已挂载[LFS]===",
    [_L_MOUNTED_FFS] = "===已挂载[FFS]===",
    [_L_TOTAL_SPACE] = "总空间",
    [_L_AVAILABLE_SPACE] = "可用空间",
    [_L_NOT_AMIIBO_FILE] = "这不是Amiibo文件",
    [_L_READ_FILE_FAILED] = "读取文件失败",
    [_L_INPUT_FOLDER_NAME] = "输入文件夹名:",
    [_L_INPUT_AMIIBO_NAME] = "输入amiibo名:",
    [_L_DELETE_FILE] = "删除 %s ?",
    [_L_DELETE] = "删除...",
    [_L_TIPS] = "提示",
    [_L_INPUT_NEW_NAME] = "输入新名:",
    [_L_INVALID_INPUT] = "无效的输入",
    [_L_CREATE_NEW_FOLDER] = "新建文件夹...",
    [_L_CREATE_NEW_TAG] = "新建标签...",
    [_L_CREATE_NEW_TAG_BATCH] = "批量创建标签...",
    [_L_INPUT_TAG_NUM] = "输入标签数量:",
    [_L_CREATE_TOO_MANY_NUM] = "一次最多只能创建%d个标签",
    [_L_CREATING_TAG_BATCH] = "创建标签",
    [_L_CREATING_TAG_FAILED] = "写入 %s 标签失败",
    [_L_RENAME] = "重命名...",
    [_L_OPEN_FOLDER_FAILED] = "打开文件夹失败",
    [_L_RENAME_FAILED] = "重命名失败",
    [_L_MAIN_RETURN] = "[返回]",
    [_L_RANDOM_MODE_MANUAL] = "随机模式(手动)",
    [_L_RANDOM_MODE_AUTO] = "随机模式(自动)",
    [_L_SEQUENCE_MODE] = "按序模式",
    [_L_READ_WRITE_MODE] = "读写模式",
    [_L_AMIIBOLINK_V1] = "V1(历史版本)",
    [_L_AMIIBOLINK_V2] = "V2(最新版本)",
    [_L_AMILOOP] = "AmiLoop",
    [_L_MODE] = "模式",
    [_L_AUTO_RANDOM] = "自动随机",
    [_L_COMPATIBLE_MODE] = "兼容模式",
    [_L_TAG_DETAILS] = "[标签详情]",
    [_L_MAIN_MENU] = "[主菜单]",
    [_L_MODE_RANDOM] = "随机(手动)",
    [_L_MODE_CYCLE] = "按序",
    [_L_MODE_NTAG] = "读写",
    [_L_MODE_RANDOM_AUTO_GEN] = "随机(自动)",
    [_L_BLANK_TAG] = "空标签",
    [_L_APP_AMIIDB] = "Amiibo数据库",
    [_L_APP_AMMIDB_BROWSER] = "查看...",
    [_L_APP_AMIIDB_SEARCH] = "搜索...",
    [_L_APP_AMIIDB_MY_FAVORITES] = "我的收藏...",
    [_L_APP_AMIIDB_MY_TAGS] = "我的数据...",
    [_L_APP_AMIIDB_SETTINGS] = "设置...",
    [_L_APP_AMIIDB_EXIT] = "[退出]",
    [_L_APP_AMIIDB_BACK] = "[返回]",
    [_L_APP_AMIIDB_SETTINGS_AMIIBO_KEY] = "密钥文件",
    [_L_APP_AMIIDB_SETTINGS_AMIIBO_KEY_LOADED] = "已加载",
    [_L_APP_AMIIDB_SETTINGS_AMIIBO_KEY_NOT_LOADED] = "未加载",
    [_L_APP_AMIIDB_SETTINGS_SLOT_NUM] = "数据槽位",
    [_L_APP_AMIIDB_DETAIL_FAVORITE] = "收藏...",
    [_L_APP_AMIIDB_DETAIL_SAVE_AS] = "保存为...",
    [_L_APP_AMIIDB_DETAIL_BACK_DETAIL] = "[返回详情]",
    [_L_APP_AMIIDB_DETAIL_BACK_LIST] = "[返回列表]",
    [_L_APP_AMIIDB_SEARCH_HEAD] = "搜索:",
    [_L_APP_AMIIDB_MORE] = "[更多]",
    [_L_APP_AMIIDB_MORE_MESSAGE] = "搜索结果过多，尝试增加搜索词。",
    [_L_APP_AMIIDB_EMPTY_TAG] = "<空标签>",
    [_L_APP_AMIIDB_SLOT_DELETE] = "重置...",
    [_L_APP_AMIIDB_CONFIRM] = "确认",
    [_L_APP_AMIIDB_CANCEL] = "取消",
    [_L_APP_AMIIDB_TIPS] = "提示",
    [_L_APP_AMIIDB_NEW] = "新建...",
    [_L_APP_AMIIDB_EMPTY] = "清空...",
    [_L_APP_AMIIDB_DELETE] = "删除...",
    [_L_APP_AMIIDB_FAV_NEW_HEAD] = "新建收藏夹:",
    [_L_APP_AMIIDB_FAV_EMPTY_MSG] = "确认清空收藏夹?",
    [_L_APP_AMIIDB_FAV_DELETE_MSG] = "确认删除?",
    [_L_APP_AMIIDB_FAV_SELECT_FOLDER] = "选择收藏夹...",
    [_L_APP_AMIIDB_FAV_SUCCESS] = "收藏成功",
    [_L_APP_AMIIDB_FAV_FAILED] = "收藏失败",
    [_L_APP_AMIIDB_SLOT_SAVE_SUCCESS] = "保存成功",
    [_L_APP_AMIIDB_SLOT_SAVE_FAILED] = "保存失败",
    [_L_APP_AMIIDB_SORT_FIELD] = "排序字段",
    [_L_APP_AMIIDB_SORT_DEFAULT] = "默认",
    [_L_APP_AMIIDB_SORT_NAME] = "名字",
    [_L_APP_AMIIDB_NOT_SUPPORT_V3] = "暂不支持V3 amiibo!",
    [_L_APP_CHAMELEON] = "卡模拟器",
    [_L_APP_CHAMELEON_TAG_MF1_WRITE_NORMAL] = "正常",
    [_L_APP_CHAMELEON_TAG_MF1_WRITE_DENIED] = "拒绝",
    [_L_APP_CHAMELEON_TAG_MF1_WRITE_DECEIVE] = "忽略",
    [_L_APP_CHAMELEON_TAG_MF1_WRITE_SHADOW] = "缓存",
    [_L_APP_CHAMELEON_INITIALIZING] = "初始化请稍后...",
    [_L_APP_CHAMELEON_CARD_SLOT] = "卡槽",
    [_L_APP_CHAMELEON_CARD_NICK] = "卡名",
    [_L_APP_CHAMELEON_CARD_ID] = "ID",
    [_L_APP_CHAMELEON_CARD_TYPE] = "卡类型",
    [_L_APP_CHAMELEON_CARD_DATA] = "卡数据...",
    [_L_APP_CHAMELEON_CARD_ADVANCED] = "卡高级设置...",
    [_L_APP_CHAMELEON_CARD_SLOT_SETTINGS] = "卡槽管理...",
    [_L_APP_CHAMELEON_CARD_SLOT_NUM] = "卡槽数量...",
    [_L_APP_CHAMELEON_CARD_SET_NICK_SUCCESS] = "设置卡名成功",
    [_L_APP_CHAMELEON_CARD_SET_NICK_FAILED] = "设置卡名失败",
    [_L_APP_CHAMELEON_CARD_INPUT_NICK] = "输入卡名:",
    [_L_APP_CHAMELEON_CARD_DATA_LOAD] = "加载...",
    [_L_APP_CHAMELEON_CARD_DATA_SAVE] = "导出...",
    [_L_APP_CHAMELEON_CARD_DATA_FACTORY] = "重置...",
    [_L_APP_CHAMELEON_CARD_DATA_FACTORY_SUCCESS] = "卡片初始化成功",
    [_L_APP_CHAMELEON_CARD_DATA_LOAD_NOT_FOUND] = "文件不存在",
    [_L_APP_CHAMELEON_CARD_DATA_LOAD_SIZE_NOT_MATCH] = "文件大小不匹配",
    [_L_APP_CHAMELEON_CARD_DATA_LOAD_FAILED] = "读取文件失败",
    [_L_APP_CHAMELEON_CARD_DATA_LOAD_SUCCESS] = "加载卡片数据成功",
    [_L_APP_CHAMELEON_CARD_DATA_SAVE_INPUT_FILE_NAME] = "输入文件名",
    [_L_APP_CHAMELEON_CARD_DATA_SAVE_FAILED] = "写入文件失败",
    [_L_APP_CHAMELEON_CARD_DATA_SAVE_SUCCESS] = "导出卡片数据成功",
    [_L_APP_CHAMELEON_CARD_ADV_CUSTOM_MODE] = "自定义模式",
    [_L_APP_CHAMELEON_CARD_ADV_LOAD_BLOCK0] = "加载0扇区数据...",
    [_L_APP_CHAMELEON_CARD_ADV_LOAD_BLOCK0_SUCCESS] = "加载0扇区数据成功",
    [_L_APP_CHAMELEON_CARD_ID_SIZE] = "ID类型",
    [_L_APP_CHAMELEON_CARD_GEN1A_MODE] = "Gen1A模式",
    [_L_APP_CHAMELEON_CARD_GENERATE_UID] = "生成UID",
    [_L_APP_CHAMELEON_CARD_GENERATE_UID_SUCCESS] = "UID已生成",
    [_L_APP_CHAMELEON_CARD_GEN2_MODE] = "Gen2模式",
    [_L_APP_CHAMELEON_CARD_WRITE_MODE] = "写入模式",
    [_L_APP_CHAMELEON_CARD_ADV_ID_EDIT_INVALID_INPUT] = "无效的输入!",
    [_L_APP_CHAMELEON_CARD_TYPE_FACTORY_DATA_CONFRIM] = "卡类型已修改\n重置卡数据?",
    [_L_APP_CHAMELEON_CARD_DEFAULT_CARD] = "默认卡片",
    [_L_APP_GAME] = "游戏",
    [_L_APP_GAME_TINY_ARKANOID] = "打砖块",
    [_L_APP_GAME_TINY_INVADERS] = "入侵者",
    [_L_APP_GAME_TINY_LANDER] = "星球着陆",
    [_L_APP_GAME_TINY_TRIS] = "俄罗斯方块",
};
