solosky/pixl.js/fw/application/src/mui/mui_resource.c

#include "mui_resource.h"
//************************************************************************
//** /resources/bmp/app_amiibo_database_32x32.bmp
//************************************************************************
const uint8_t app_amiibo_database_32x32_data[] = {
0x00,0x00,0x00,0x00,0x00,0x00,0x00,0x00,0x00,0x00,0x00,0x00,0x00,0x00,0x00,
0x00,0x00,0x00,0x00,0x00,0xc0,0xff,0xff,0x03,0x20,0x00,0x00,0x04,0xa0,0x3e,
0x00,0x04,0x20,0x00,0x00,0x04,0x20,0x00,0x00,0x04,0xc0,0xff,0xff,0x03,0x80,
0xff,0xff,0x01,0xc0,0xff,0xff,0x03,0x20,0x00,0x00,0x04,0xa0,0x3e,0x1e,0x04,
0x20,0x00,0x3f,0x04,0x20,0x80,0x73,0x04,0xc0,0xbf,0x61,0x03,0x80,0xbf,0x61,
0x01,0xc0,0xbf,0x63,0x03,0x20,0x00,0x6f,0x04,0xa0,0x3e,0x6e,0x04,0x20,0x00,
0x00,0x04,0x20,0x00,0x00,0x04,0xc0,0xff,0xff,0x03,0x80,0xff,0xff,0x01,0x68,
0xff,0xff,0x1a,0x00,0x00,0x00,0x00,0x00,0x00,0x00,0x00,0x00,0x00,0x00,0x00,
0x00,0x00,0x00,0x00,0x00,0x00,0x00,0x00
};
const xbm_t app_amiibo_database_32x32 = {.width = 32, .height = 32, .data = app_amiibo_database_32x32_data};


//************************************************************************
//** /resources/bmp/app_amiibo_emulator_32x32.bmp
//************************************************************************
const uint8_t app_amiibo_emulator_32x32_data[] = {
0x00,0x00,0x00,0x00,0x00,0x00,0x00,0x00,0x00,0x00,0x00,0x00,0x00,0x00,0x00,
0x00,0x00,0x00,0x00,0x00,0x00,0x00,0x00,0x00,0x00,0x00,0x00,0x00,0x00,0x00,
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
0x03,0x00,0x80,0xc1,0x83,0x01,0xc0,0xf3,0xcf,0x03,0xc0,0xff,0xff,0x03,0x80,
0xff,0xff,0x01,0x00,0xff,0xff,0x00,0x00,0x1f,0xf8,0x00,0x80,0xcf,0xf3,0x01,
0xe0,0xe7,0xe7,0x07,0x00,0x00,0x00,0x00
};
const xbm_t app_settings_32x32 = {.width = 32, .height = 32, .data = app_settings_32x32_data};
