solosky/pixl.js/fw/application/src/i18n/string_id.h

#ifndef LANGUAGE_STRING_ID_H
#define LANGUAGE_STRING_ID_H
typedef enum {
    _L_ON,
    _L_OFF,
    _L_ON_F,
    _L_OFF_F,
    _L_BACK,
    _L_ERR,
    _L_ERR_CODE,
    _L_FAILED,
    _L_BYTES,
    _L_APP_AMIIBO,
    _L_APP_AMIIBOLINK,
    _L_APP_BLE,
    _L_APP_BLE_TITLE,
    _L_APP_PLAYER,
    _L_APP_SET,
    _L_APP_SET_VERSION,
    _L_APP_SET_STORAGE_USED,
    _L_APP_SET_STORAGE,
    _L_APP_SET_OLED_CONTRAST,
    _L_APP_SET_OLED_CONTRAST_TITLE,
    _L_APP_SET_LCD_BACKLIGHT,
    _L_APP_SET_LCD_BACKLIGHT_TITLE,
    _L_APP_SET_ANIM,
    _L_APP_SET_LIPO_BAT,
    _L_APP_SET_SHOW_MEM_USAGE,
    _L_APP_SET_HIBERNATE,
    _L_APP_SET_SLEEP_TIMEOUT,
    _L_APP_SET_LANGUAGE,
    _L_APP_SET_GO_SLEEP,
    _L_APP_SET_DFU,
    _L_APP_SET_REBOOT,
    _L_APP_SET_RESET_DEFAULT,
    _L_APP_SET_RESET_DEFAULT_SUCCESS,
    _L_APP_SET_RESET_DEFAULT_CONFIRM,
    _L_APP_SET_ABOUT,
    _L_APP_SET_ABOUT_OPEN_SOURCE_PROJECT,
    _L_APP_SET_ABOUT_LGPL_LICENSE,
    _L_APP_SET_APP_MGMT,
    _L_15S,
    _L_30S,
    _L_45S,
    _L_1MIN,
    _L_2MIN,
    _L_3MIN,
    _L_AMIIBO_KEY_UNLOADED,
    _L_UPLOAD_KEY_RETAIL_BIN,
    _L_KNOW,
    _L_RANDOM_GENERATION,
    _L_AUTO_RANDOM_GENERATION,
    _L_SET_CUSTOM_ID,
    _L_INPUT_ID,
    _L_INAVLID_ID,
    _L_SHOW_QRCODE,
    _L_READ_ONLY,
    _L_DELETE_TAG,
    _L_DELETE_TAG_CONFIRM,
    _L_BACK_TO_DETAILS,
    _L_BACK_TO_FILE_LIST,
    _L_BACK_TO_MAIN_MENU,
    _L_FORMAT,
    _L_FORMAT_STORAGE,
    _L_DELETE_ALL_DATA,
    _L_DELETING_MESSAGE,
    _L_MESSAGE,
    _L_CONFIRM,
    _L_CANCEL,
    _L_BACK_TO_LIST,
    _L_NOT_MOUNTED,
    _L_MOUNTED_LFS,
    _L_MOUNTED_FFS,
    _L_TOTAL_SPACE,
    _L_AVAILABLE_SPACE,
    _L_NOT_AMIIBO_FILE,
    _L_READ_FILE_FAILED,
    _L_INPUT_FOLDER_NAME,
    _L_INPUT_AMIIBO_NAME,
    _L_DELETE_FILE,
    _L_DELETE,
    _L_TIPS,
    _L_INPUT_NEW_NAME,
    _L_INVALID_INPUT,
    _L_CREATE_NEW_FOLDER,
    _L_CREATE_NEW_TAG,
    _L_CREATE_NEW_TAG_BATCH,
    _L_INPUT_TAG_NUM,
    _L_CREATE_TOO_MANY_NUM,
    _L_CREATING_TAG_BATCH,
    _L_CREATING_TAG_FAILED,
    _L_RENAME,
    _L_OPEN_FOLDER_FAILED,
    _L_RENAME_FAILED,
    _L_MAIN_RETURN,
    _L_RANDOM_MODE_MANUAL,
    _L_RANDOM_MODE_AUTO,
    _L_SEQUENCE_MODE,
    _L_READ_WRITE_MODE,
    _L_AMIIBOLINK_V1,
    _L_AMIIBOLINK_V2,
    _L_AMILOOP,
    _L_MODE,
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
